cledantec/Cycle-Atlanta-SLaB/Spring2017_implementations/Surface Quality/presentations/Milestone 1.pdf

## LMC 6650: Seeing like a Bike

# Surface Quality

## Milestone 1

Team: Shruti Dalvi | Kristin Hare | Nene Igietseme | Jayanth Mohana Krishna

What to measure | Why we’re measuring it | How (sensor type)
Swerve (rate of deflection) | Recorrecting course to show road obstacles and
potholes
| | Magnetometer / Gyroscope
Vibration | Surface quality (type of surface) | Vibration Sensor / Contact microphone (http://www.digikey.com/product-detail/en/knowles/BU-21771-000/423-1004-ND/458515)
Location | Location of data collected | GPS chip
Directional sound | Ambient noise, surface quality | Array microphones (to be trained)
Incline | Slope of road | Inclinometer
Pressure on handlebars | Physiological measure of stress | Area pressure sensor (https://www.sparkfun.com/products/11207)

## Primary Measures

What to measure | Why we’re measuring it | How (sensor type)
Speed | Cyclist behavior could reflect how
| critical the condition of the road is (related to traffic speed or road obstacles) | Accelerometer / Hall effect sensor / Reid Switch
Temperature | Could be related to road conditions (potential for ice, long stretches of hot pavement, etc.)
Temperature and humidity sensor (single package) (https://www.sparkfun.com/products/10167)
Humidity | Weather (raining), could be used to back up data on cyclist actions (swerving)
Direction | To detect the side of the road (since GPS will only give absolute location)

Accelerometer / Gyroscope (https://www.sparkfun.com/products/retired/10724)

Gear Number | Could point to information on incline or cyclist exertion level

Rheostat / variable resistor (http://www.digikey.com/products/en/potentiometers-variable-resistors/slide-potentiometers/78)

## Secondary Measures

## Shopping List

Option 1:

- Matrix One Creator Edition ($99)
- Raspberry Pi 3 ($35)
- Arduino Mega*
- Powered USB hub for dev
- External battery pack*
- Inclinometer
- GPS chip
- Pressure sensors for handlebars
- Low-sensitivity vibration sensors

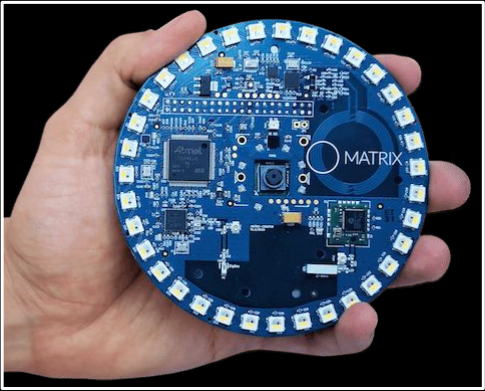
[picture p22: figure]

Option 2: Buy individual sensors | Matrix One Creator Edition - Integrated sensors for RPi

## Miscellaneous parts

- ⅛” cube magnets, 20x
- M/M, M/F, F/F patch cables, 20x
- Hair bands, 20x
- Cable ties, 20x
- Breadboards to prototype
- 5V 2A+ power supply, MicroUSB
- MicroSD card, 16 GB
- 3D printed parts (GVU lab)
- ???

### Alternate method (to be explored):

- 20mW 3-5V laser diode, paired with USB camera
- Machine Vision to observe changes in laser pattern on surface) - apparently not hard to do on OpenCV/Raspberry Pi
- Most obvious way, but potentially risky - can only get surface quality

Sensor Location | Raspberry Pi +

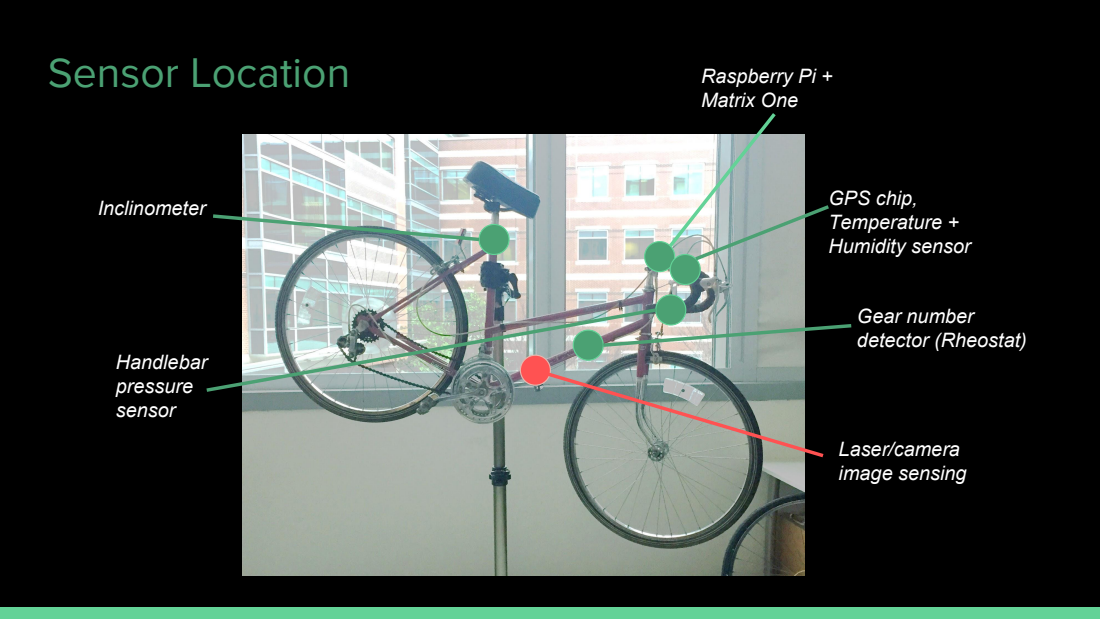
[picture p23: page 6]
Matrix One; Inclinometer; Gear number detector (Rheostat); GPS chip, Temperature + Humidity sensor; Handlebar pressure sensor; Laser/camera image sensing

## Progress

- Tested high-sensitivity vibration sensor, discovered we needed much lower sensitivity
- Reclassified measures as primary and secondary based on feedback from Dr. Watkins
- Reached out to civil engineering students for additional feedback on measures

## To-do

- Sketches - how to interface sensors
- System Architecture (in collaboration with other teams)
- Calibration parameters
