cledantec/Cycle-Atlanta-SLaB/Spring2017_implementations/Surface Quality/presentations/Milestone 2.pdf

LMC 6650: Seeing like a Bike

# Surface Quality

Milestone 2

Team: Shruti Dalvi | Kristin Hare | Nene Igietseme | Jayanth Mohana Krishna

Progress: Meeting with Dr. Watkins’ Students

- Talked to Dr. Watkins’ students
- The laser surface quality detector they use is not feasible for this project (size of a microwave oven & 100,000 dollars)

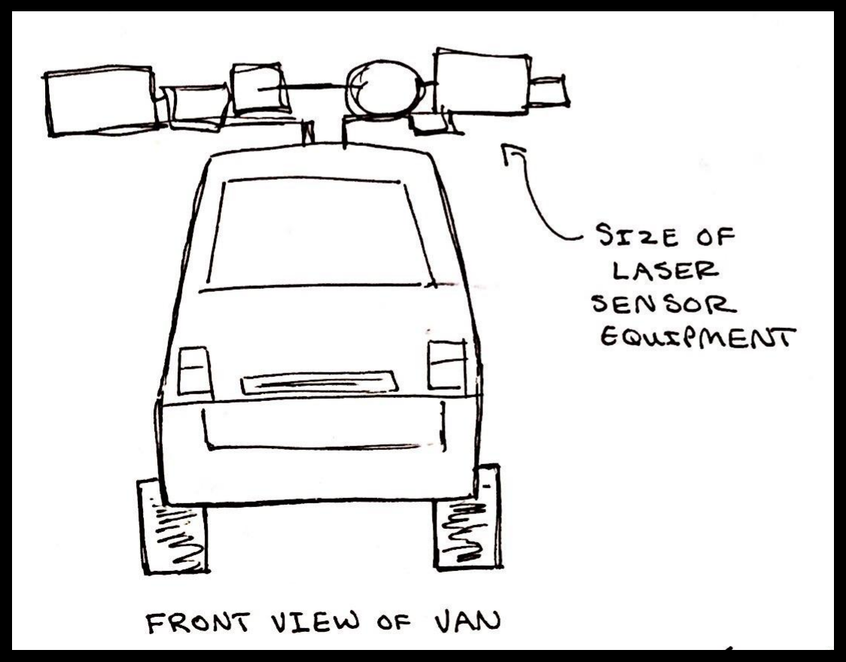
[picture p24: figure]

Laser measures distance from laser to pavement; is not affected by light or reflection like a camera would be

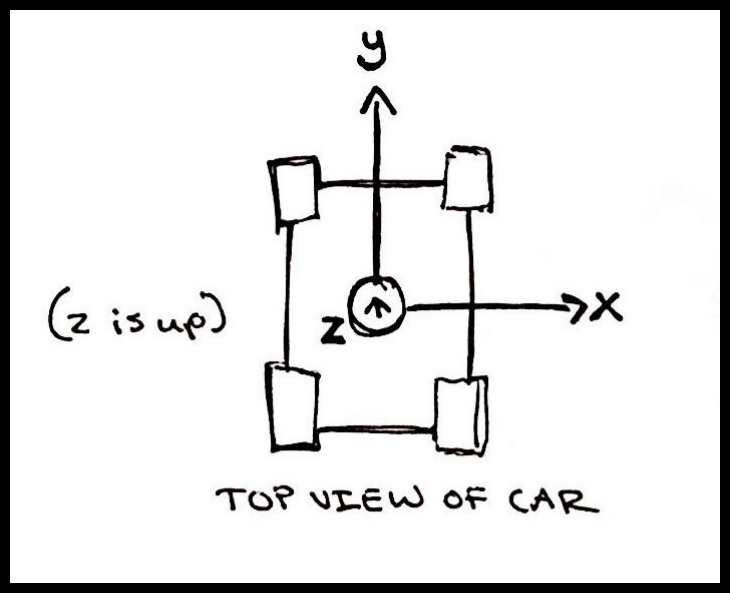
[picture p25: figure]

To calculate magnitude of
deviation in bumps: (x²

+ y²

+ z²
) =
t

2
(do not use square root because of powerful calculations needed)

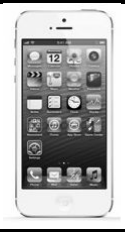
[picture p26: figure]

Phone Location Services
could be better than GPS
chip because based on
satellite, server towers, & wifi

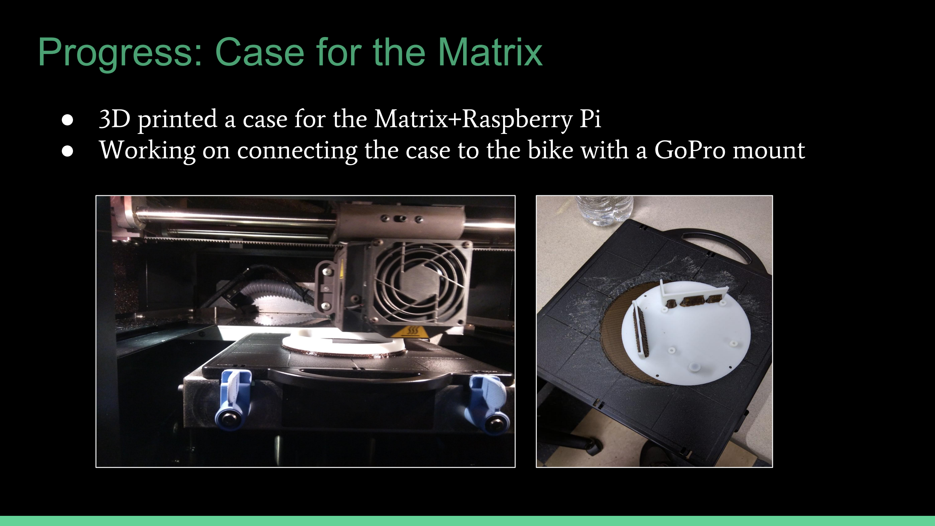
[picture p27: page 3]

Progress: Case for the Matrix

- 3D printed a case for the Matrix+Raspberry Pi
- Working on connecting the case to the bike with a GoPro mount

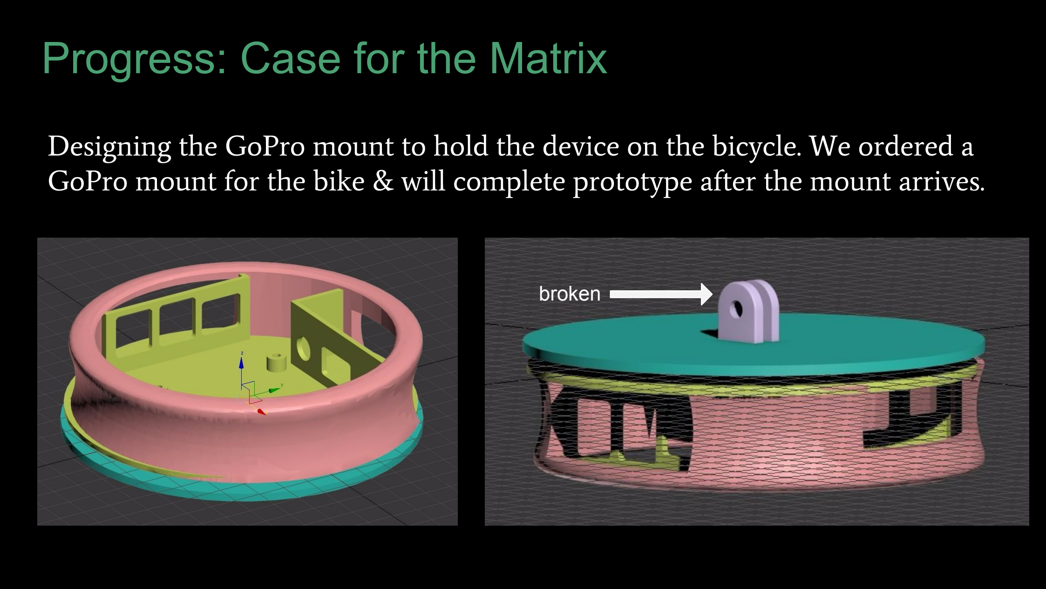
[picture p28: page 4]

broken

Designing the GoPro mount to hold the device on the bicycle. We ordered a GoPro mount for the bike & will complete prototype after the mount arrives.

Progress: Case for the Matrix

Progress

- Accelerometer and
gyroscope support for
Matrix arrived last week;
that is implemented - we
are getting raw JSON
values
- Dr. Watkins’ students
suggested logging
timestamp, GPS and
x

2+y²+z²
values if it is
greater than threshold t²
,
for purposes of efficiency.

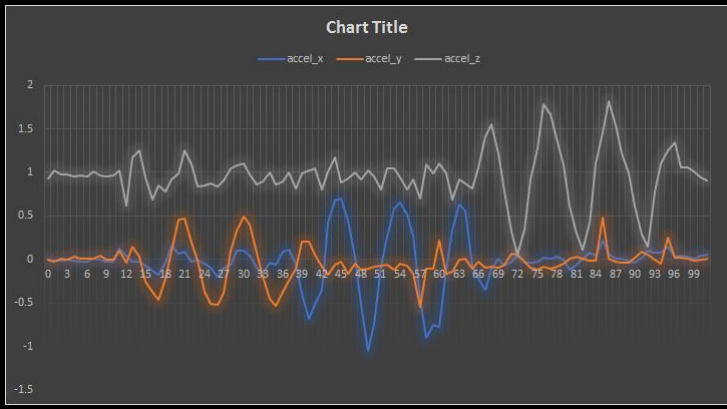
[picture p29: figure]

Currently getting accelerometer, gyroscope and magnetometer data, coordinated with Air Quality team to get GPS data

Roadblocks:

- Laser surface quality detector Dr. Watkins’ students are using is very out of budget
- 3D model’s GoPro mount broke
- We will glue it with epoxy & possibly some wooden stilts once we receive the GoPro bike mount (ETA March 2nd)

Questions to Answer:

- Got accelerometer/gyroscope/magnetometer data - need to determine appropriate interval for surface quality measurements
- Implemented serial interface for Pi - might have to interface with Arduino because Pi’s Linux kernel is not real-time

Future Direction

- Determine appropriate intervals to collect data
- Determine & assign specific values to compare data against (ex: what constitutes a pothole, what constitutes a turn vs. a swerve)
- Implement a centralized server to collect data (will have to coordinate with other teams)
- Investigate optical measurements (OpenCV)
- Investigate acoustic measurements (will need to buy a surface microphone to investigate its data stream)
