cledantec/Cycle-Atlanta-SLaB/DSSG2017_data/graphs/0719_being_passed_vehicle.png

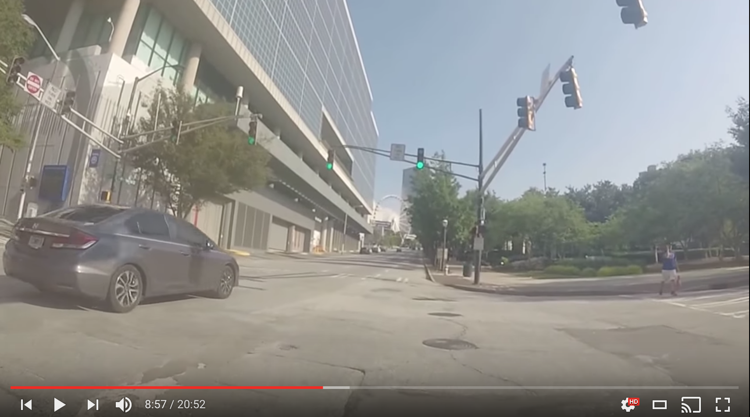
DSSG2017_data/graphs/0719_being_passed_vehicle.png
