cledantec/Cycle-Atlanta-SLaB/DSSG2017_data/graphs/0719_signature_riding.png

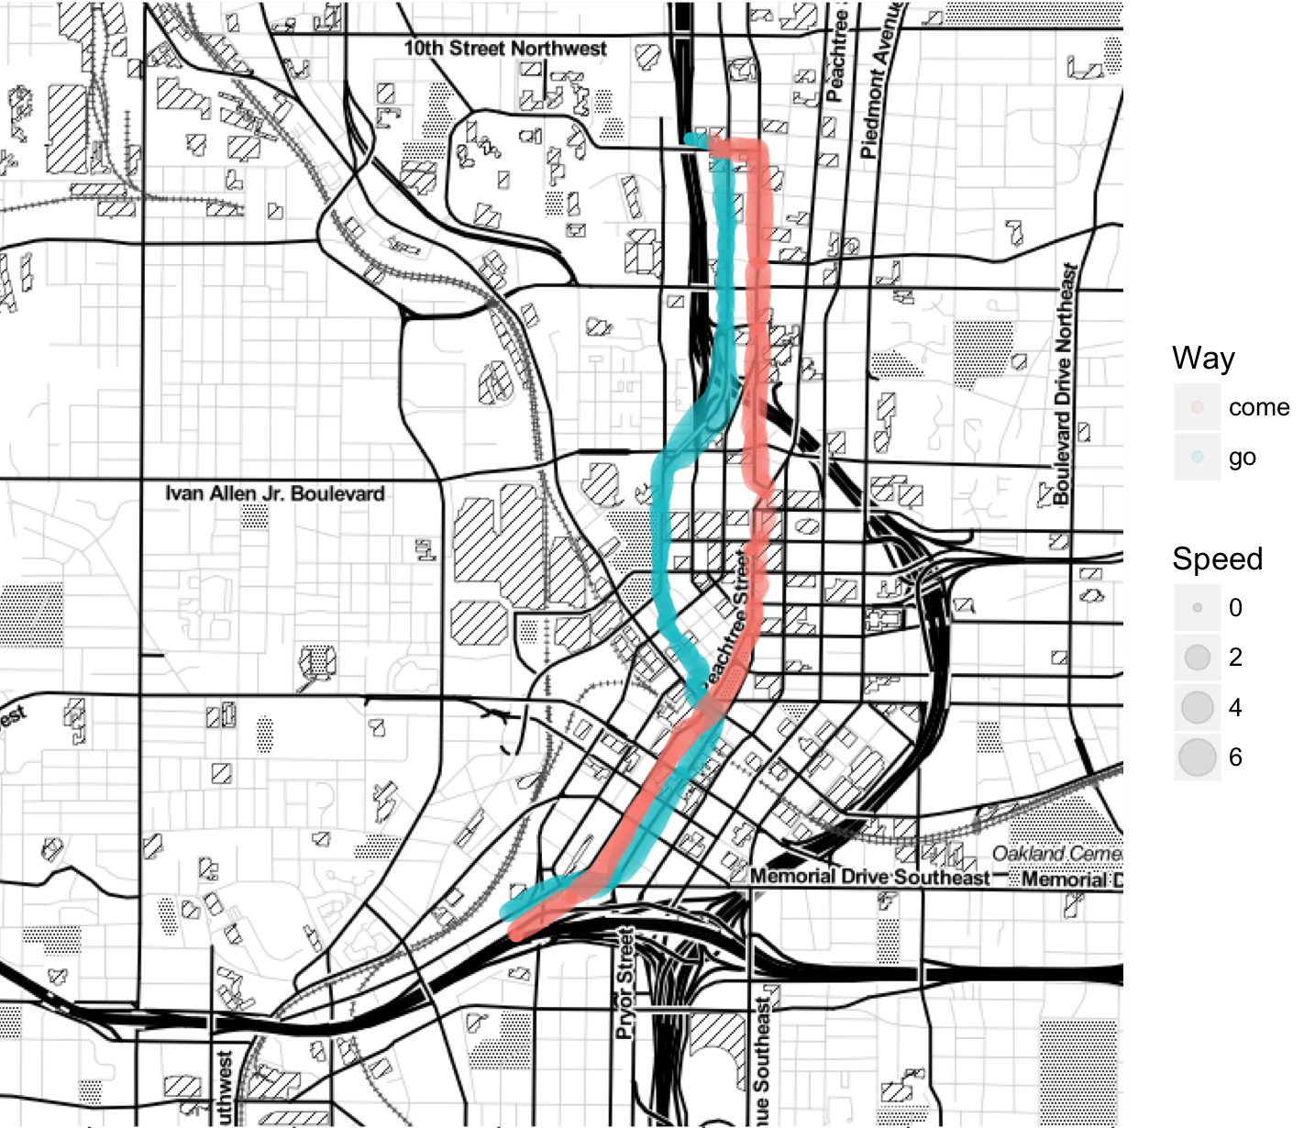
DSSG2017_data/graphs/0719_signature_riding.png
