cledantec/Cycle-Atlanta-SLaB/DSSG2017_data/graphs/0719_street_parking.png

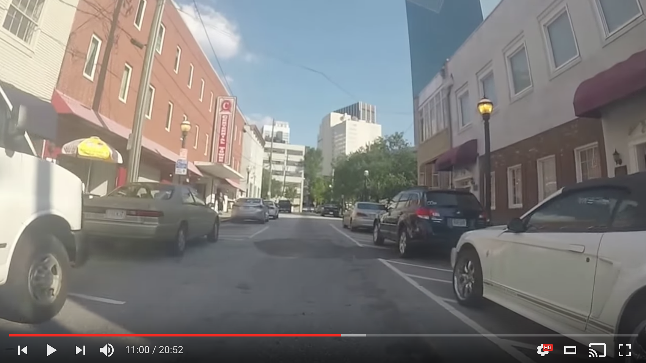
DSSG2017_data/graphs/0719_street_parking.png
