cledantec/Cycle-Atlanta-SLaB/DSSG2017_data/graphs/0720_Noel.png

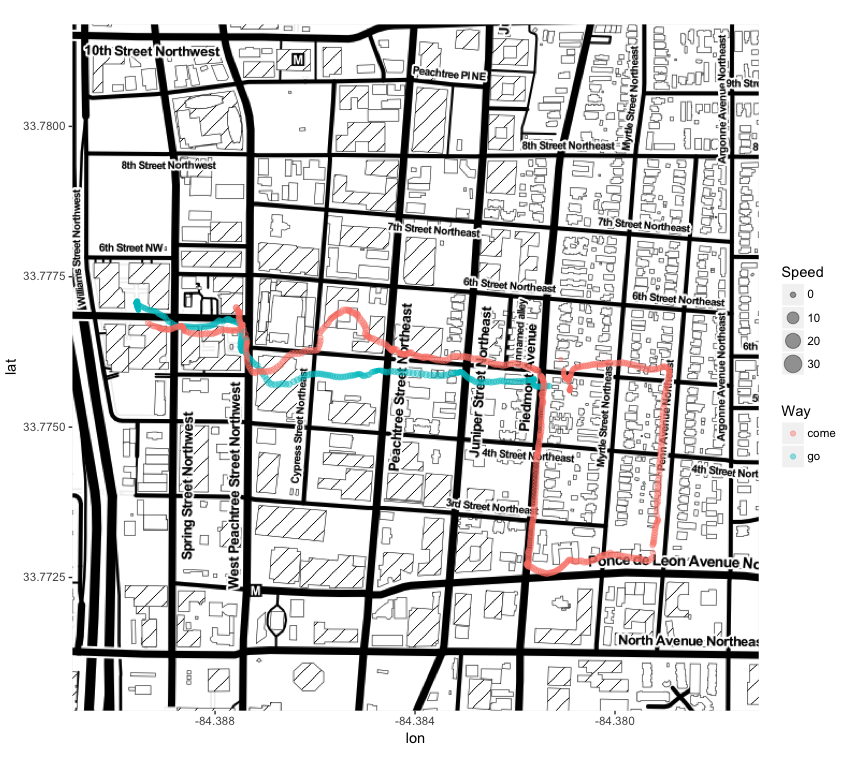
DSSG2017_data/graphs/0720_Noel.png
