cledantec/Cycle-Atlanta-SLaB/DSSG2017_data/graphs/Accelerometer.png

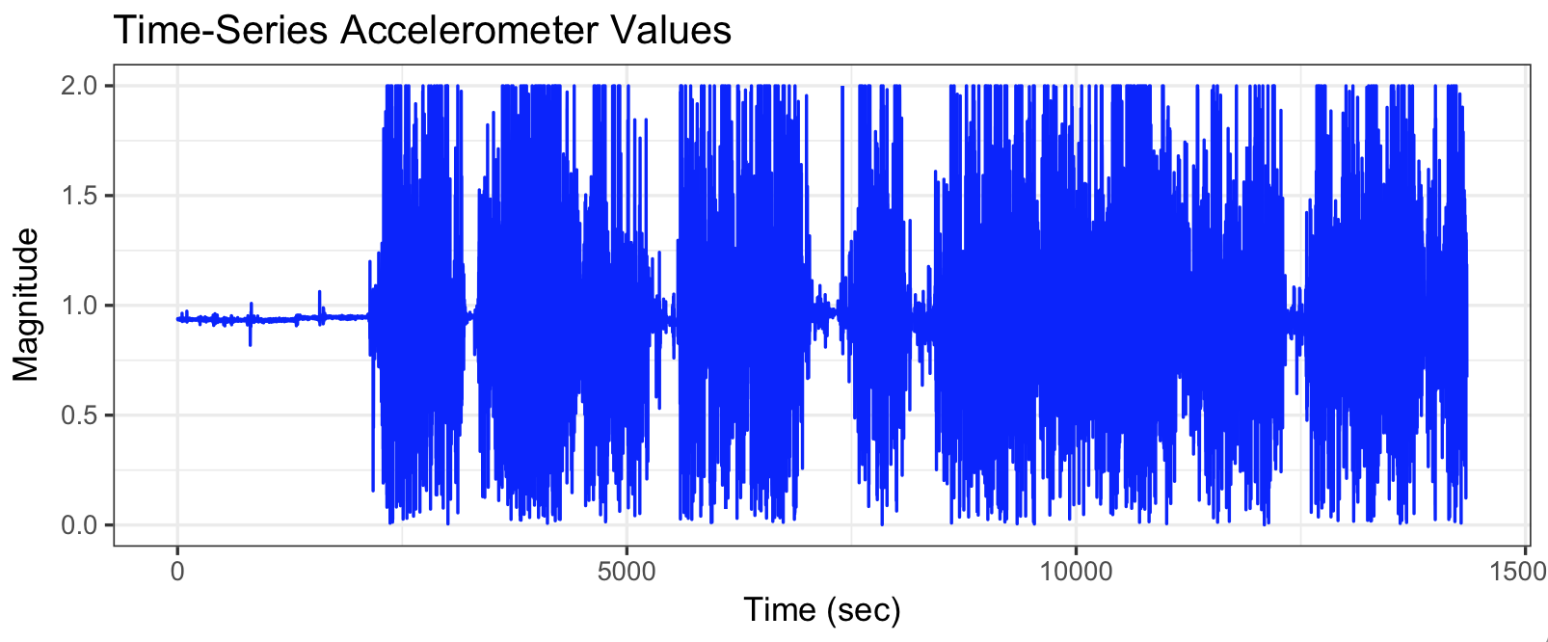
DSSG2017_data/graphs/Accelerometer.png
