cledantec/Cycle-Atlanta-SLaB/DSSG2017_data/graphs/close_up.png

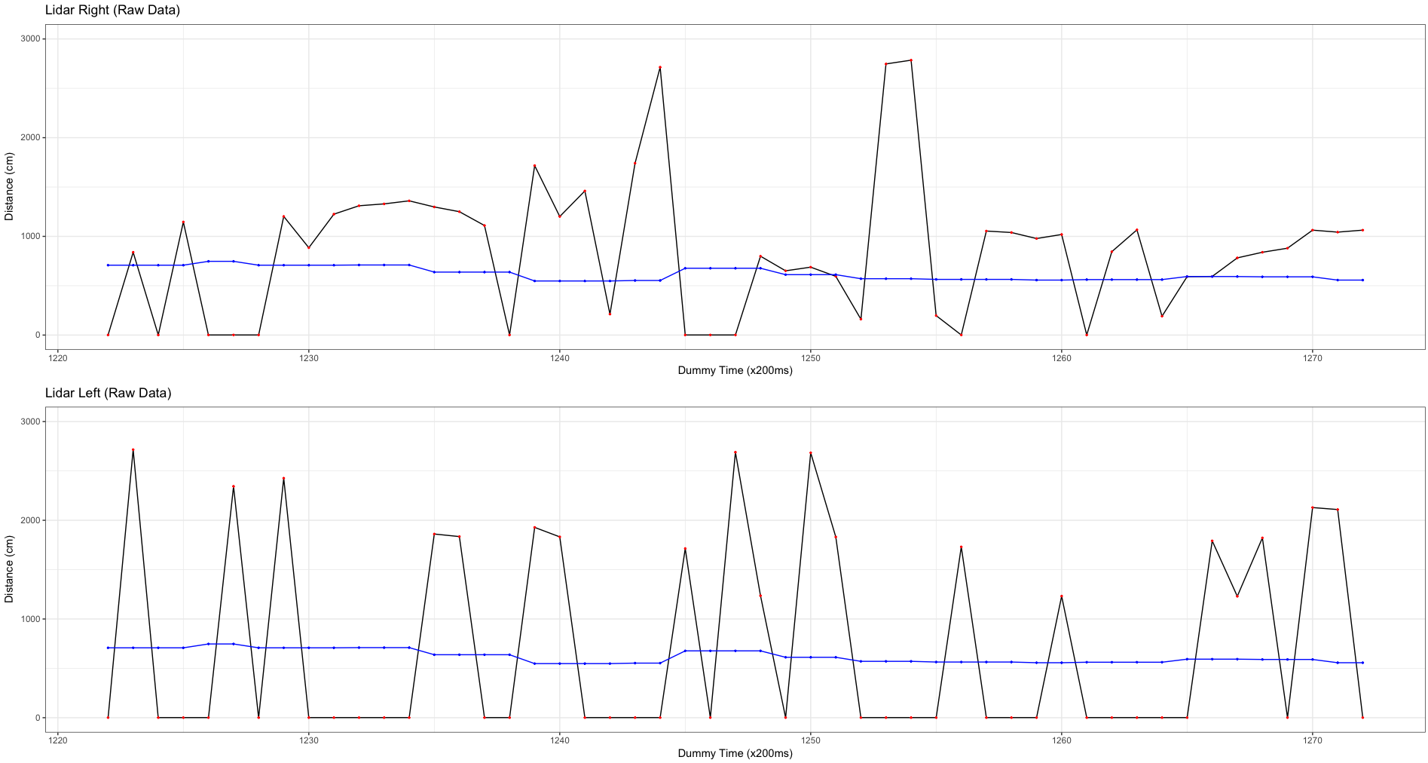
DSSG2017_data/graphs/close_up.png
