cledantec/Cycle-Atlanta-SLaB/DSSG2017_data/graphs/Gas.png

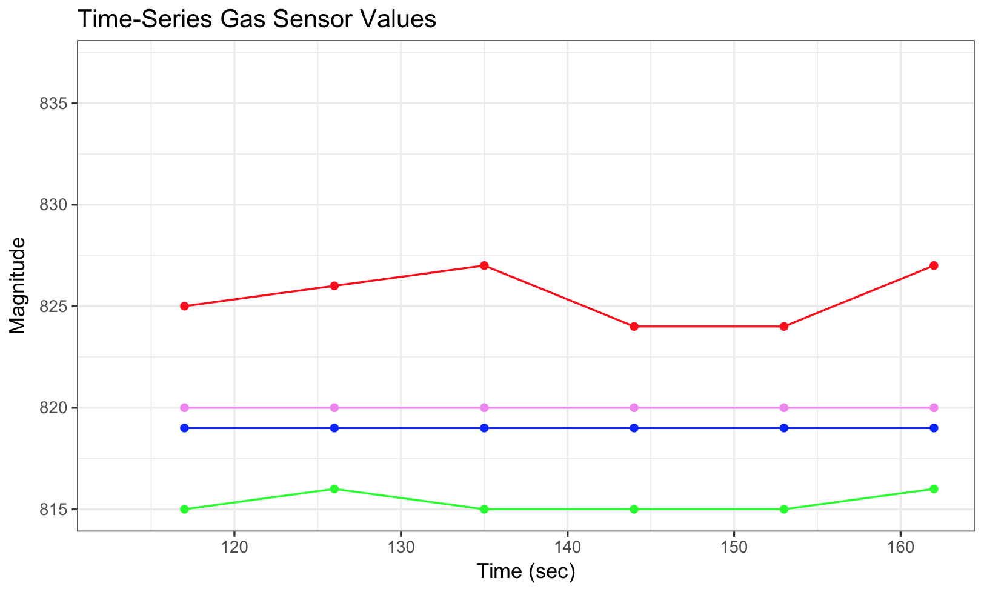
DSSG2017_data/graphs/Gas.png
