cledantec/Cycle-Atlanta-SLaB/DSSG2017_data/graphs/Gas_board5.png

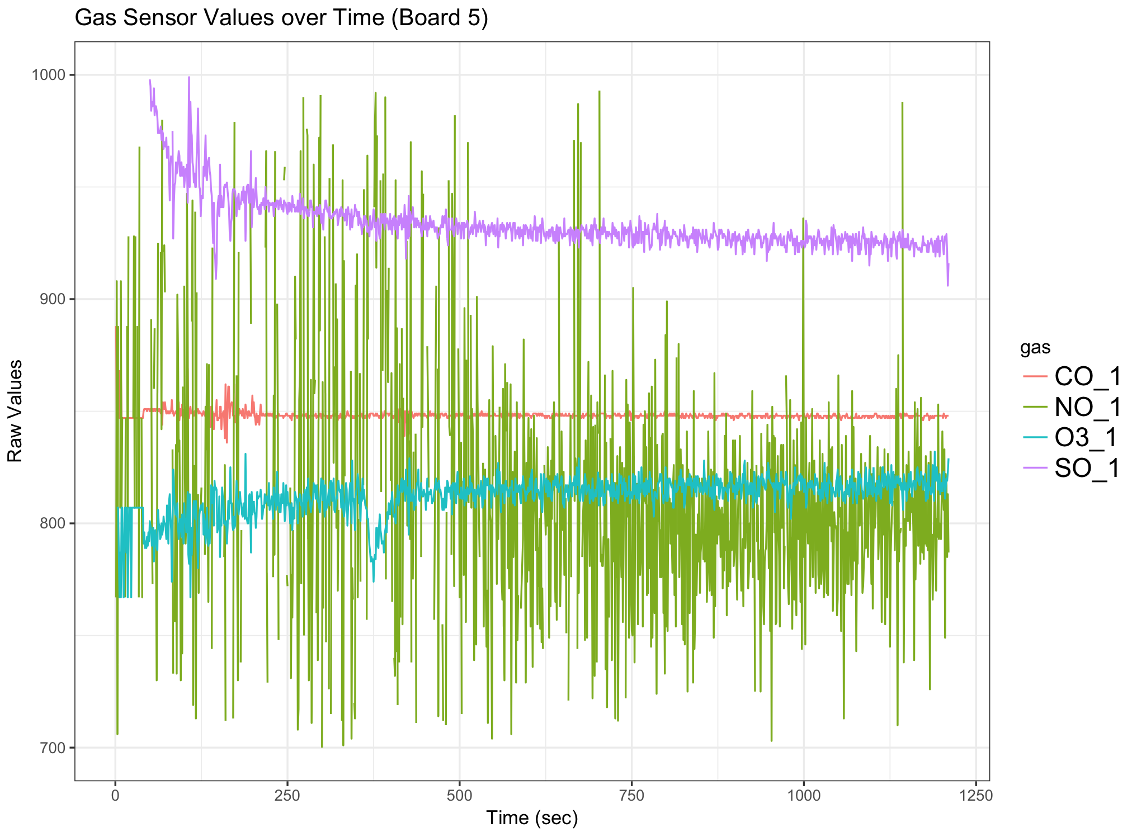
DSSG2017_data/graphs/Gas_board5.png
