cledantec/Cycle-Atlanta-SLaB/DSSG2017_data/graphs/gaussian_sonal_eg.png

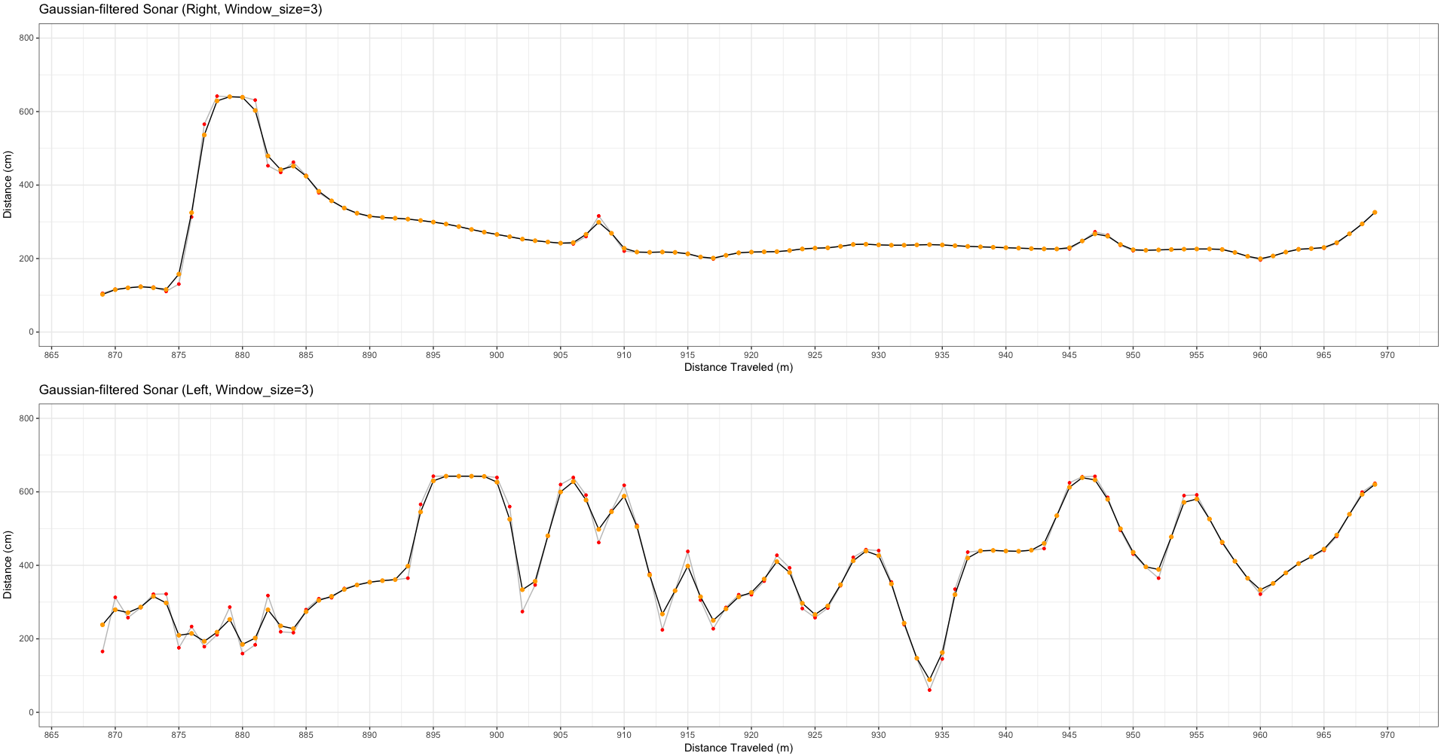
DSSG2017_data/graphs/gaussian_sonal_eg.png
