cledantec/Cycle-Atlanta-SLaB/DSSG2017_data/graphs/gaussian_total.png

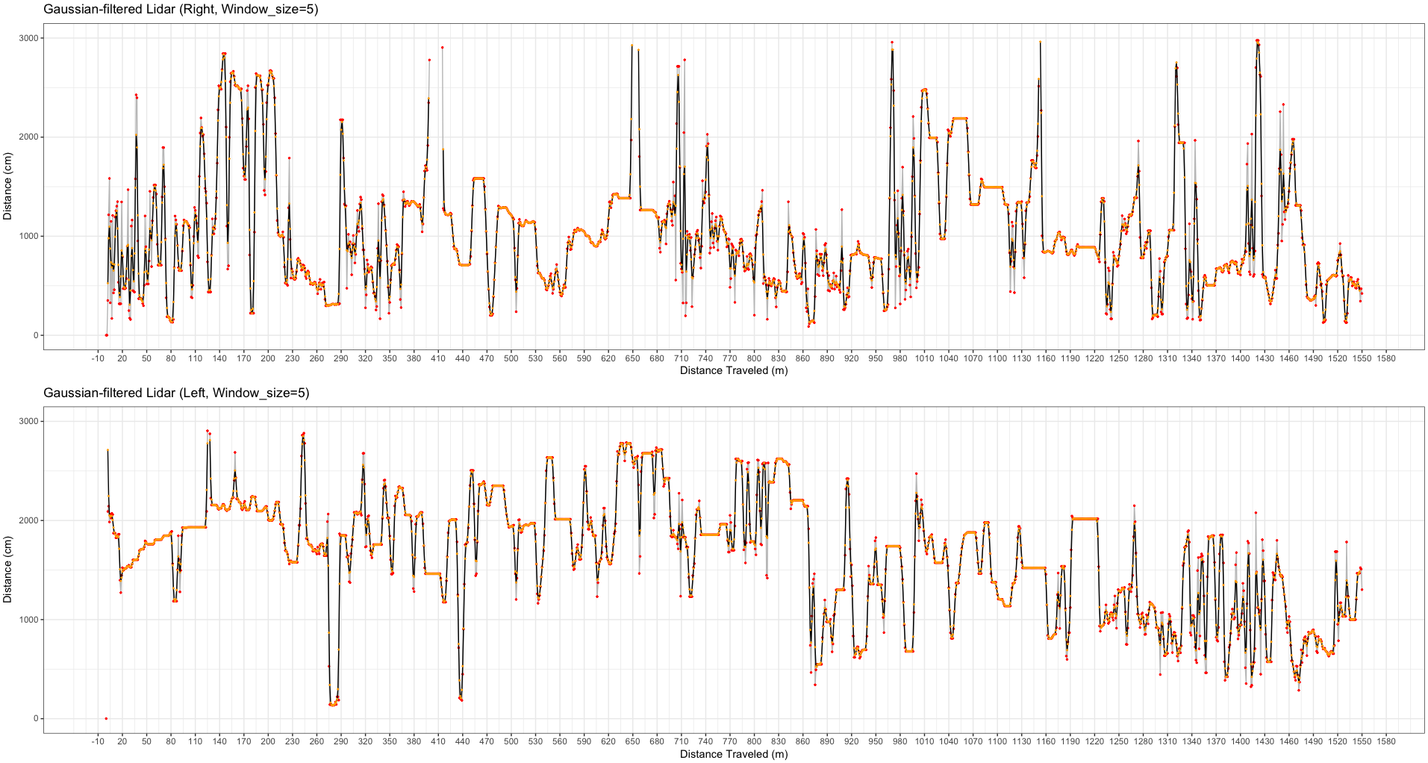
DSSG2017_data/graphs/gaussian_total.png
