cledantec/Cycle-Atlanta-SLaB/DSSG2017_data/graphs/gps_map.png

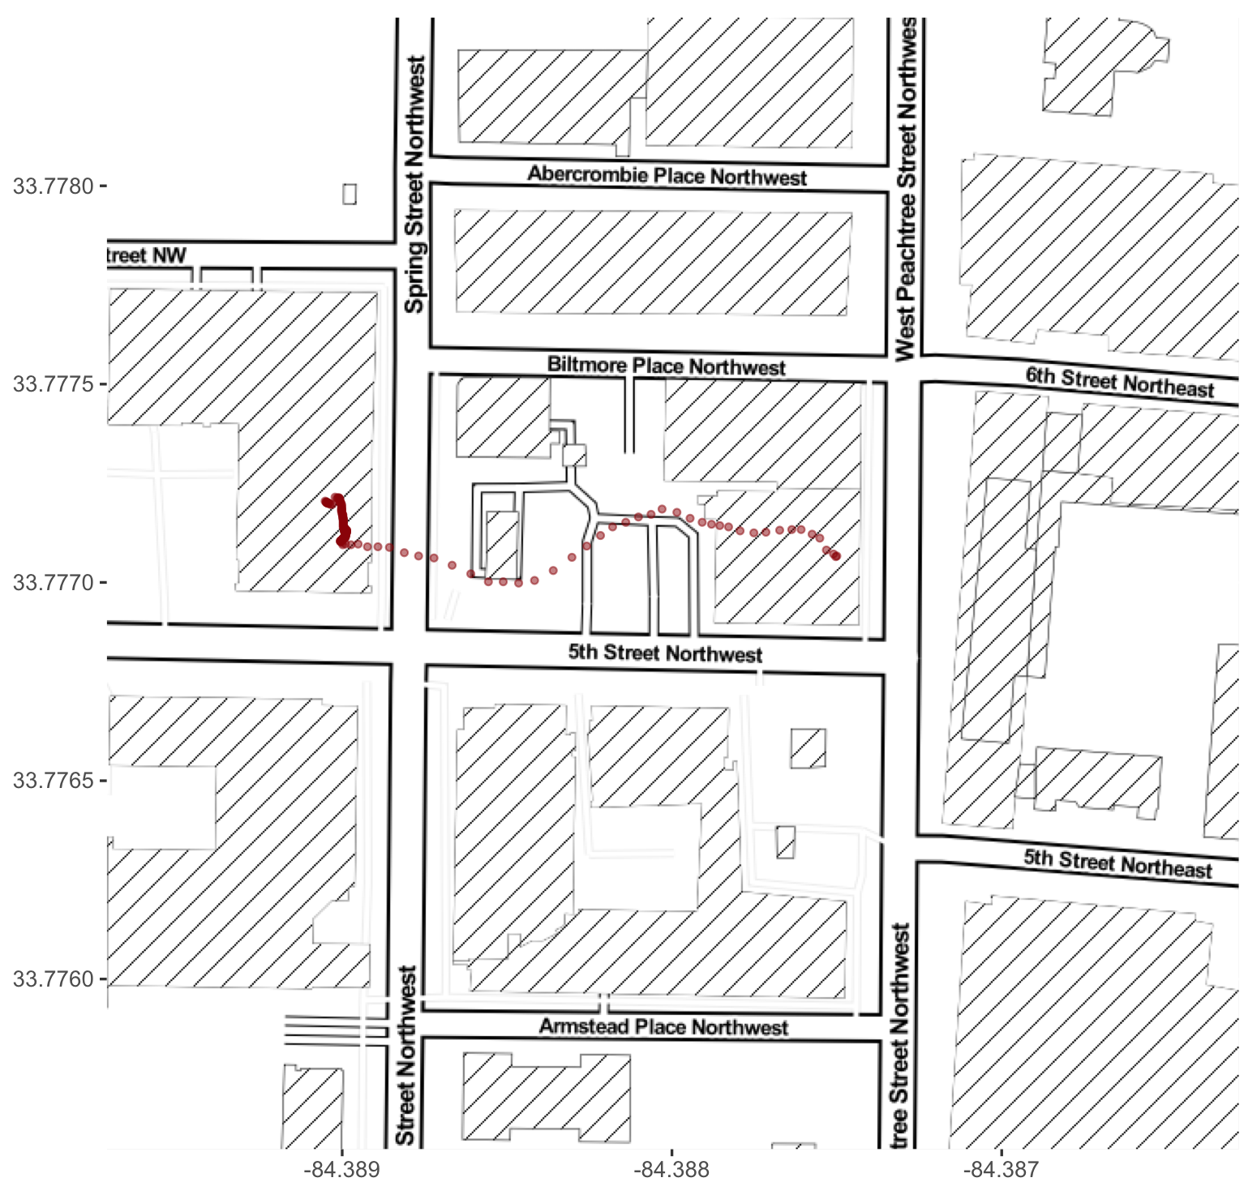
DSSG2017_data/graphs/gps_map.png
