cledantec/Cycle-Atlanta-SLaB/DSSG2017_data/graphs/Gyroscope.png

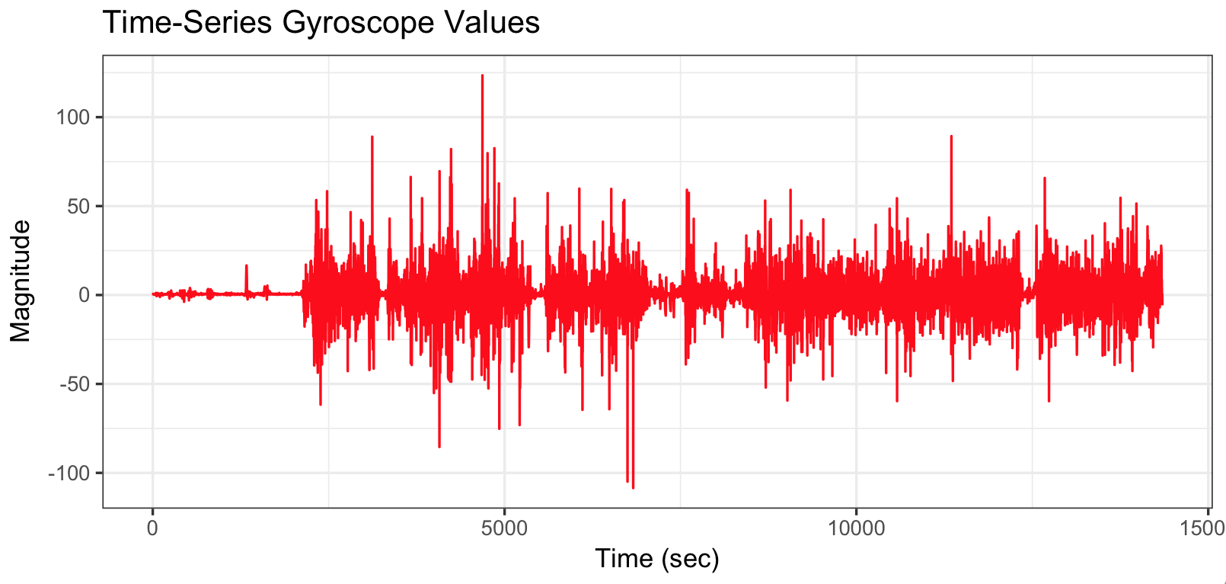
DSSG2017_data/graphs/Gyroscope.png
