cledantec/Cycle-Atlanta-SLaB/DSSG2017_data/graphs/Jaremy_Mariam.jpg

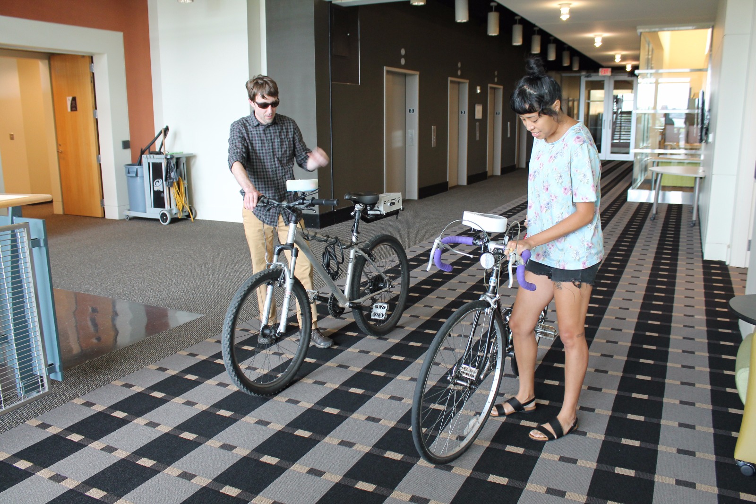
DSSG2017_data/graphs/Jaremy_Mariam.jpg
