cledantec/Cycle-Atlanta-SLaB/DSSG2017_data/graphs/Javier_0722.png

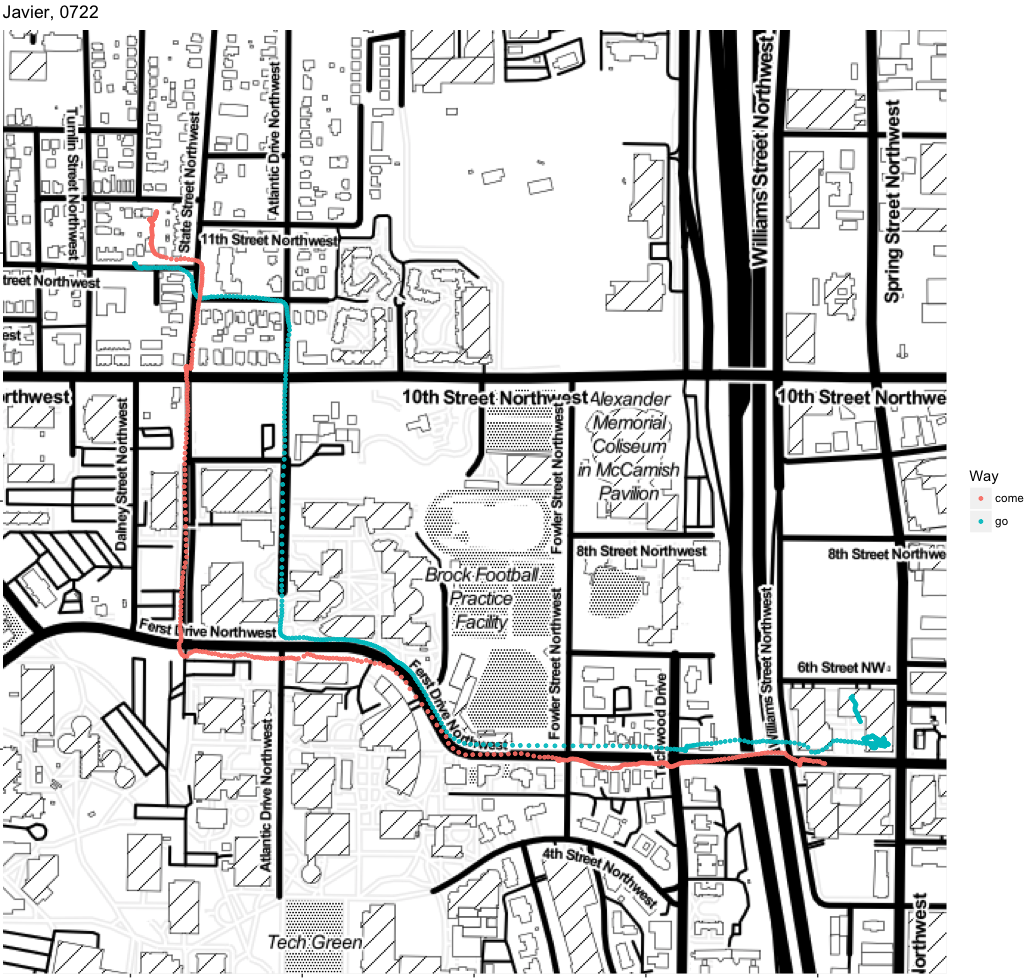
DSSG2017_data/graphs/Javier_0722.png
