cledantec/Cycle-Atlanta-SLaB/DSSG2017_data/graphs/Jeremy_0721.png

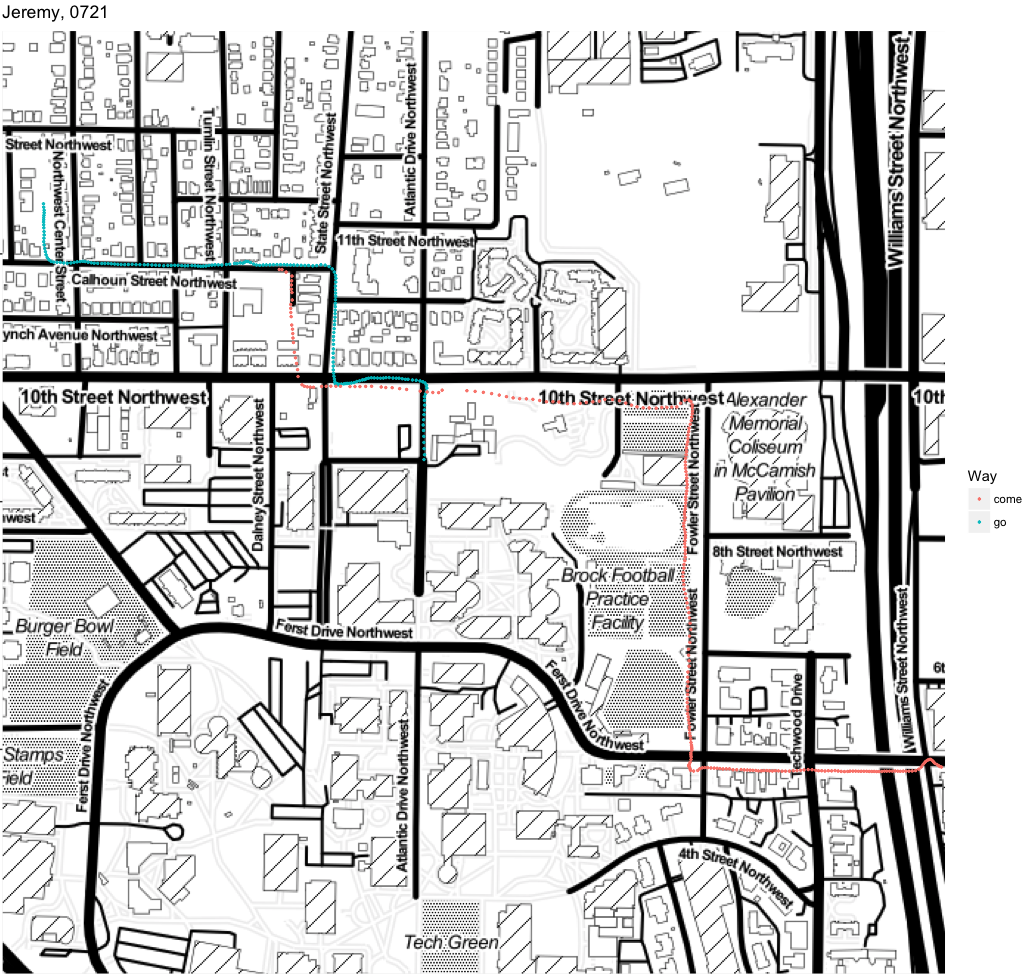
DSSG2017_data/graphs/Jeremy_0721.png
