cledantec/Cycle-Atlanta-SLaB/DSSG2017_data/graphs/left_lidar_video_time.png

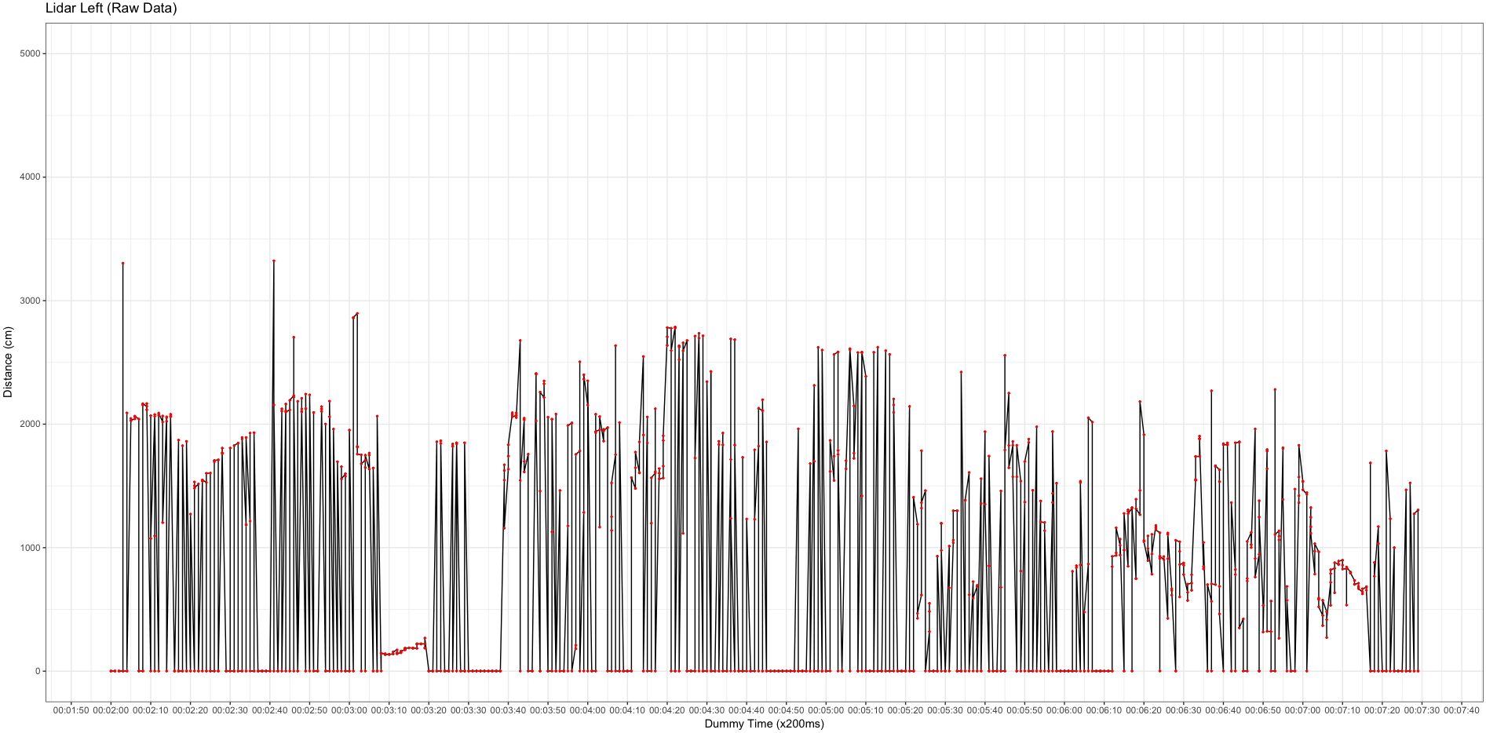
DSSG2017_data/graphs/left_lidar_video_time.png
