cledantec/Cycle-Atlanta-SLaB/DSSG2017_data/graphs/Left_sonar_lidar.png

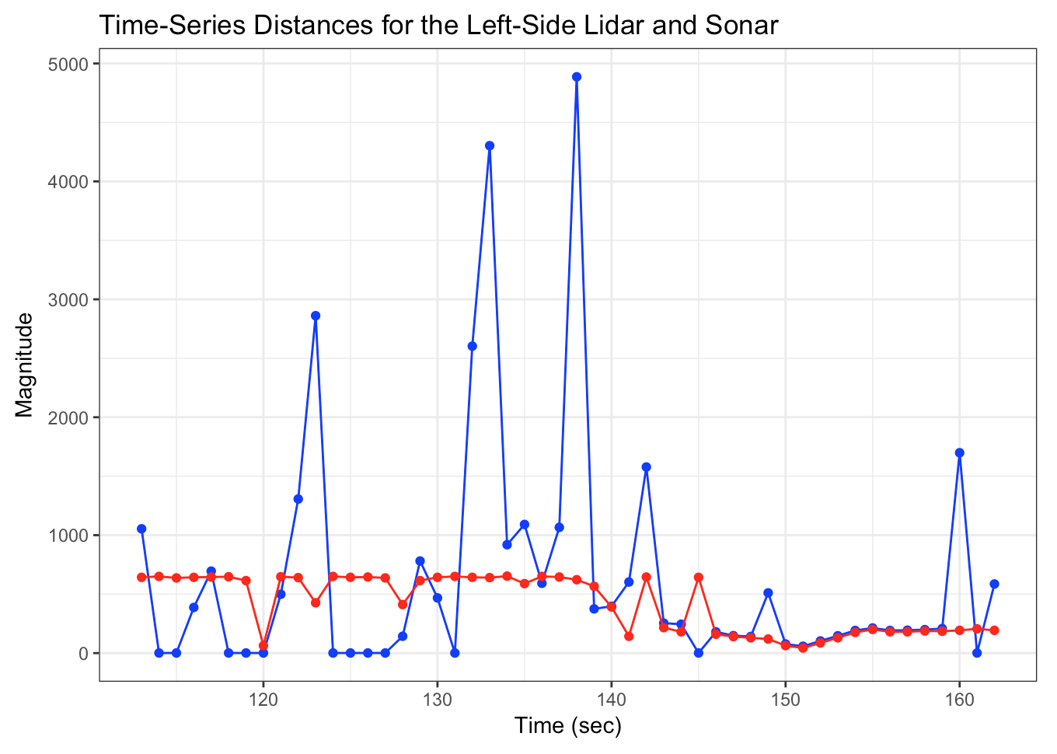
DSSG2017_data/graphs/Left_sonar_lidar.png
