cledantec/Cycle-Atlanta-SLaB/DSSG2017_data/graphs/lidar_distance_based.png

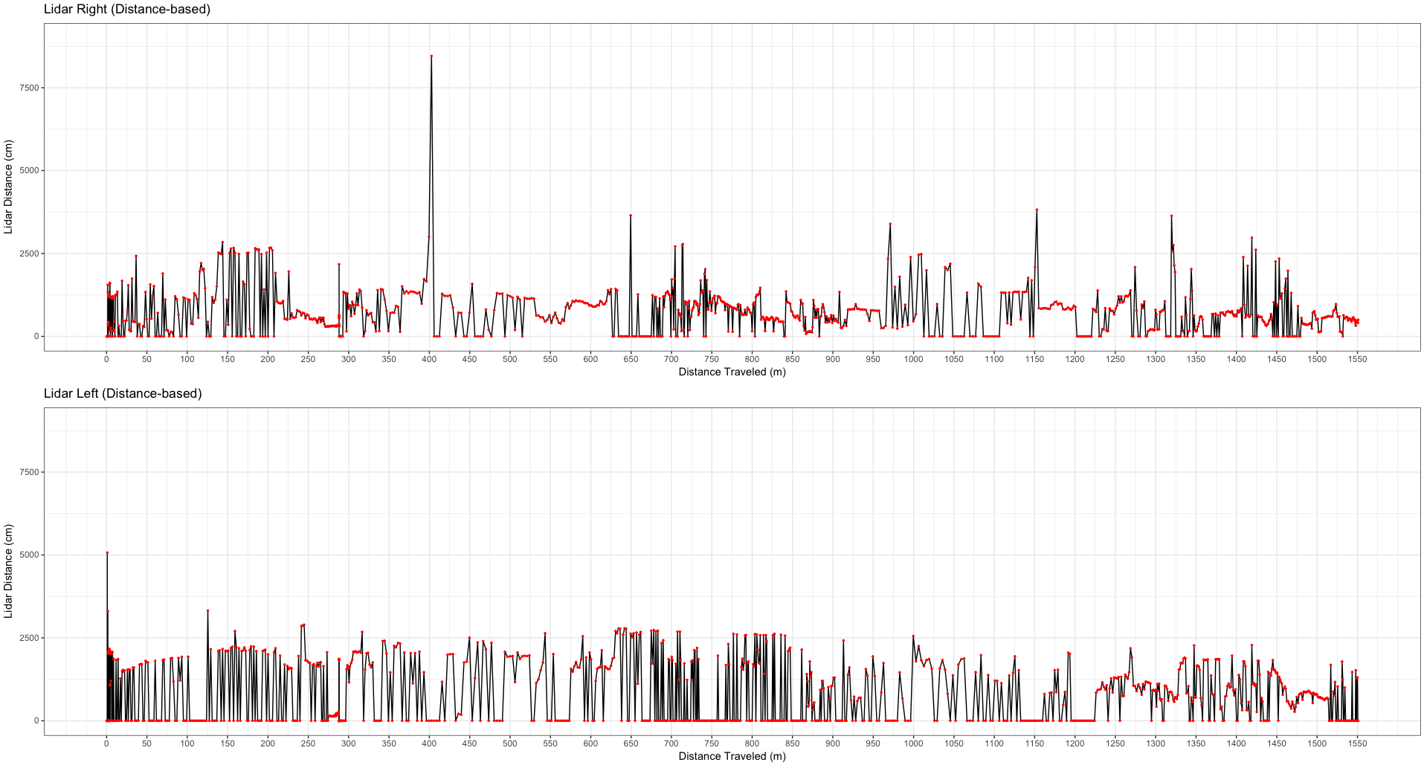
DSSG2017_data/graphs/lidar_distance_based.png
