cledantec/Cycle-Atlanta-SLaB/DSSG2017_data/graphs/lidar_interpoliation_close_up.png

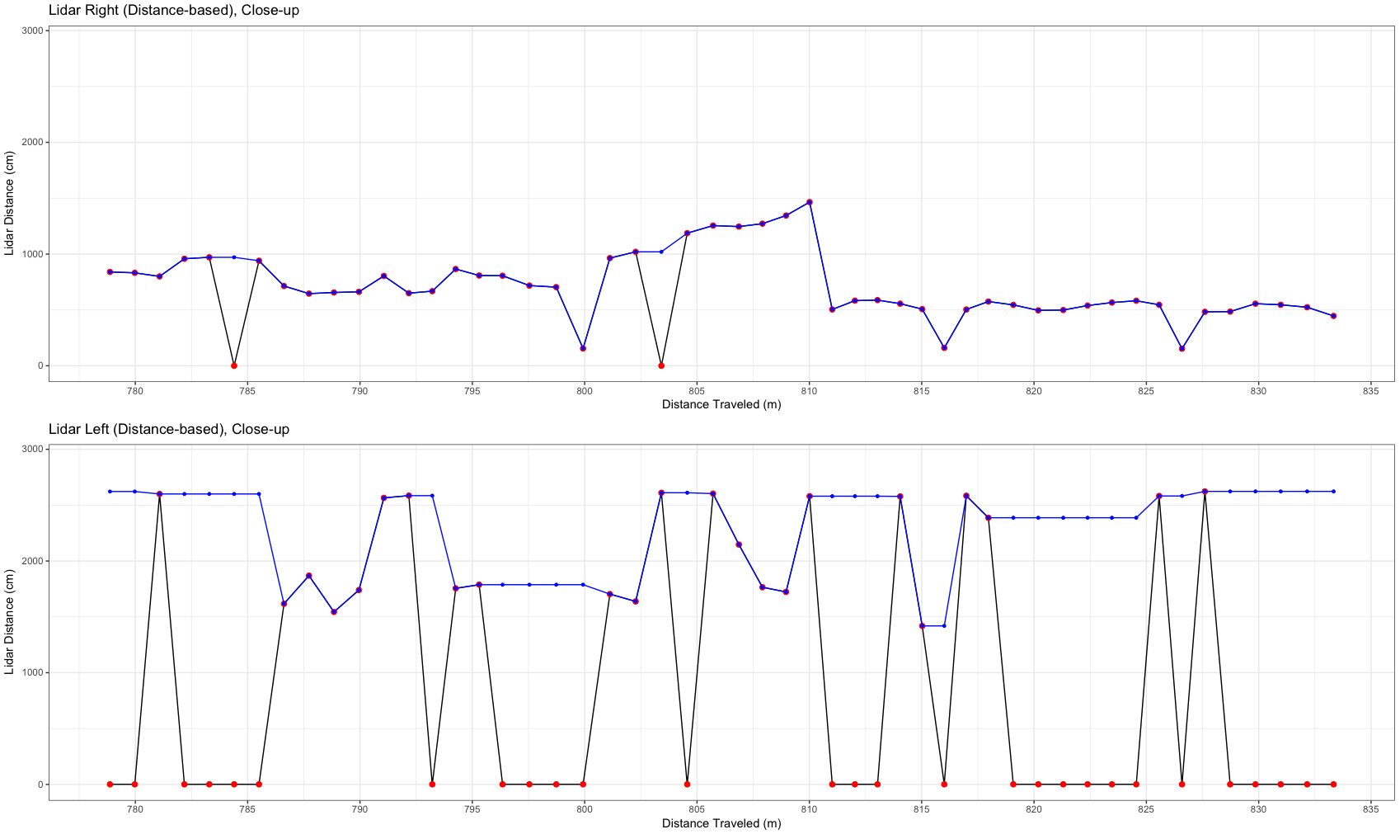
DSSG2017_data/graphs/lidar_interpoliation_close_up.png
