cledantec/Cycle-Atlanta-SLaB/DSSG2017_data/graphs/lidars.png

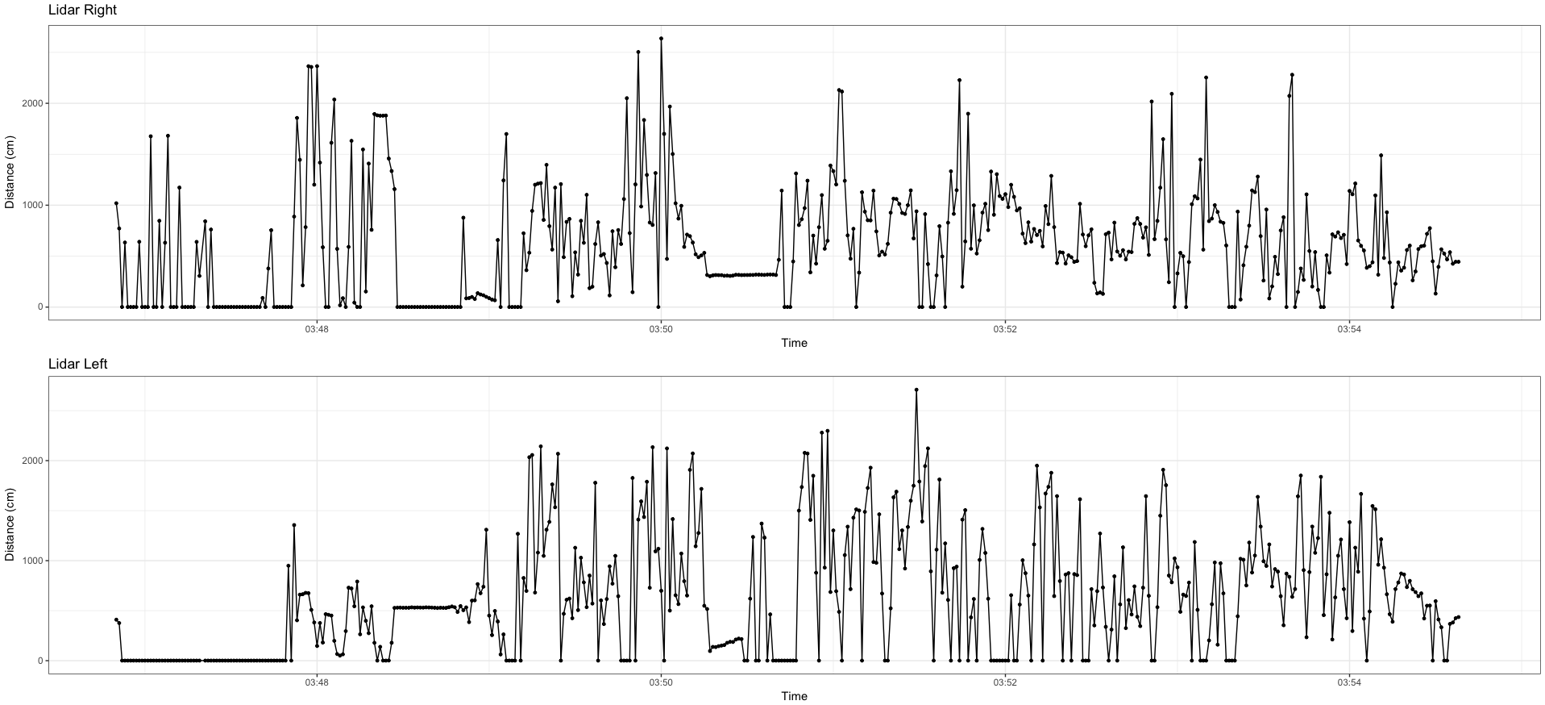
DSSG2017_data/graphs/lidars.png
