cledantec/Cycle-Atlanta-SLaB/DSSG2017_data/graphs/lidars_raw.png

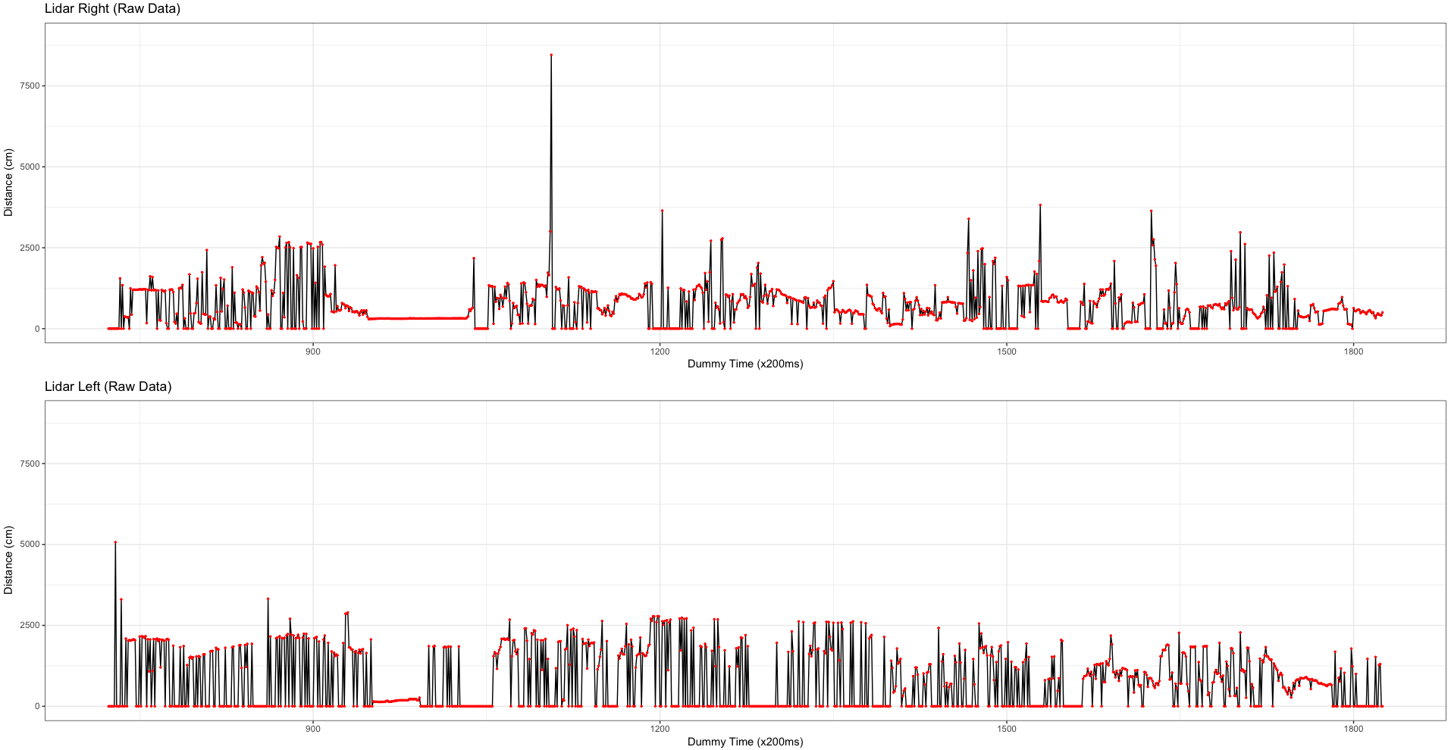
DSSG2017_data/graphs/lidars_raw.png
