cledantec/Cycle-Atlanta-SLaB/DSSG2017_data/graphs/lidars_video_time.png

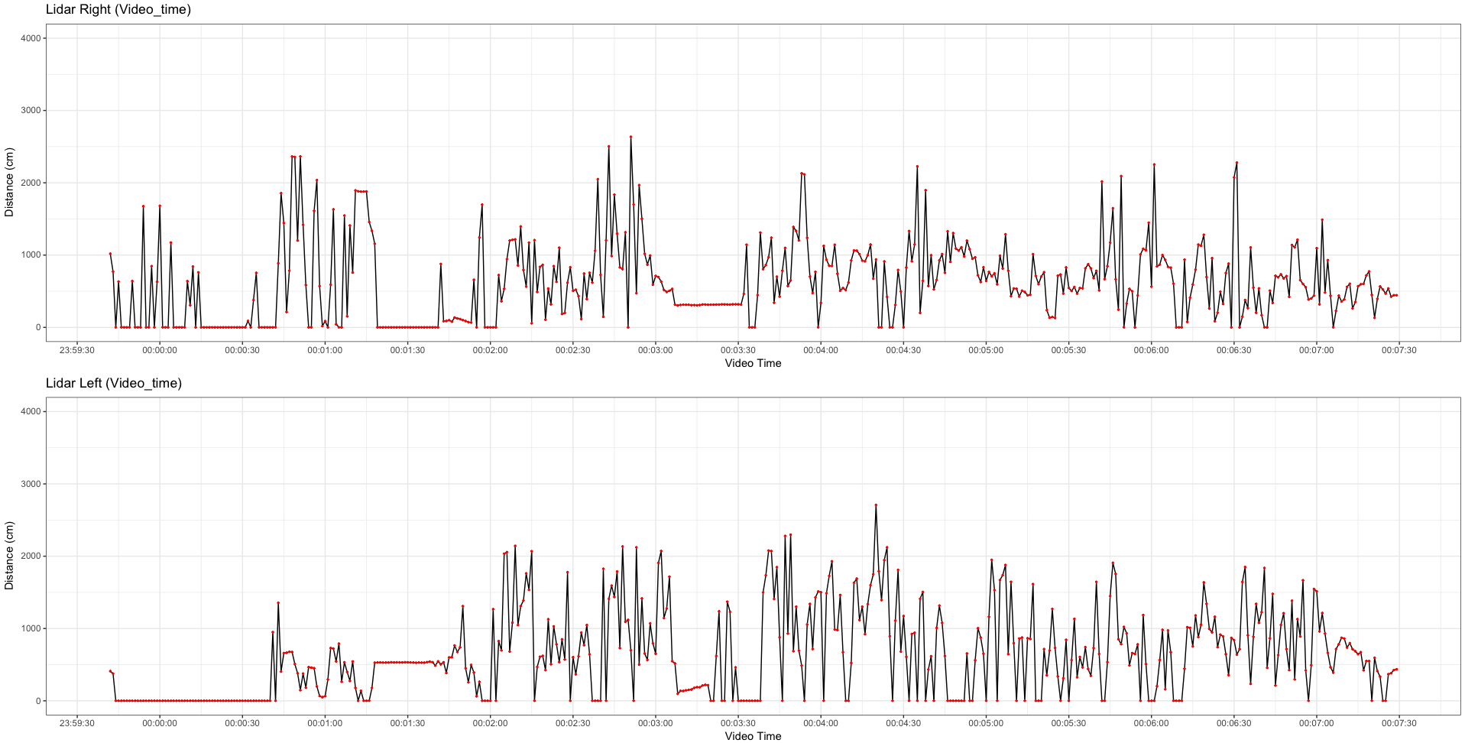
DSSG2017_data/graphs/lidars_video_time.png
