cledantec/Cycle-Atlanta-SLaB/DSSG2017_data/graphs/Mariam_0720_1.png

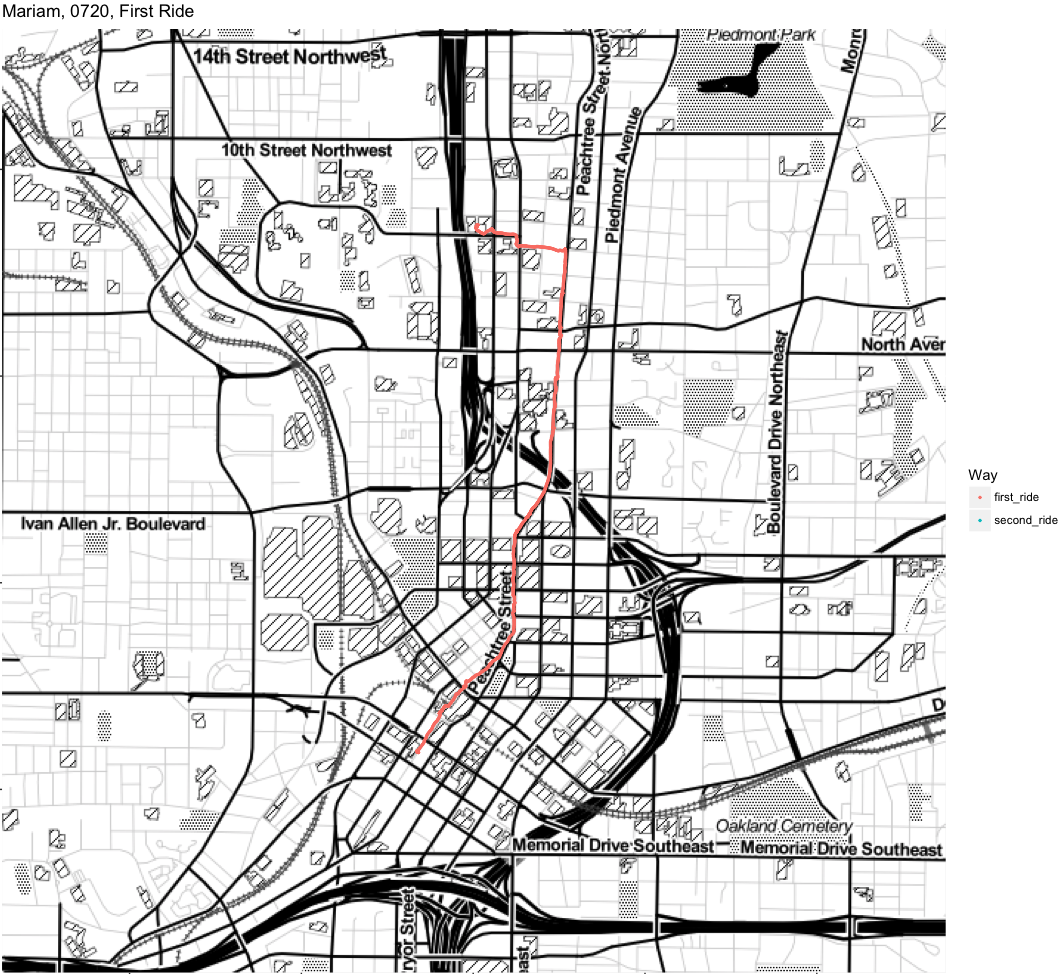
DSSG2017_data/graphs/Mariam_0720_1.png
