cledantec/Cycle-Atlanta-SLaB/DSSG2017_data/graphs/Mariam_0720_2.png

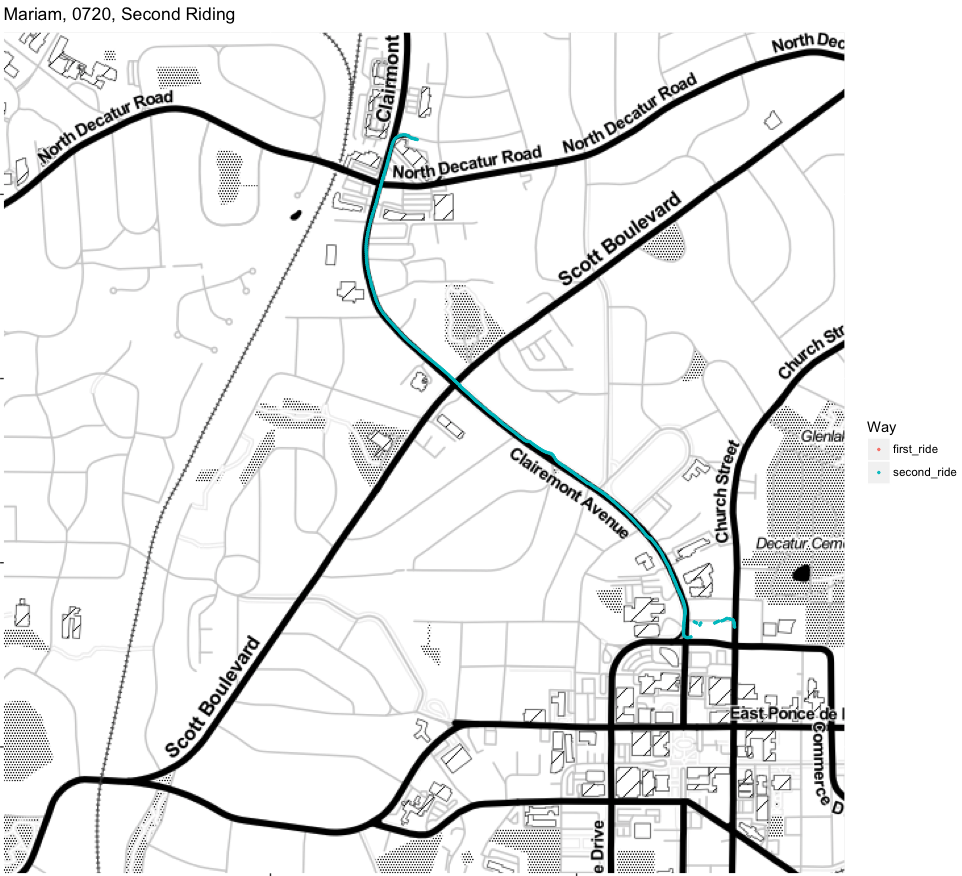
DSSG2017_data/graphs/Mariam_0720_2.png
