cledantec/Cycle-Atlanta-SLaB/DSSG2017_data/graphs/official_gas.png

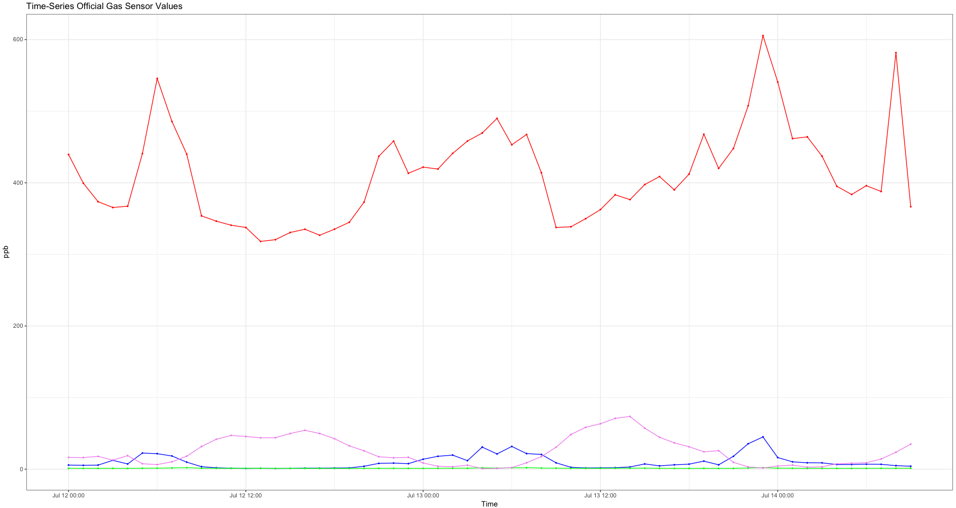
DSSG2017_data/graphs/official_gas.png
