cledantec/Cycle-Atlanta-SLaB/DSSG2017_data/graphs/passing_vehicle_freq_sig.png

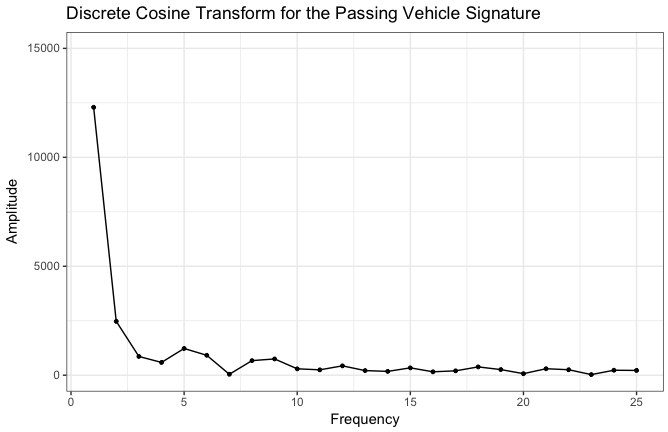
DSSG2017_data/graphs/passing_vehicle_freq_sig.png
