cledantec/Cycle-Atlanta-SLaB/DSSG2017_data/graphs/passing_vehicle_temporal.png

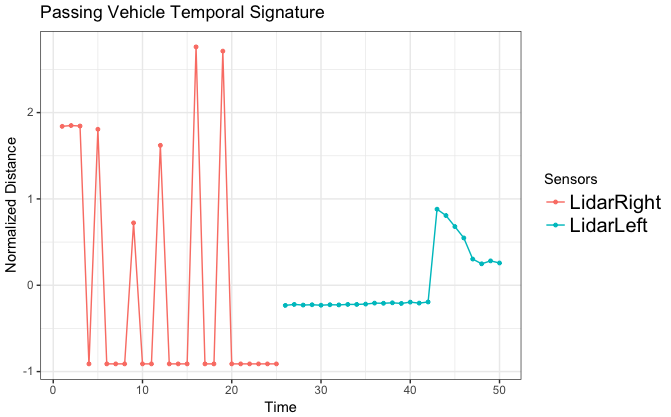
DSSG2017_data/graphs/passing_vehicle_temporal.png
