cledantec/Cycle-Atlanta-SLaB/DSSG2017_data/graphs/prediction_graphs.jpg

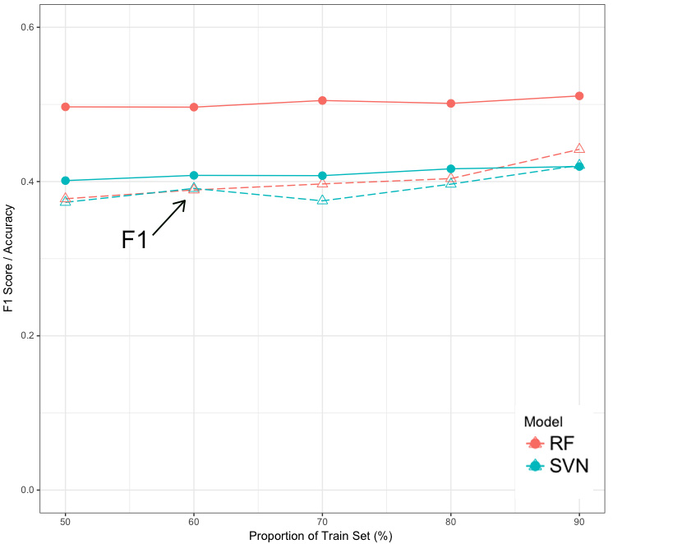
DSSG2017_data/graphs/prediction_graphs.jpg
