cledantec/Cycle-Atlanta-SLaB/DSSG2017_data/graphs/Rear_sonar.png

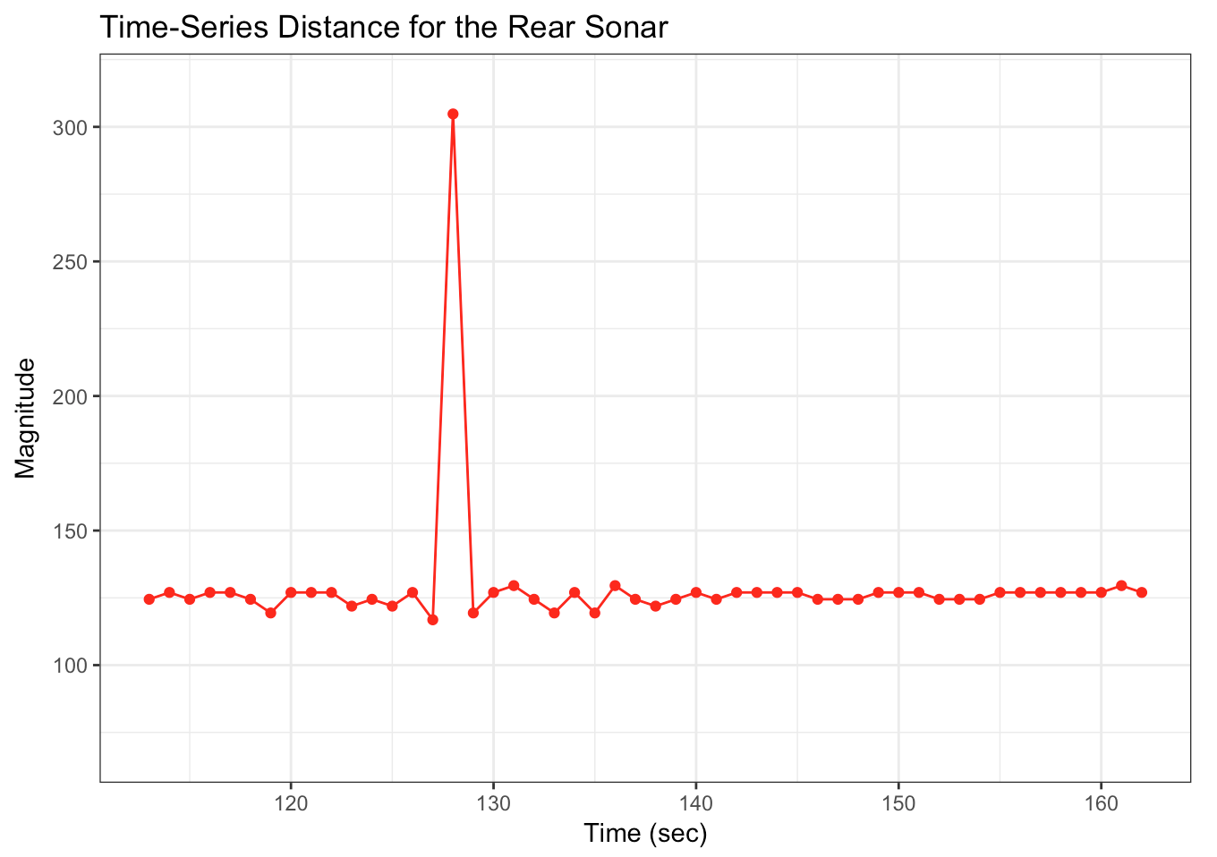
DSSG2017_data/graphs/Rear_sonar.png
