cledantec/Cycle-Atlanta-SLaB/DSSG2017_data/graphs/resampled_lidar_eg.png

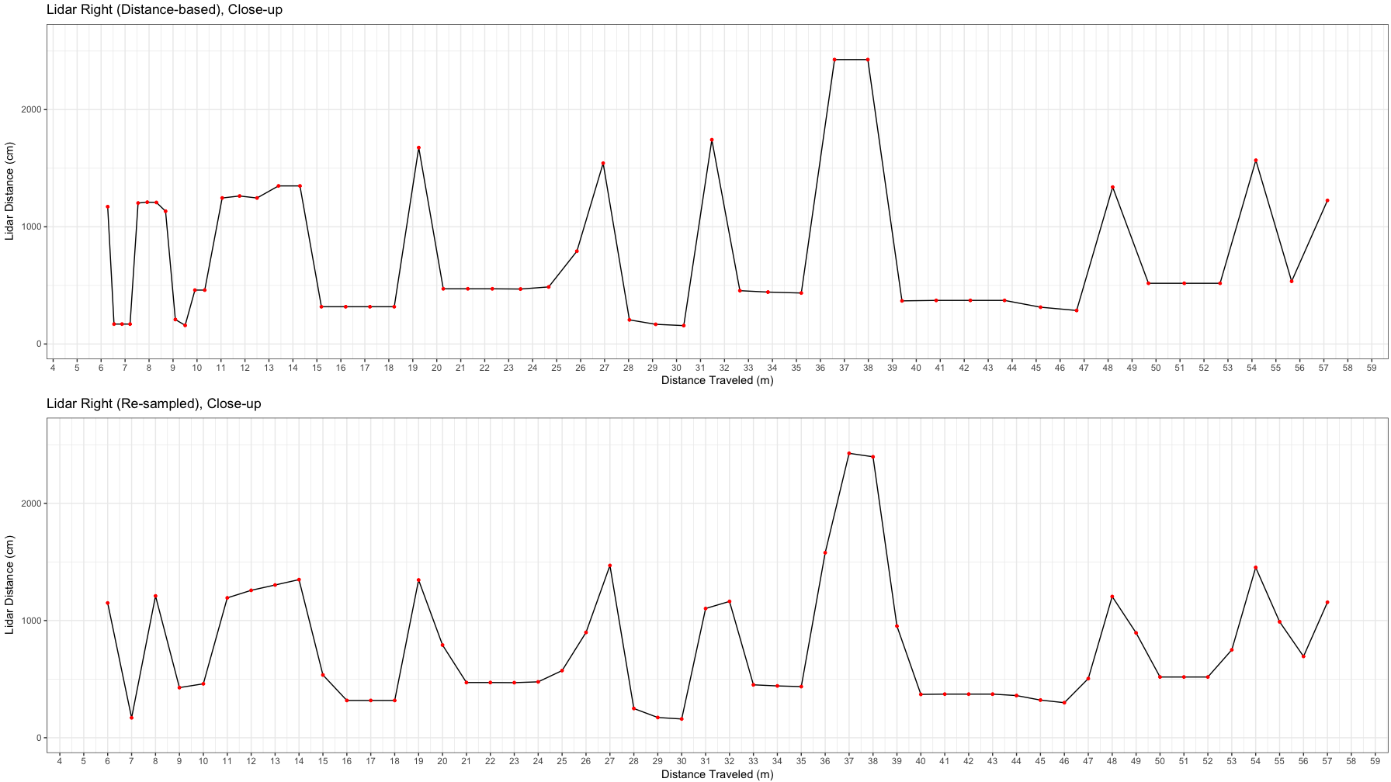
DSSG2017_data/graphs/resampled_lidar_eg.png
