cledantec/Cycle-Atlanta-SLaB/DSSG2017_data/graphs/resampled_lidar_sonar.png

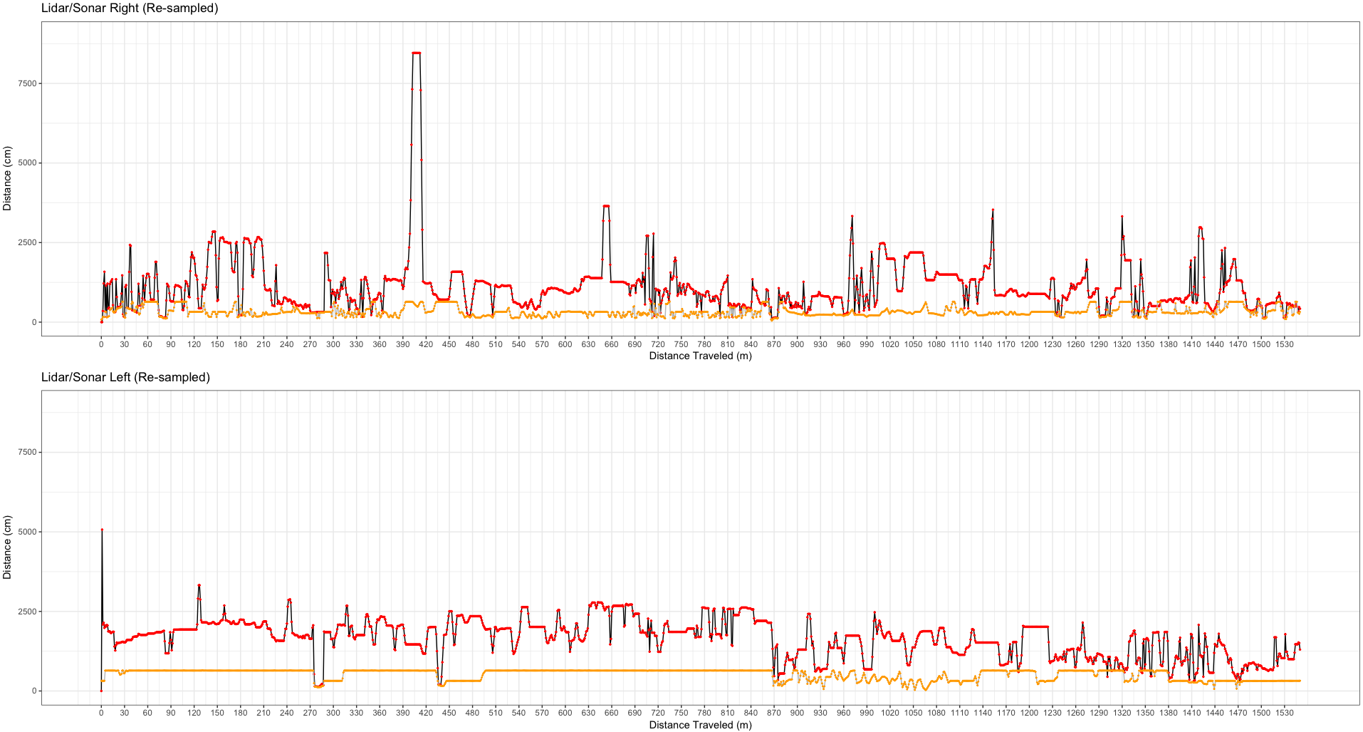
DSSG2017_data/graphs/resampled_lidar_sonar.png
