cledantec/Cycle-Atlanta-SLaB/DSSG2017_data/graphs/Right_sonar_lidar.png

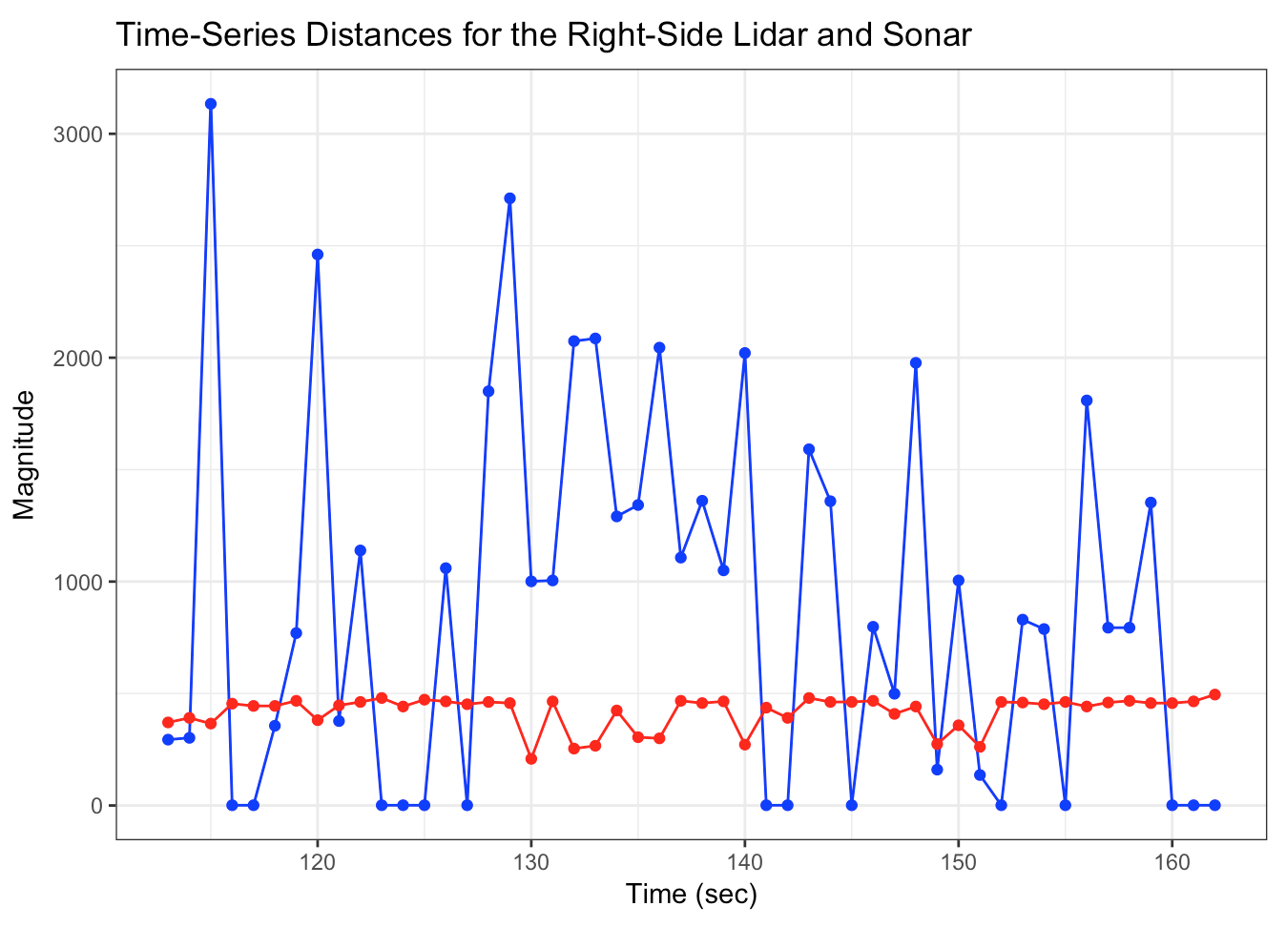
DSSG2017_data/graphs/Right_sonar_lidar.png
