cledantec/Cycle-Atlanta-SLaB/DSSG2017_data/graphs/same_routes_Javier.png

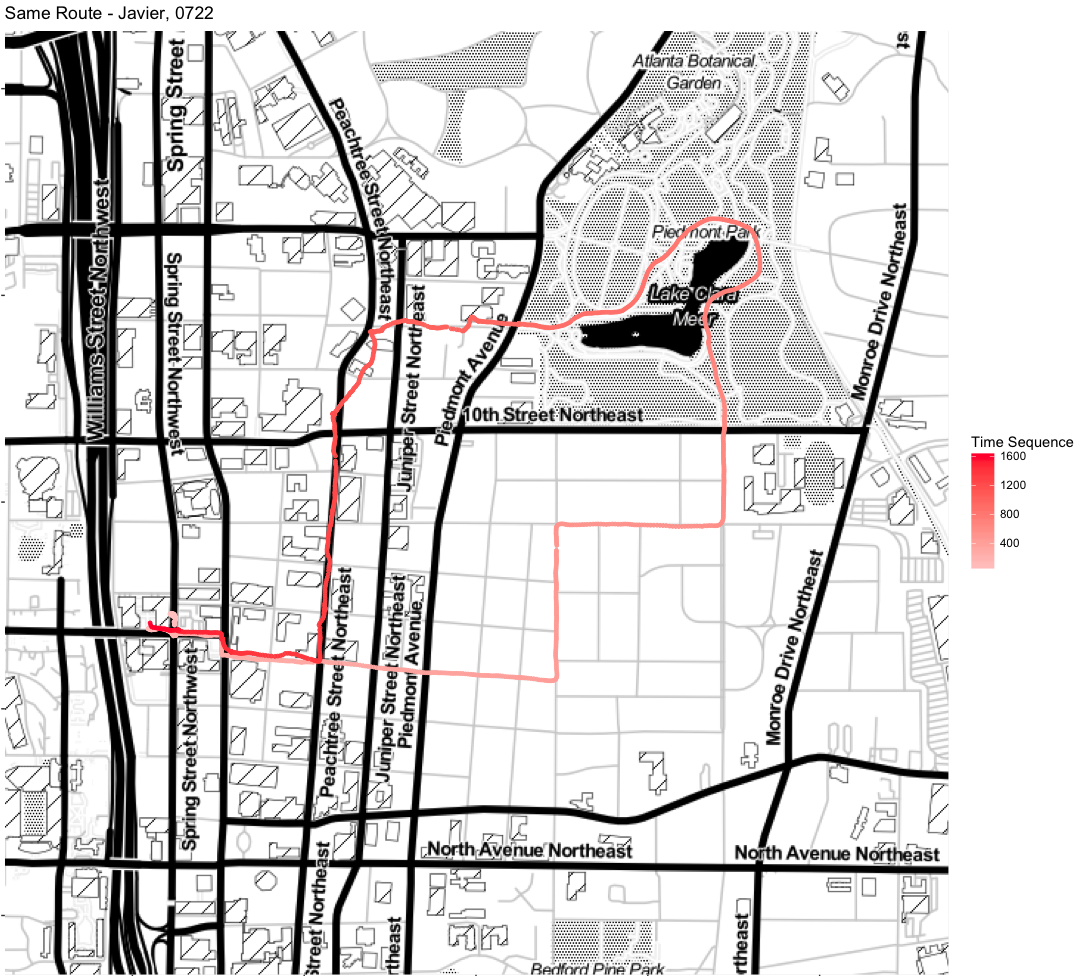
DSSG2017_data/graphs/same_routes_Javier.png
