cledantec/Cycle-Atlanta-SLaB/DSSG2017_data/graphs/street_parking_freq_sig.png

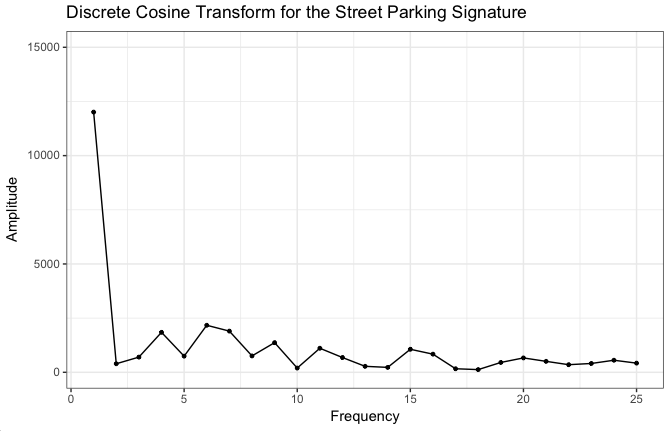
DSSG2017_data/graphs/street_parking_freq_sig.png
