cledantec/Cycle-Atlanta-SLaB/DSSG2017_data/graphs/street_parking_temporal.png

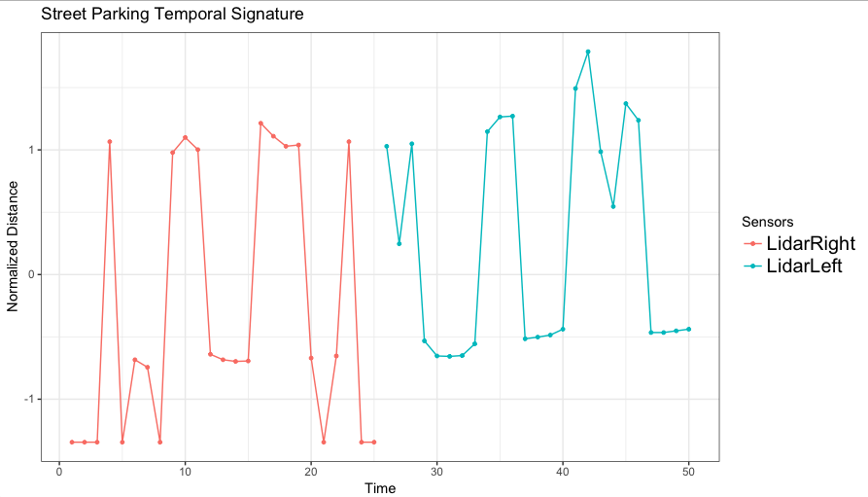
DSSG2017_data/graphs/street_parking_temporal.png
