cledantec/Cycle-Atlanta-SLaB/DSSG2017_data/graphs/volunteers.jpg

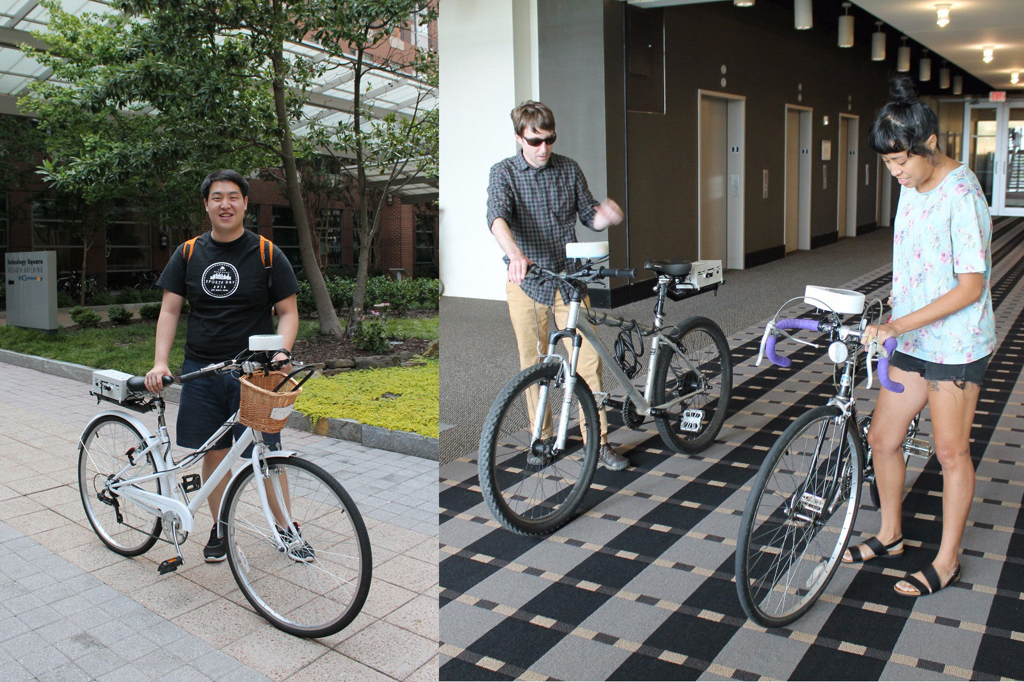
DSSG2017_data/graphs/volunteers.jpg
