cledantec/Cycle-Atlanta-SLaB/DSSG2017_data/sample_data/Myeong/CourseMyeong230717.png

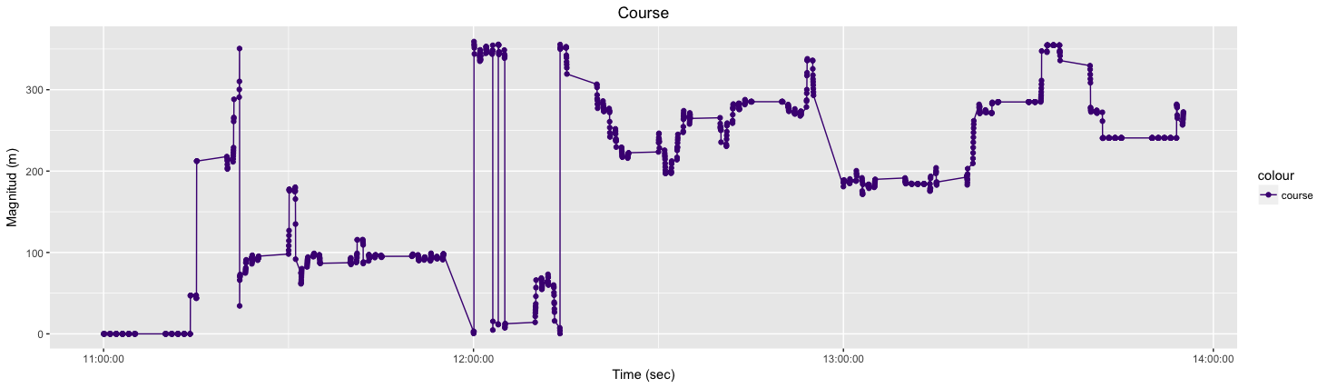
DSSG2017_data/sample_data/Myeong/CourseMyeong230717.png
