cledantec/Cycle-Atlanta-SLaB/DSSG2017_data/sample_data/Myeong/Myeong_Route230717.png

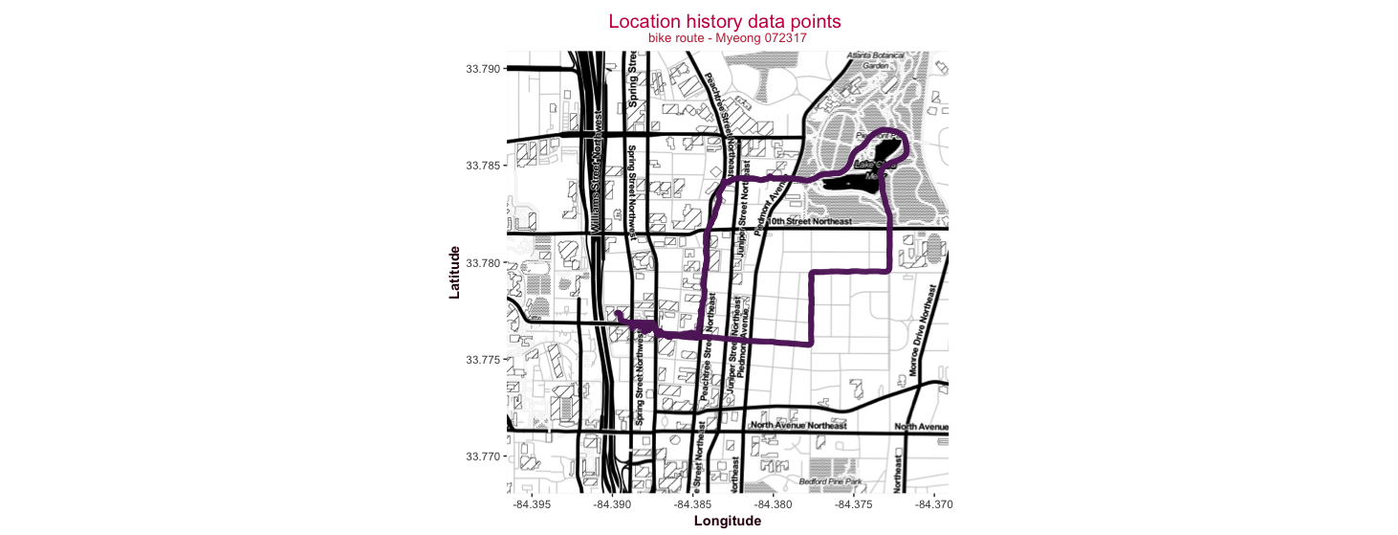
DSSG2017_data/sample_data/Myeong/Myeong_Route230717.png
