cledantec/Cycle-Atlanta-SLaB/DSSG2017_data/sample_data/Myeong/Speed(realTime).png

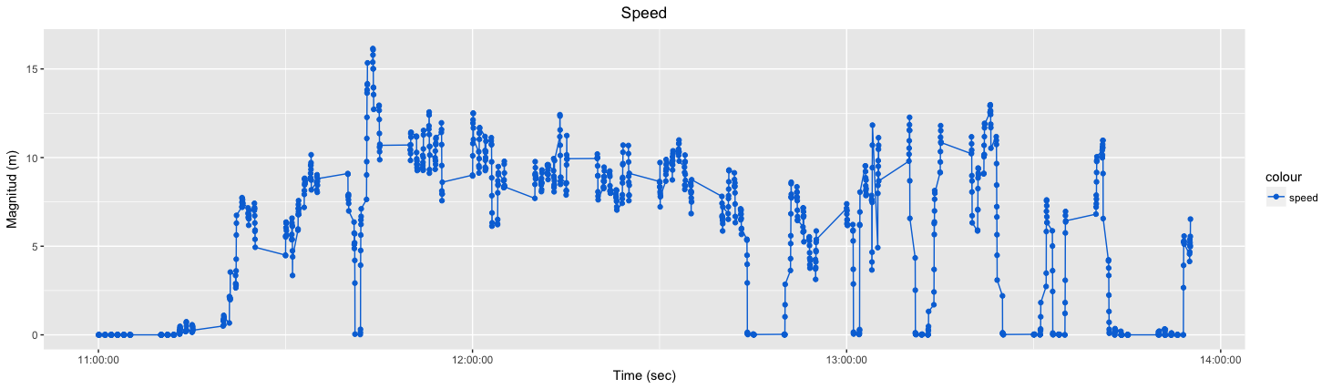
DSSG2017_data/sample_data/Myeong/Speed(realTime).png
