cledantec/Cycle-Atlanta-SLaB/images/gas_colocation.jpg

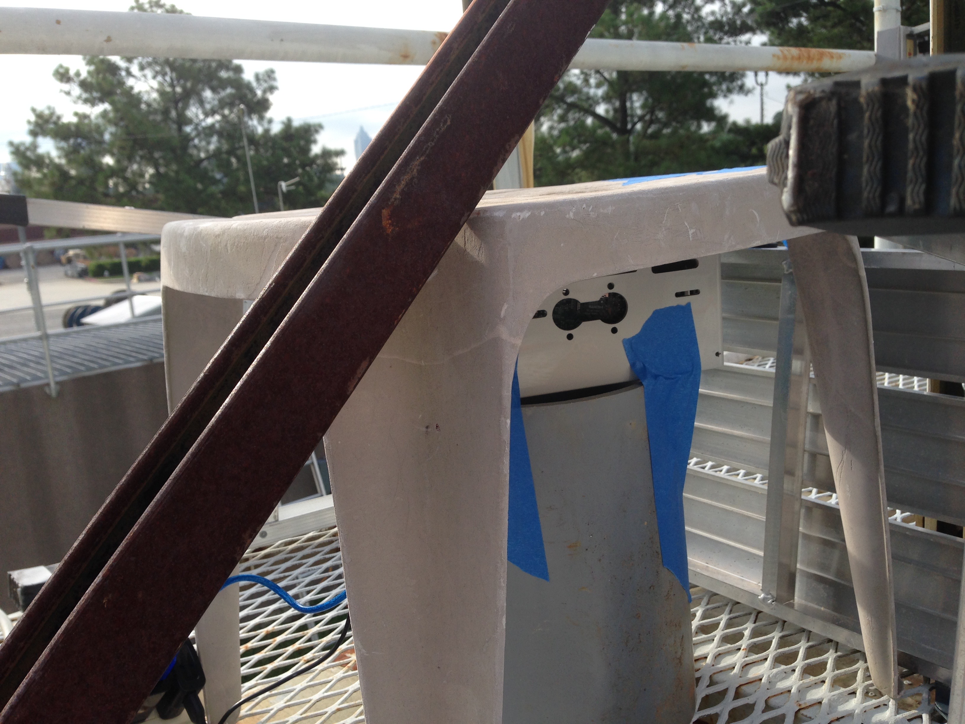
images/gas_colocation.jpg
