cledantec/Cycle-Atlanta-SLaB/images/gas_station.jpg

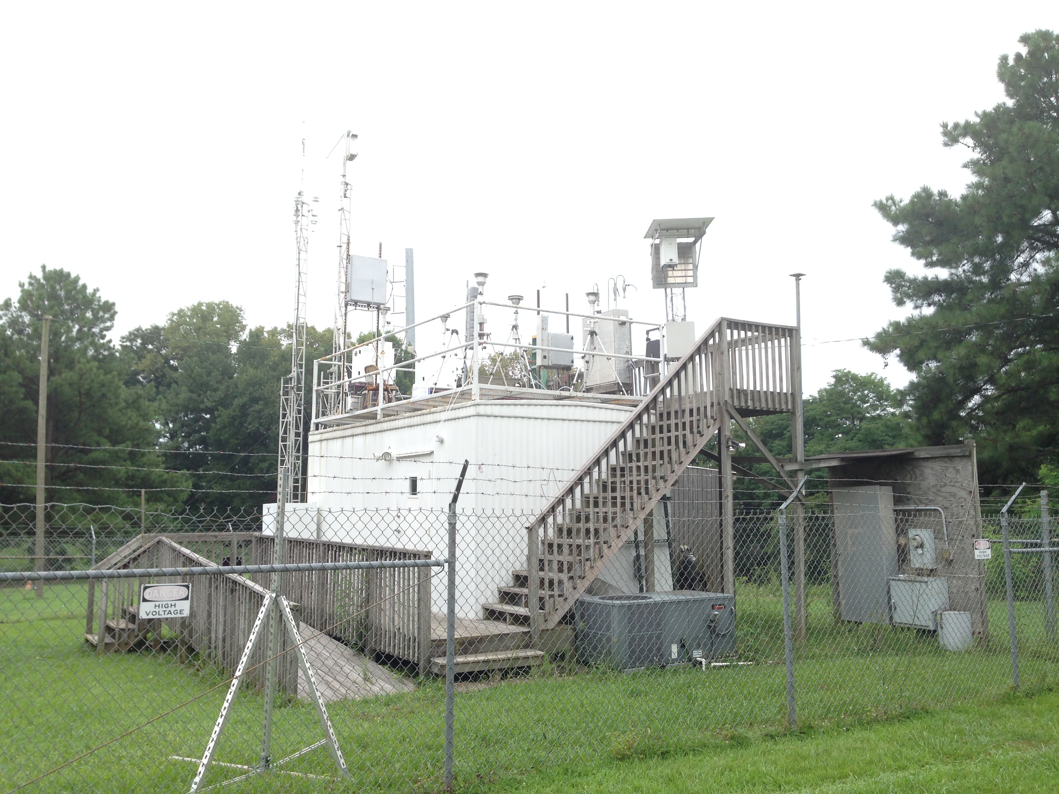
images/gas_station.jpg
