cledantec/Cycle-Atlanta-SLaB/images/GPS.png

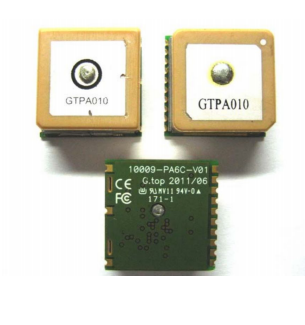
images/GPS.png
