cledantec/Cycle-Atlanta-SLaB/images/Image uploaded from iOS.jpg

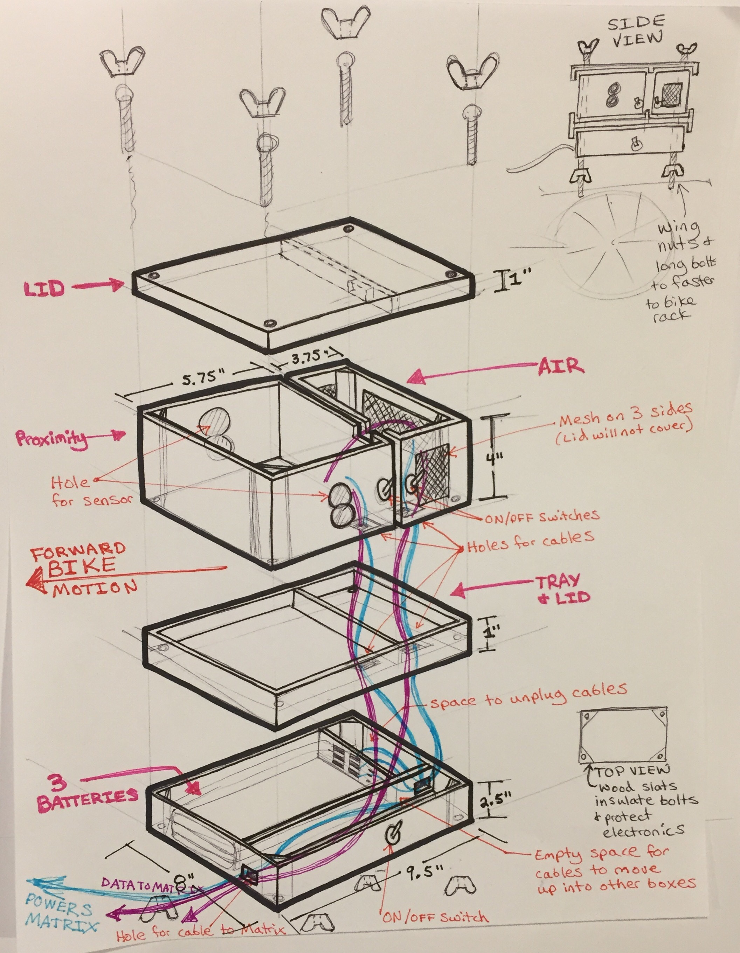
images/Image uploaded from iOS.jpg
