cledantec/Cycle-Atlanta-SLaB/images/IMG_20170118_132140.jpg

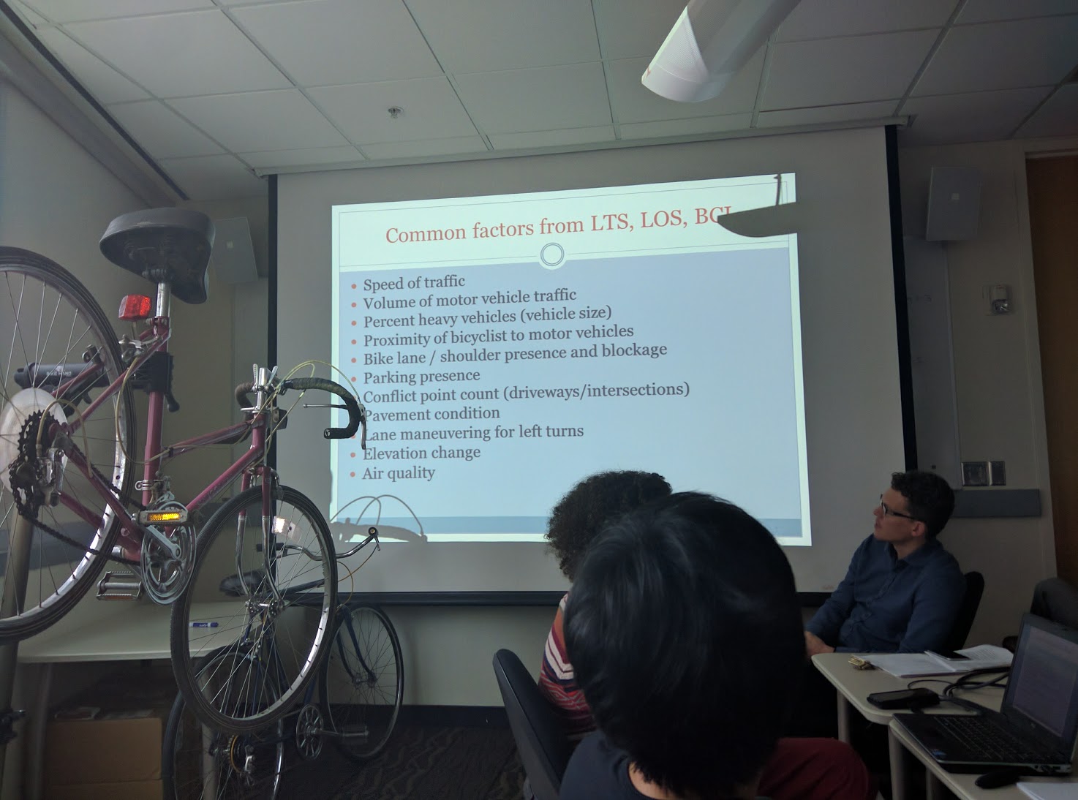
images/IMG_20170118_132140.jpg
