cledantec/Cycle-Atlanta-SLaB/images/IMG_20170214_121551.jpg

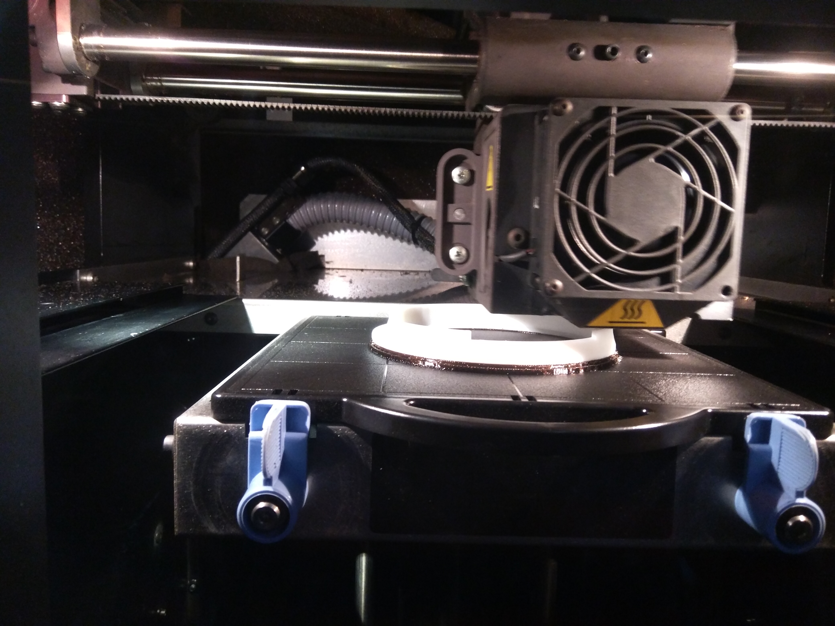
images/IMG_20170214_121551.jpg
