cledantec/Cycle-Atlanta-SLaB/images/IMG_20170315_131853.jpg

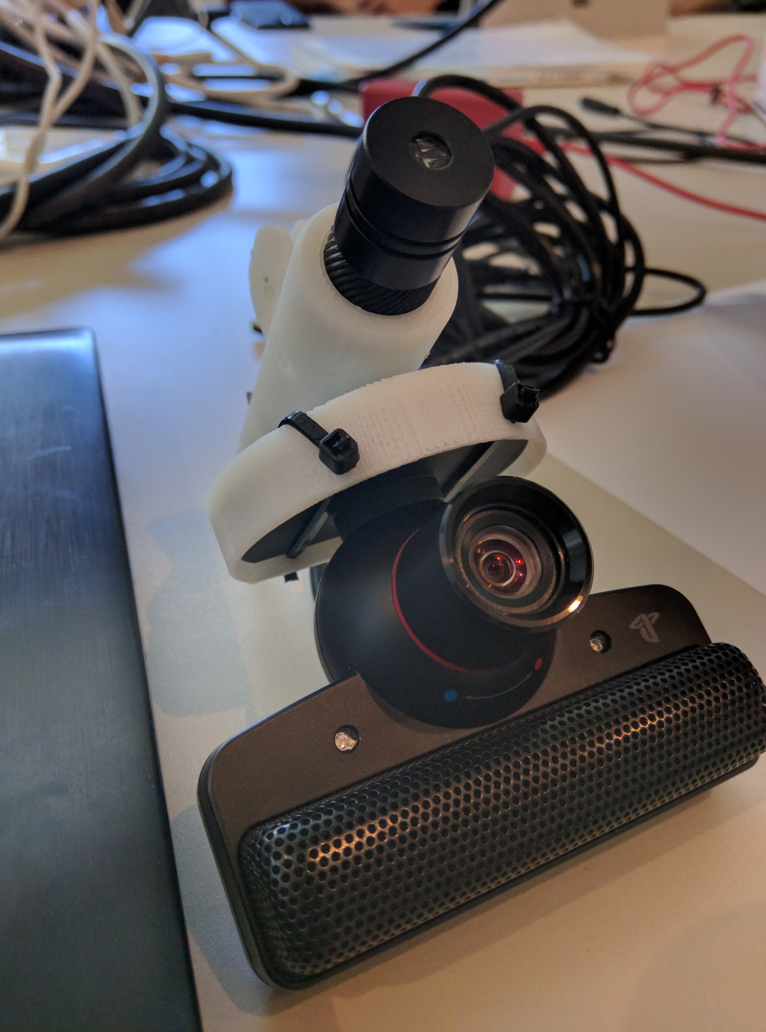
images/IMG_20170315_131853.jpg
