cledantec/Cycle-Atlanta-SLaB/images/IMG_20170424_104118.jpg

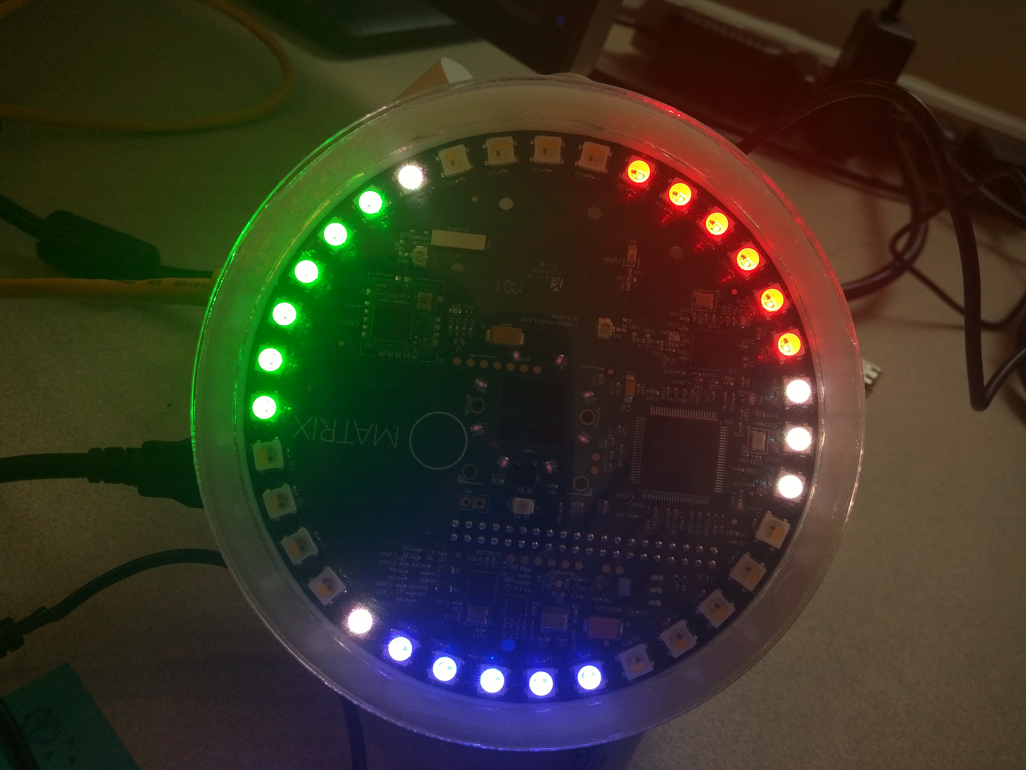
images/IMG_20170424_104118.jpg
