cledantec/Cycle-Atlanta-SLaB/SLAB-wjmy/Engineering Documents /CAD Prototype/800px-Bicycle-Silhouette.svg.png

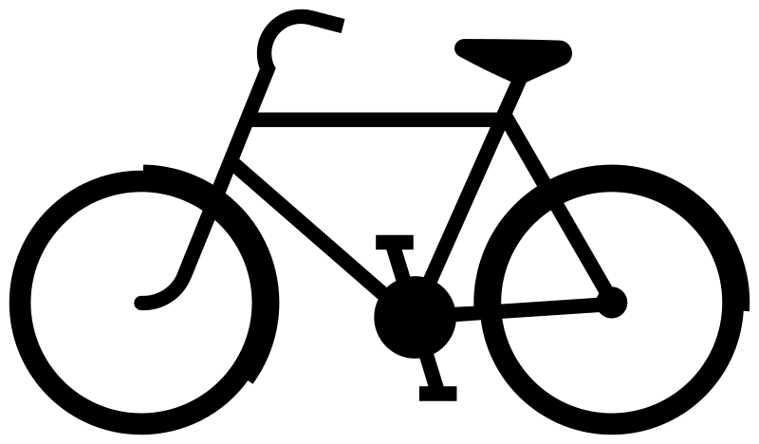
SLAB-wjmy/Engineering Documents /CAD Prototype/800px-Bicycle-Silhouette.svg.png
