cledantec/Cycle-Atlanta-SLaB/SLAB-wjmy/Engineering Documents /CAD Prototype/bike phone mount/20170722_131039.jpg

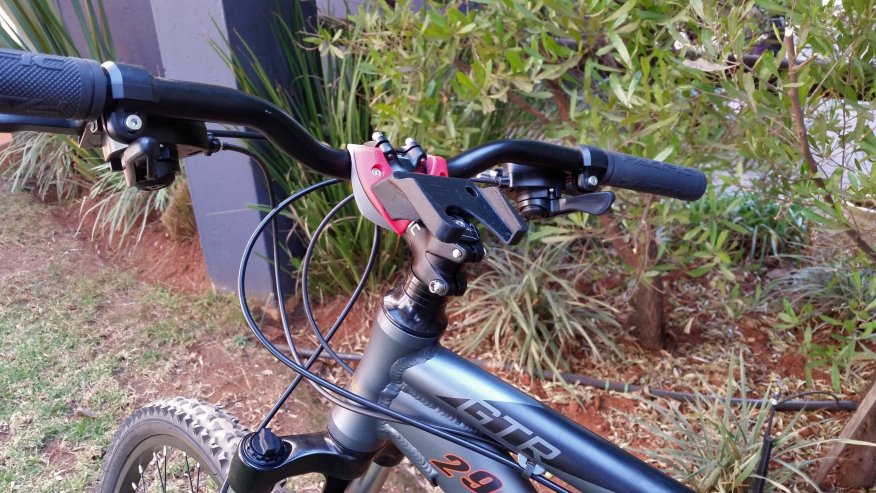
SLAB-wjmy/Engineering Documents /CAD Prototype/bike phone mount/20170722_131039.jpg
