cledantec/Cycle-Atlanta-SLaB/SLAB-wjmy/Engineering Documents /CAD Prototype/bike phone mount/20170722_131106.jpg

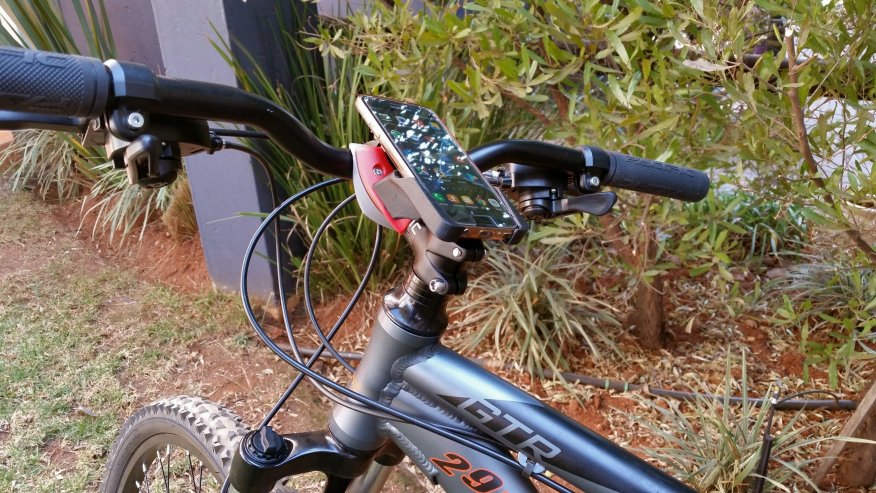
SLAB-wjmy/Engineering Documents /CAD Prototype/bike phone mount/20170722_131106.jpg
