cledantec/Cycle-Atlanta-SLaB/SLAB-wjmy/Engineering Documents /CAD Prototype/bike phone mount/Smartphone Holder For Mountain Bike (Galaxy S7).png

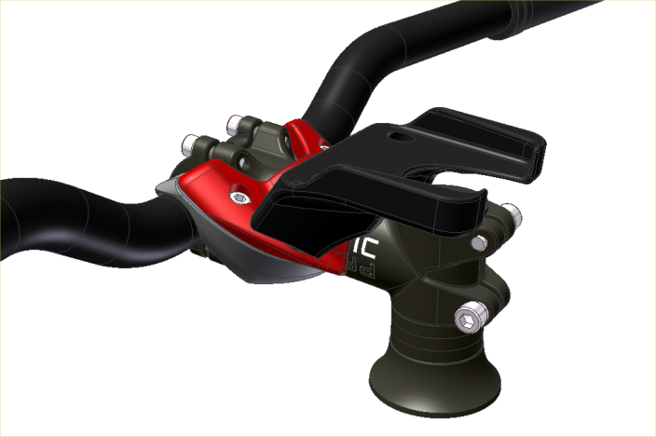
SLAB-wjmy/Engineering Documents /CAD Prototype/bike phone mount/Smartphone Holder For Mountain Bike (Galaxy S7).png
