cledantec/Cycle-Atlanta-SLaB/SLAB-wjmy/Engineering Documents /CAD Prototype/Bike_project/_2.JPG

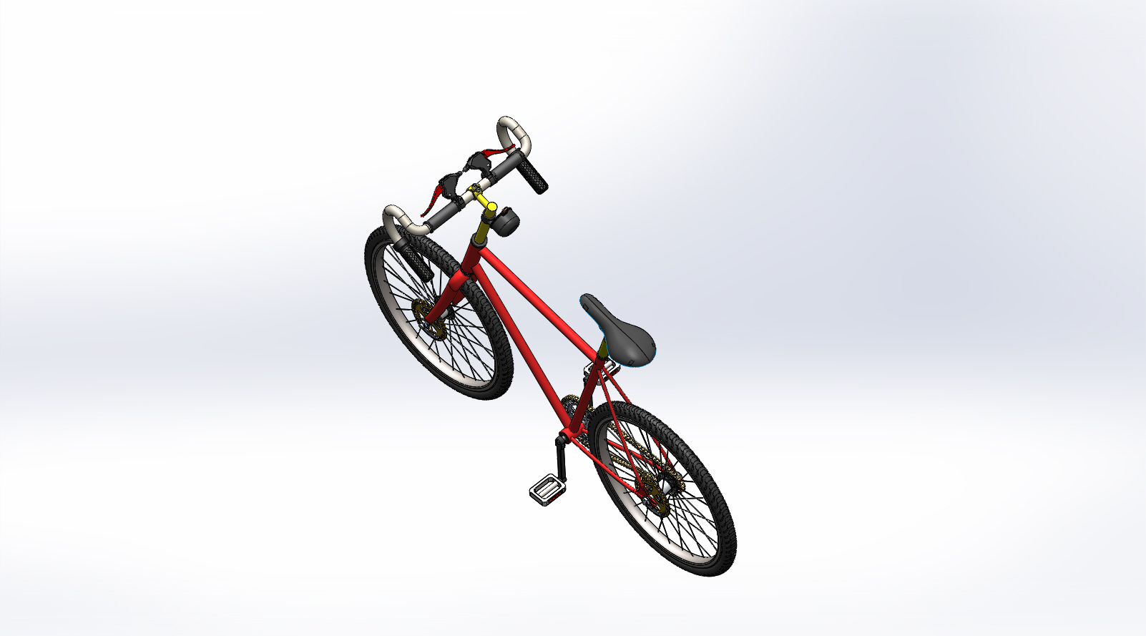
SLAB-wjmy/Engineering Documents /CAD Prototype/Bike_project/_2.JPG
