cledantec/Cycle-Atlanta-SLaB/SLAB-wjmy/Engineering Documents /CAD Prototype/Bike_project/final_bike8.JPG

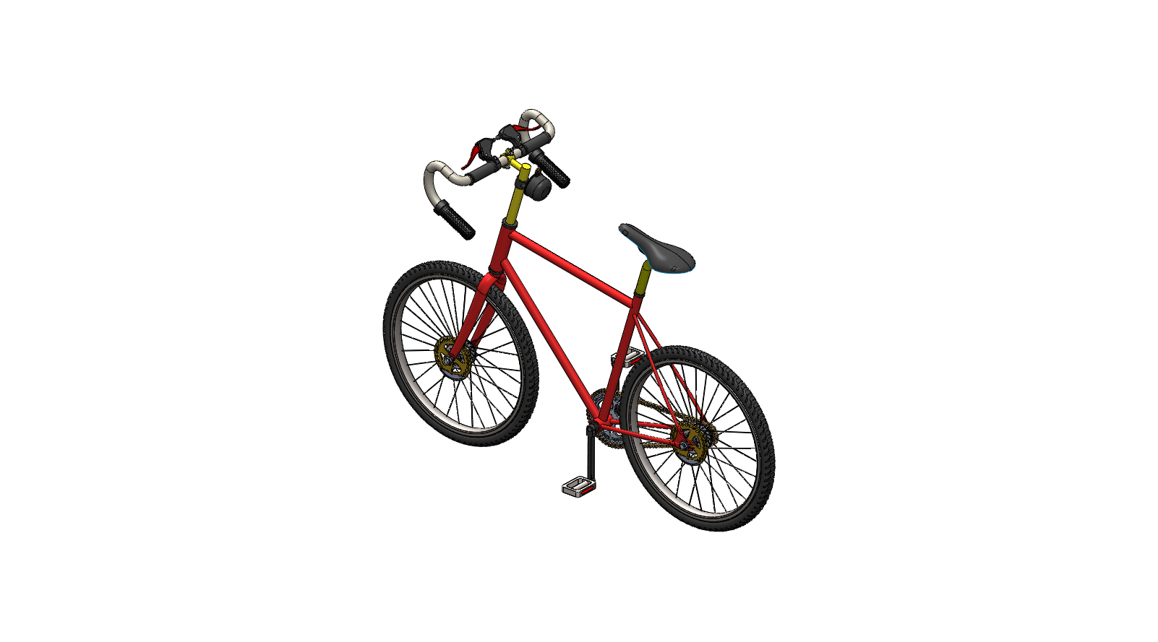
SLAB-wjmy/Engineering Documents /CAD Prototype/Bike_project/final_bike8.JPG
