cledantec/Cycle-Atlanta-SLaB/SLAB-wjmy/Engineering Documents /CAD Prototype/Final Renderings/Box on Bike - Zoomed.JPG

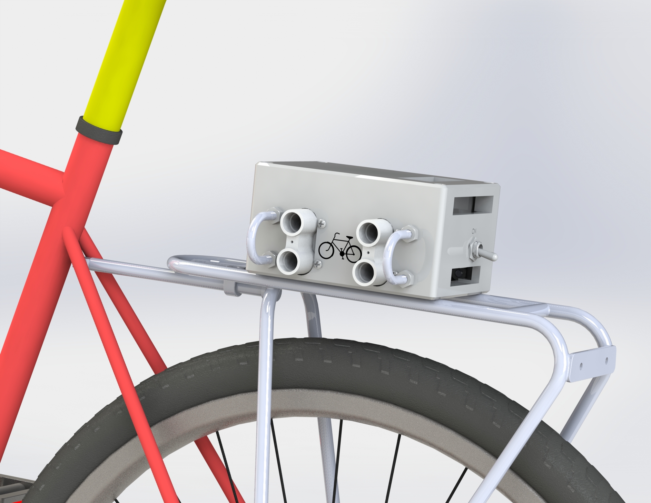
SLAB-wjmy/Engineering Documents /CAD Prototype/Final Renderings/Box on Bike - Zoomed.JPG
