cledantec/Cycle-Atlanta-SLaB/SLAB-wjmy/Engineering Documents /CAD Prototype/Final Renderings/Internal View.JPG

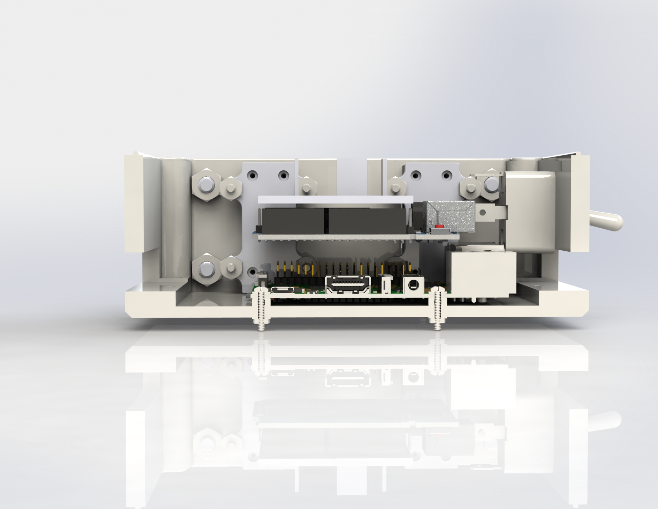
SLAB-wjmy/Engineering Documents /CAD Prototype/Final Renderings/Internal View.JPG
