cledantec/Cycle-Atlanta-SLaB/SLAB-wjmy/Engineering Documents /CAD Prototype/Final Renderings/Sexy Box 2 - Electric Boogaloo.JPG

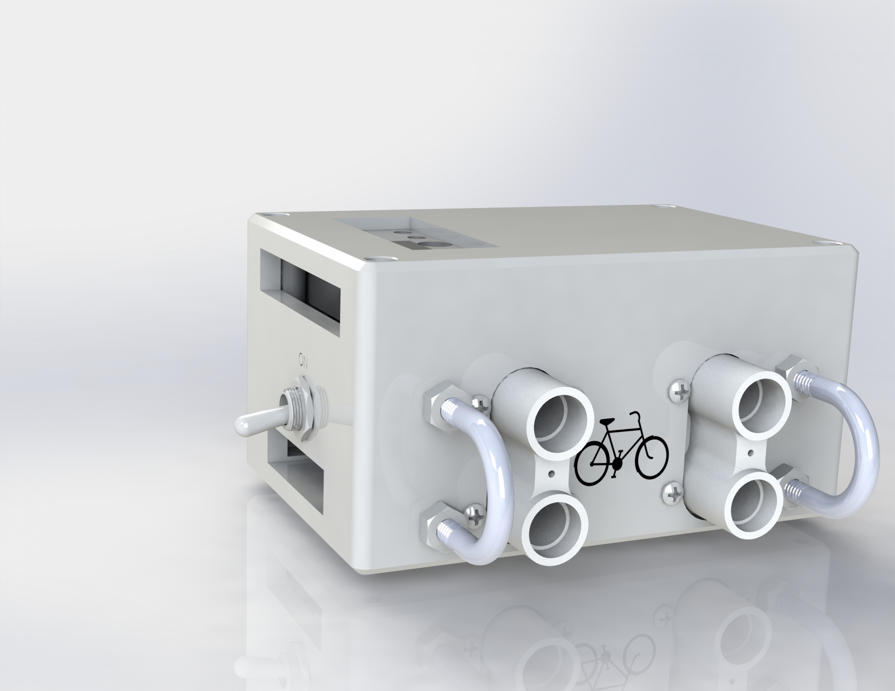
SLAB-wjmy/Engineering Documents /CAD Prototype/Final Renderings/Sexy Box 2 - Electric Boogaloo.JPG
