cledantec/Cycle-Atlanta-SLaB/SLAB-wjmy/Engineering Documents /CAD Prototype/Final Renderings/Sexy Box - No Lid.JPG

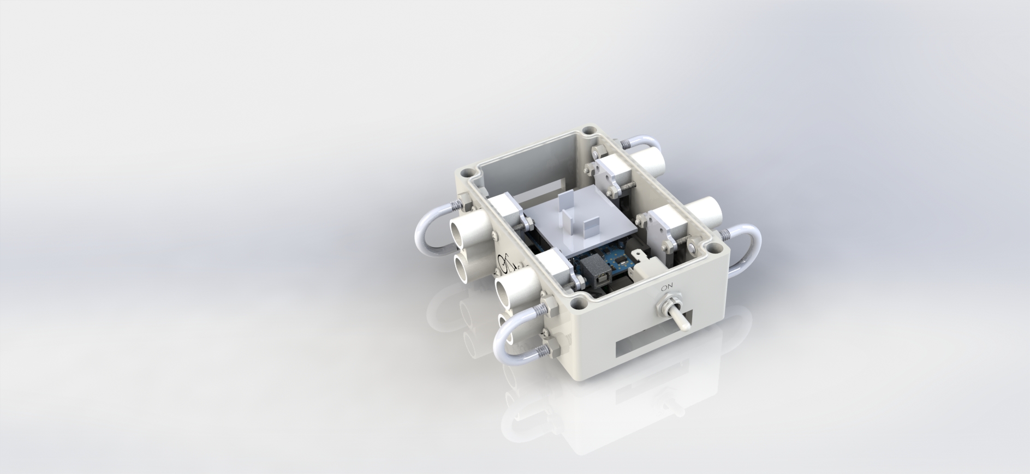
SLAB-wjmy/Engineering Documents /CAD Prototype/Final Renderings/Sexy Box - No Lid.JPG
