cledantec/Cycle-Atlanta-SLaB/SLAB-wjmy/Engineering Documents /CAD Prototype/Final Renderings/Sexy Box.JPG

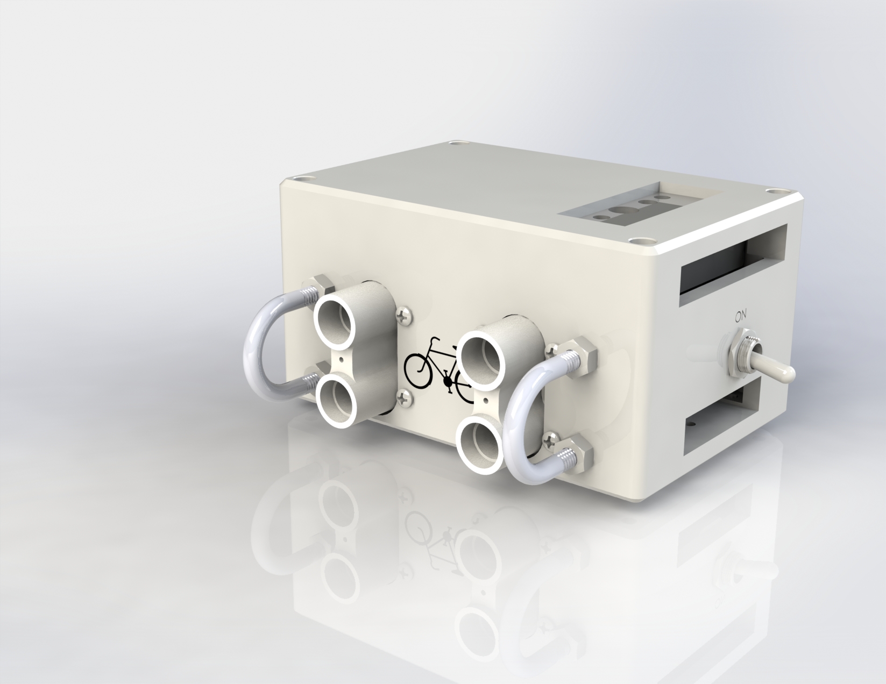
SLAB-wjmy/Engineering Documents /CAD Prototype/Final Renderings/Sexy Box.JPG
