cledantec/Cycle-Atlanta-SLaB/SLAB-wjmy/Engineering Documents /CAD Prototype/iphone-x-34.snapshot.3/iphonex.jpg

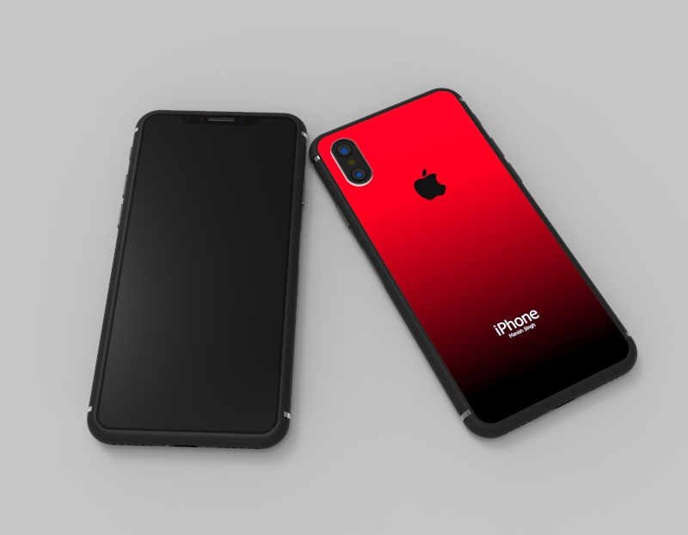
SLAB-wjmy/Engineering Documents /CAD Prototype/iphone-x-34.snapshot.3/iphonex.jpg
