cledantec/Cycle-Atlanta-SLaB/SLAB-wjmy/Engineering Documents /CAD Prototype/Package Prototype 1/FULL SIZE Version/Render2 - Package on Bike Pannier.JPG

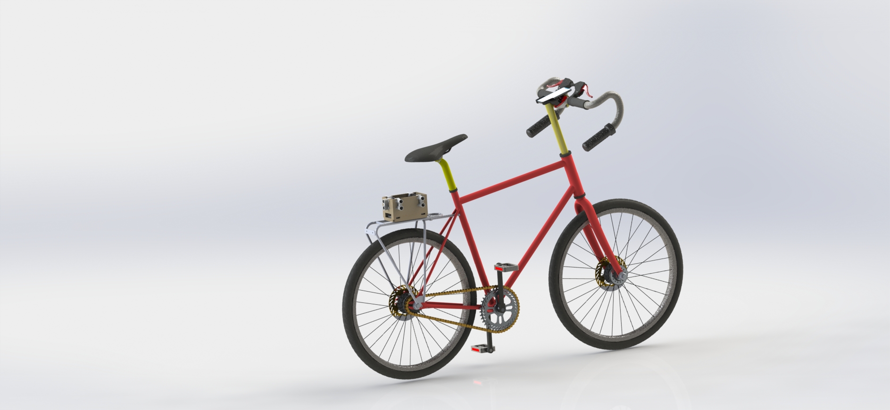
SLAB-wjmy/Engineering Documents /CAD Prototype/Package Prototype 1/FULL SIZE Version/Render2 - Package on Bike Pannier.JPG
