cledantec/Cycle-Atlanta-SLaB/SLAB-wjmy/Engineering Documents /CAD Prototype/Package Prototype 1/FULL SIZE Version/Render3 - Package.JPG

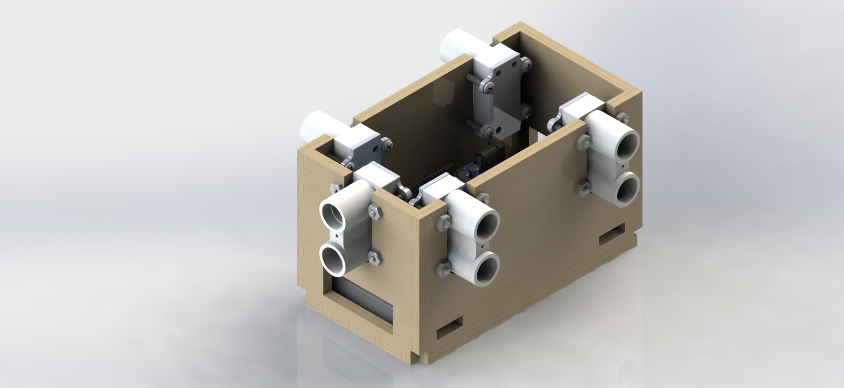
SLAB-wjmy/Engineering Documents /CAD Prototype/Package Prototype 1/FULL SIZE Version/Render3 - Package.JPG
