cledantec/Cycle-Atlanta-SLaB/SLAB-wjmy/Engineering Documents /CAD Prototype/Package Prototype 1/FULL SIZE Version/Render4 - Cut View.JPG

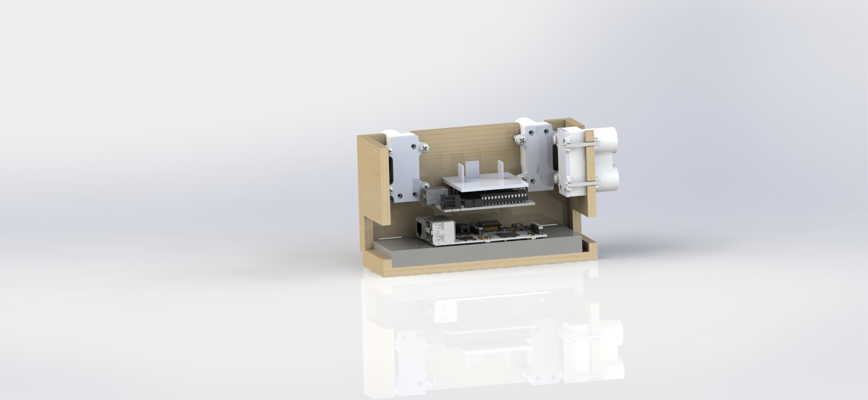
SLAB-wjmy/Engineering Documents /CAD Prototype/Package Prototype 1/FULL SIZE Version/Render4 - Cut View.JPG
