cledantec/Cycle-Atlanta-SLaB/SLAB-wjmy/Engineering Documents /CAD Prototype/arduino-uno-r3-1/arduino uno/dip28.SLDASM

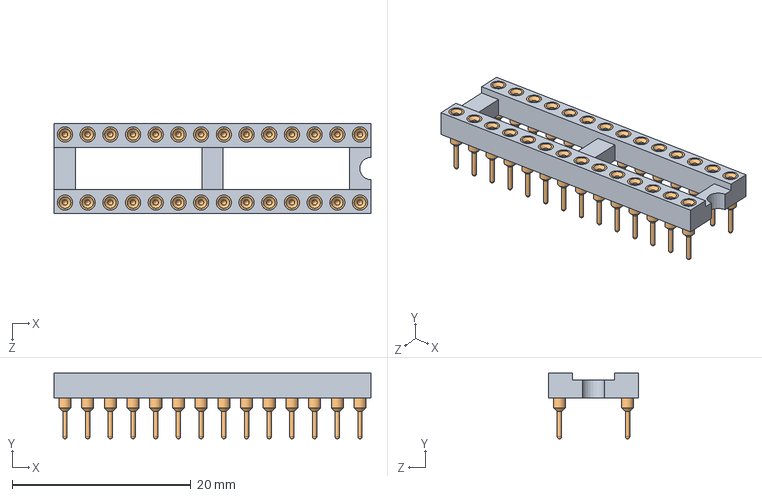
[picture p139: CAD file, 2020-04-30]
SLAB-wjmy/Engineering Documents /CAD Prototype/arduino-uno-r3-1/arduino uno/dip28.SLDASM
35.5 x 7.37 x 10.1 mm
dip28
dip socket pin x 28
