cledantec/Cycle-Atlanta-SLaB/SLAB-wjmy/Engineering Documents /CAD Prototype/arduino-uno-r3-1/arduino uno/USB type b.SLDPRT.SLDASM

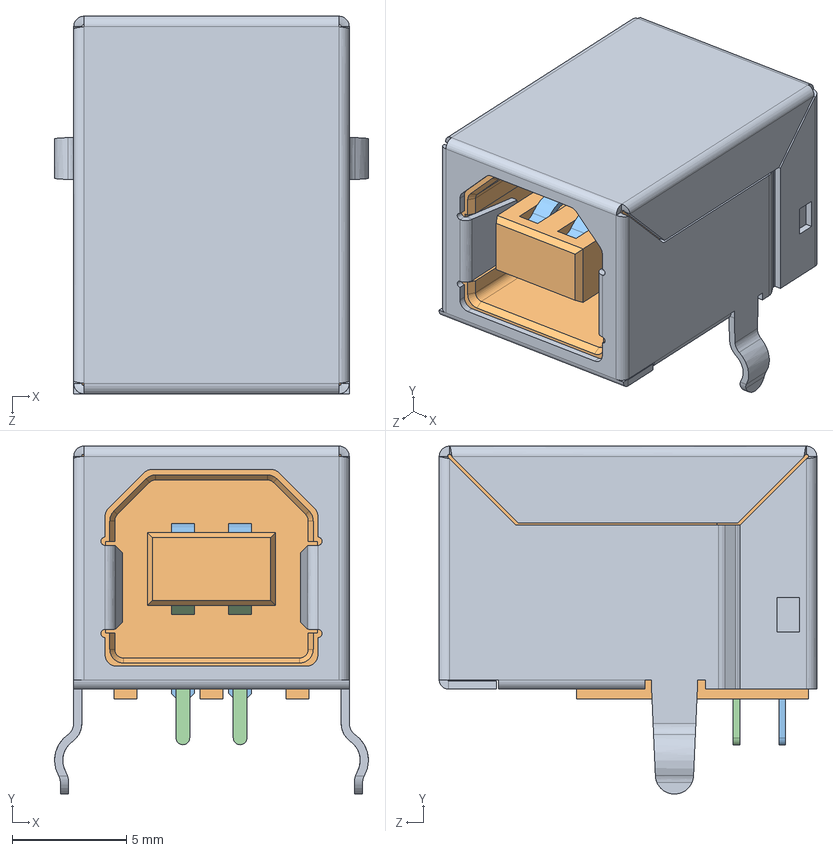
[picture p140: CAD file, 2020-04-30]
SLAB-wjmy/Engineering Documents /CAD Prototype/arduino-uno-r3-1/arduino uno/USB type b.SLDPRT.SLDASM
13.7 x 15.2 x 16.5 mm
USB SHELL
USB core
usb top contact x 2
usb btm contact x 2
