cledantec/Cycle-Atlanta-SLaB/SLAB-wjmy/Engineering Documents /CAD Prototype/arduino-uno-r3-1/arduino uno/arduino uno.SLDASM

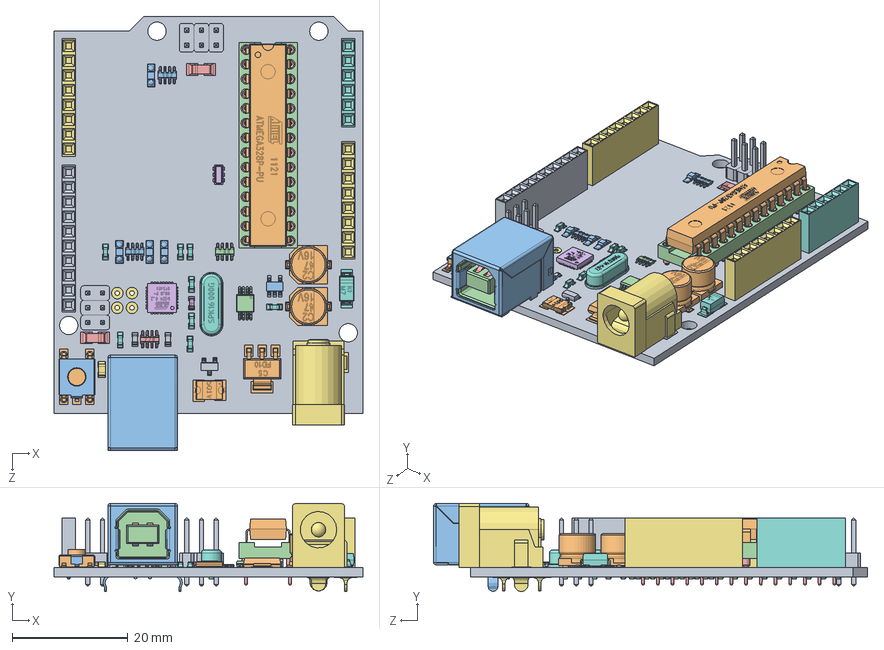
[picture p141: CAD file, 2020-04-30]
SLAB-wjmy/Engineering Documents /CAD Prototype/arduino-uno-r3-1/arduino uno/arduino uno.SLDASM
53.3 x 15.2 x 74.9 mm
unoboard blue
47uf CAP Dcase x 2
USB SHELL
USB core
usb top contact x 2
usb btm contact x 2
power jack
crystal
2pin_header__02 x 6
nano - reg
led x 4
dip28
dip socket pin x 28
atmega16u2
8 PORT HEADER x 2
6 PORT HEADER
10 PORT HEADER
ATMEL328P
102 RESISTOR PACK x 2
103 RESISTOR PACK
220 RESISTOR PACK
16mhz crystal - measured
PADS001
603 cap on pad x 8
ssot3
mf-msmf050-2
lmv358
lp2985dgkr
cd1206 diode x 2
603 resistor
blm21
m7 diode
MLC0603 x 2
RESET CORE
RESET
