cledantec/Cycle-Atlanta-SLaB/DSSG2017_Case_Design/Back box/print ABS box/misc/Box.SLDPRT

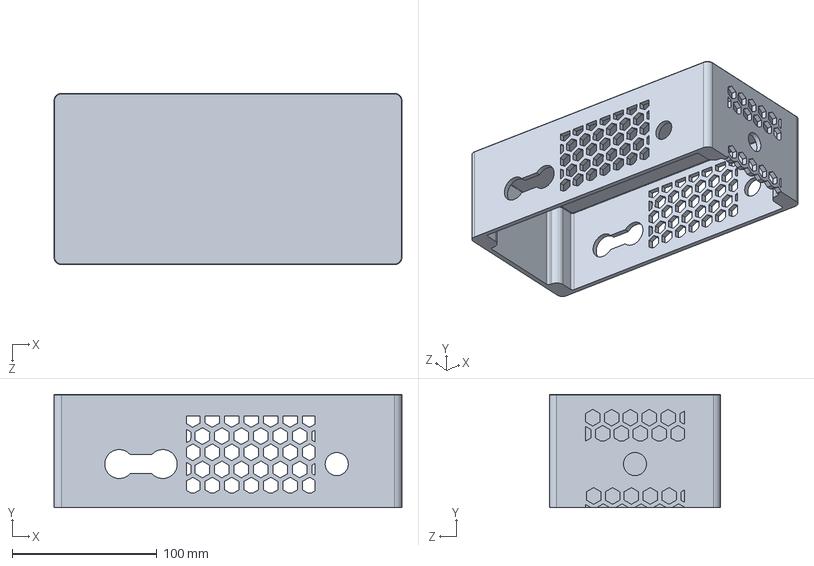
[picture p142: CAD file, 2017-07-28]
DSSG2017_Case_Design/Back box/print ABS box/misc/Box.SLDPRT
240.0 x 78.0 x 118.0 mm
