cledantec/Cycle-Atlanta-SLaB/DSSG2017_Case_Design/Front box/MatrixCaseBottom.SLDPRT

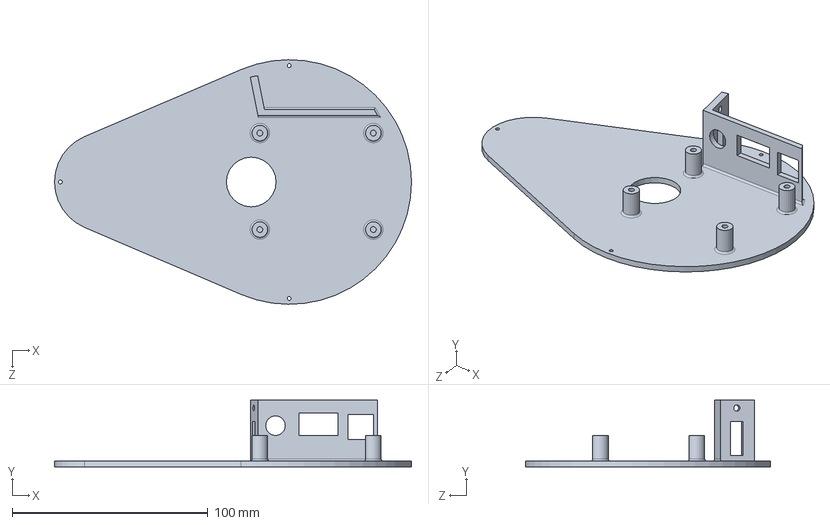
[picture p143: CAD file, 2017-07-28]
DSSG2017_Case_Design/Front box/MatrixCaseBottom.SLDPRT
182.4 x 34.0 x 125.0 mm
