cledantec/Cycle-Atlanta-SLaB/SLAB-wjmy/Engineering Documents /CAD Prototype/arduino-uno-r3-1/arduino uno/ssot3.SLDPRT

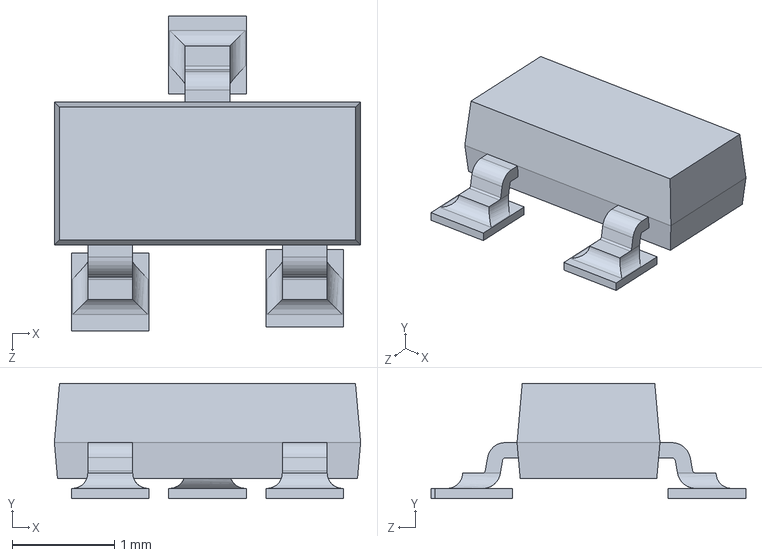
[picture p144: CAD file, 2020-04-30]
SLAB-wjmy/Engineering Documents /CAD Prototype/arduino-uno-r3-1/arduino uno/ssot3.SLDPRT
3.00 x 1.13 x 3.09 mm
