cledantec/Cycle-Atlanta-SLaB/SLAB-wjmy/Engineering Documents /CAD Prototype/bicycle-pannier-rack-1.snapshot.2/Pannier Rack.STEP

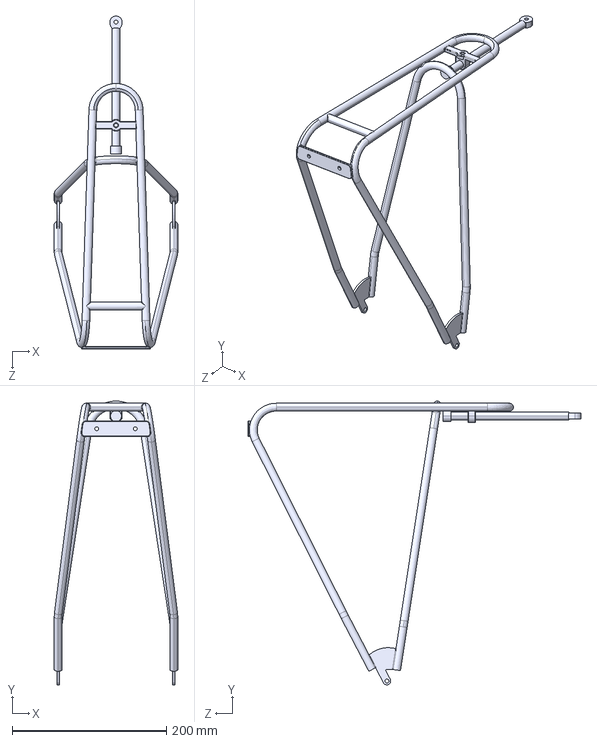
[picture p145: CAD file, 2020-04-30]
SLAB-wjmy/Engineering Documents /CAD Prototype/bicycle-pannier-rack-1.snapshot.2/Pannier Rack.STEP
160.2 x 367.9 x 431.6 mm
