cledantec/Cycle-Atlanta-SLaB/SLAB-wjmy/Engineering Documents /CAD Prototype/Bike_project/bell/base.SLDPRT

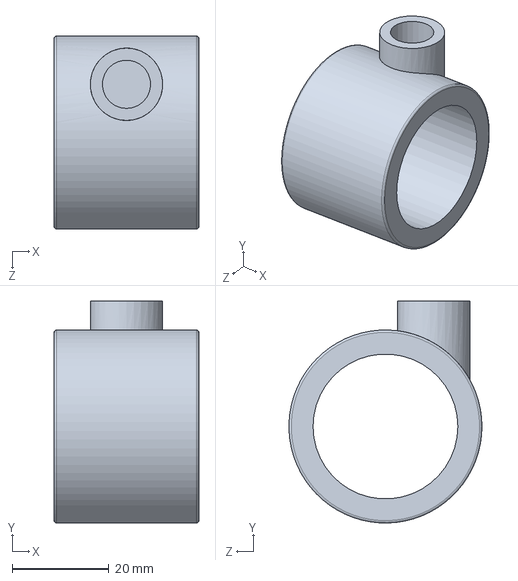
[picture p146: CAD file, 2020-04-30]
SLAB-wjmy/Engineering Documents /CAD Prototype/Bike_project/bell/base.SLDPRT
30.0 x 46.0 x 40.0 mm
