cledantec/Cycle-Atlanta-SLaB/SLAB-wjmy/Engineering Documents /CAD Prototype/Bike_project/Break/Break1.SLDPRT

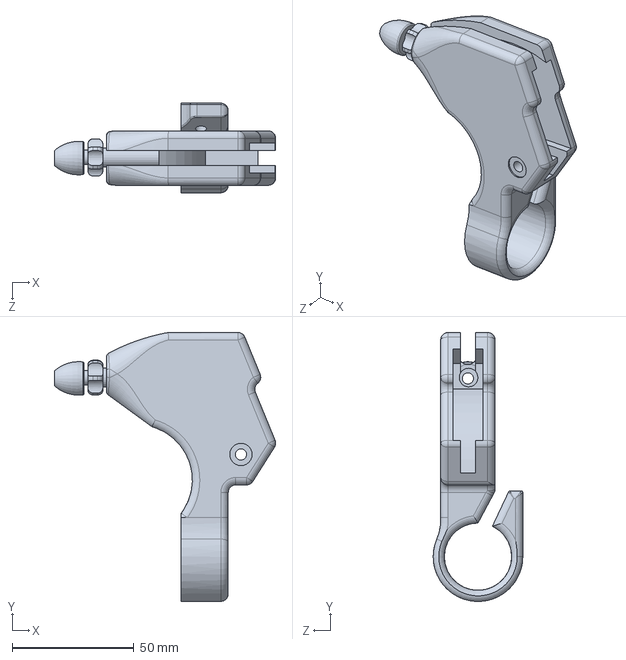
[picture p147: CAD file, 2020-04-30]
SLAB-wjmy/Engineering Documents /CAD Prototype/Bike_project/Break/Break1.SLDPRT
91.1 x 110.6 x 36.9 mm
