cledantec/Cycle-Atlanta-SLaB/SLAB-wjmy/Engineering Documents /CAD Prototype/Bike_project/chain/outer_chain.SLDPRT

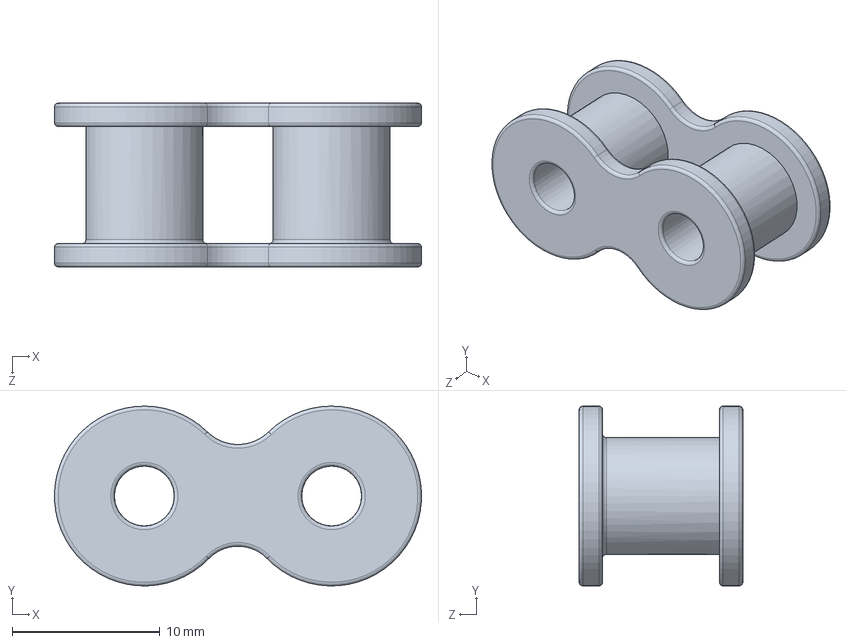
[picture p148: CAD file, 2020-04-30]
SLAB-wjmy/Engineering Documents /CAD Prototype/Bike_project/chain/outer_chain.SLDPRT
24.9 x 12.2 x 11.1 mm
