cledantec/Cycle-Atlanta-SLaB/SLAB-wjmy/Engineering Documents /CAD Prototype/Bike_project/Pedal_final/cover.SLDPRT

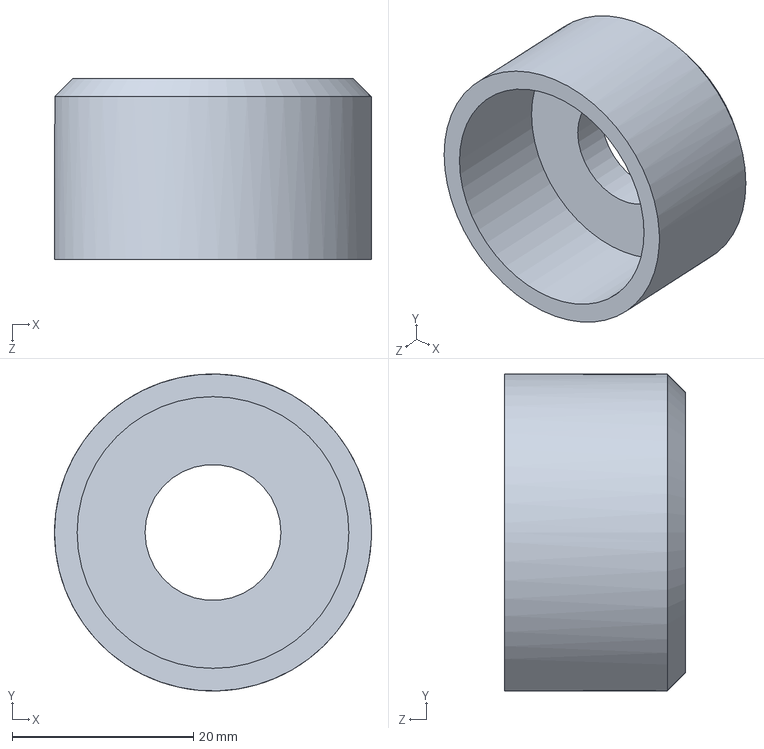
[picture p149: CAD file, 2020-04-30]
SLAB-wjmy/Engineering Documents /CAD Prototype/Bike_project/Pedal_final/cover.SLDPRT
35.0 x 35.0 x 20.0 mm
