cledantec/Cycle-Atlanta-SLaB/SLAB-wjmy/Engineering Documents /CAD Prototype/Bike_project/Project/fork_hub.SLDPRT

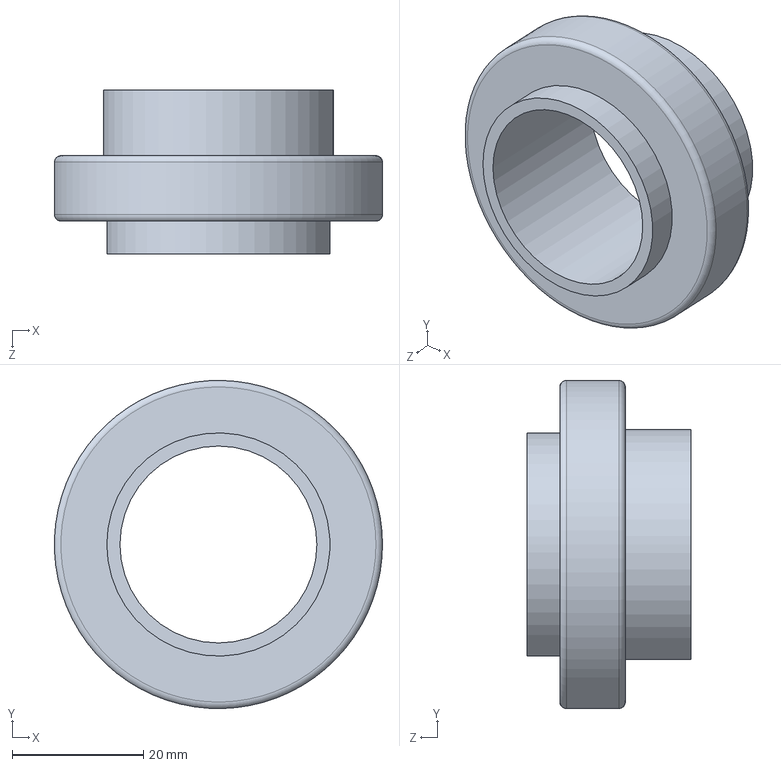
[picture p150: CAD file, 2020-04-30]
SLAB-wjmy/Engineering Documents /CAD Prototype/Bike_project/Project/fork_hub.SLDPRT
50.0 x 50.0 x 25.0 mm
