cledantec/Cycle-Atlanta-SLaB/SLAB-wjmy/Engineering Documents /CAD Prototype/Bike_project/seat_stand/hole_4part.SLDPRT

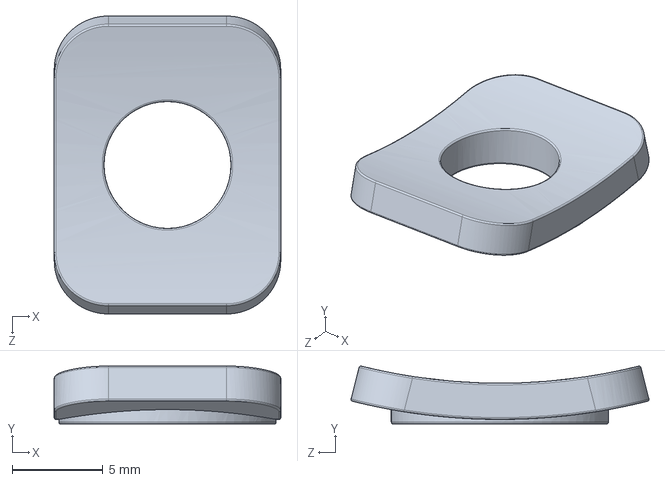
[picture p151: CAD file, 2020-04-30]
SLAB-wjmy/Engineering Documents /CAD Prototype/Bike_project/seat_stand/hole_4part.SLDPRT
12.5 x 3.20 x 16.4 mm
