cledantec/Cycle-Atlanta-SLaB/SLAB-wjmy/Engineering Documents /CAD Prototype/iphone-x-34.snapshot.3/iphonex.SLDPRT

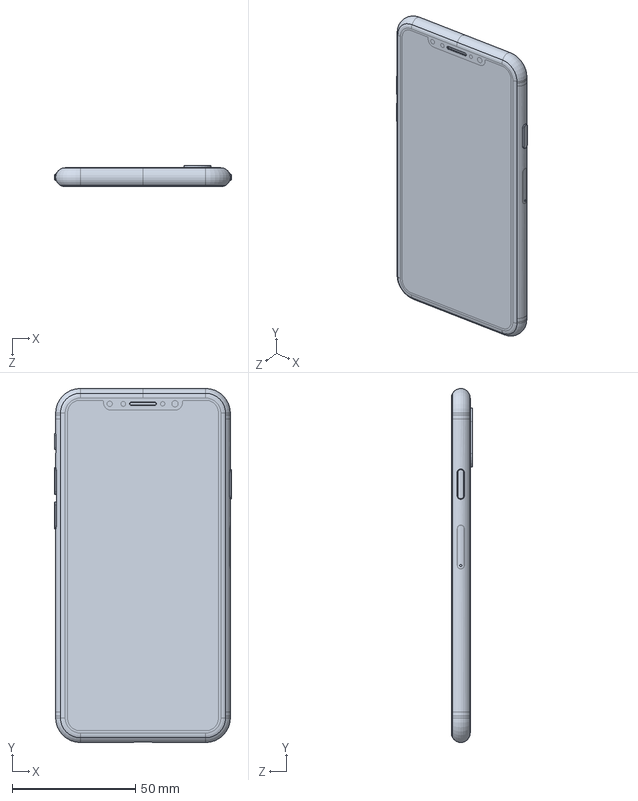
[picture p152: CAD file, 2020-04-30]
SLAB-wjmy/Engineering Documents /CAD Prototype/iphone-x-34.snapshot.3/iphonex.SLDPRT
71.9 x 143.6 x 8.70 mm
