cledantec/Cycle-Atlanta-SLaB/SLAB-wjmy/Engineering Documents /CAD Prototype/Package Prototype 1/FULL SIZE Version/Cutting/Back V1.DXF

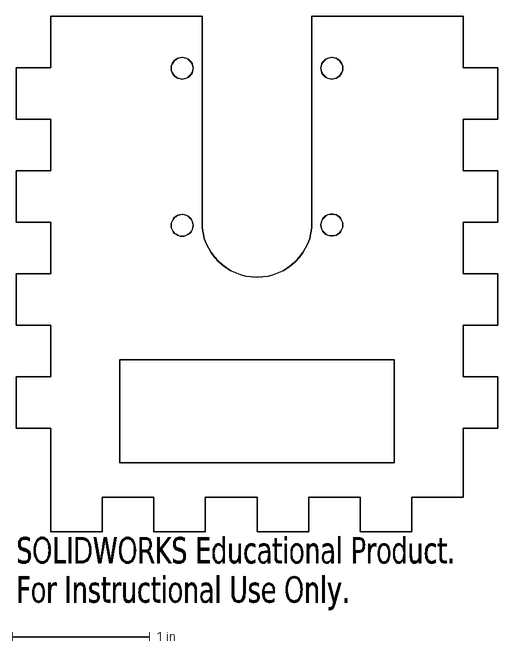
[picture p153: CAD file, 2020-04-30]
SLAB-wjmy/Engineering Documents /CAD Prototype/Package Prototype 1/FULL SIZE Version/Cutting/Back V1.DXF
SOLIDWORKS Educational Product.
For Instructional Use Only.
