cledantec/Cycle-Atlanta-SLaB/SLAB-wjmy/Engineering Documents /CAD Prototype/Package Prototype 1/FULL SIZE Version/Side V1.SLDPRT

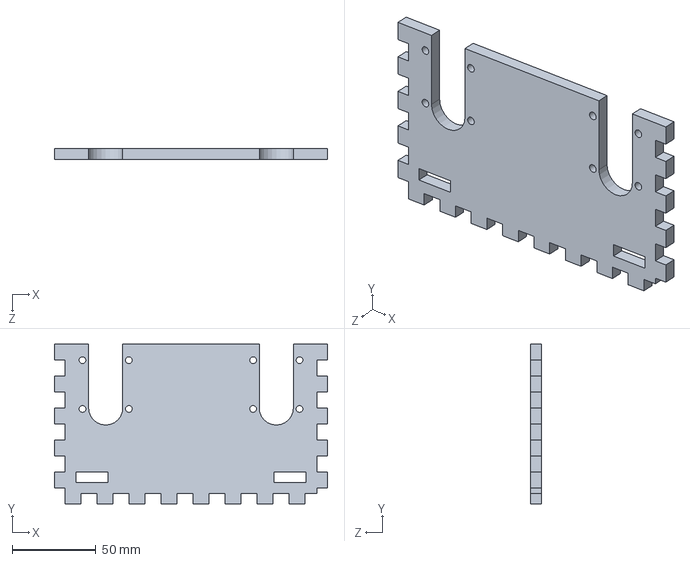
[picture p154: CAD file, 2020-04-30]
SLAB-wjmy/Engineering Documents /CAD Prototype/Package Prototype 1/FULL SIZE Version/Side V1.SLDPRT
162.6 x 95.2 x 6.35 mm
