cledantec/Cycle-Atlanta-SLaB/SLAB-wjmy/Engineering Documents /CAD Prototype/Package Prototype 1/THIN Version/Cutting - thin/Front V1-thin.DXF

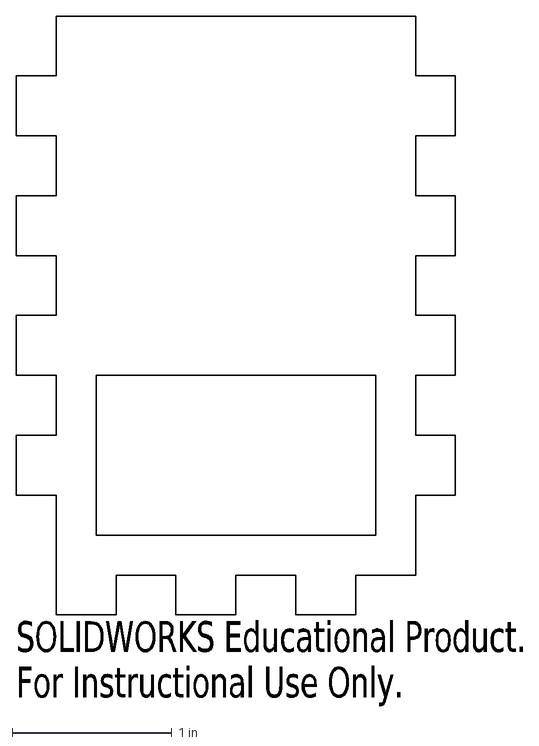
[picture p155: CAD file, 2020-04-30]
SLAB-wjmy/Engineering Documents /CAD Prototype/Package Prototype 1/THIN Version/Cutting - thin/Front V1-thin.DXF
SOLIDWORKS Educational Product.
For Instructional Use Only.
