cledantec/Cycle-Atlanta-SLaB/SLAB-wjmy/Engineering Documents /CAD Prototype/Package Prototype 1/THIN Version/Front V1-thin.SLDPRT

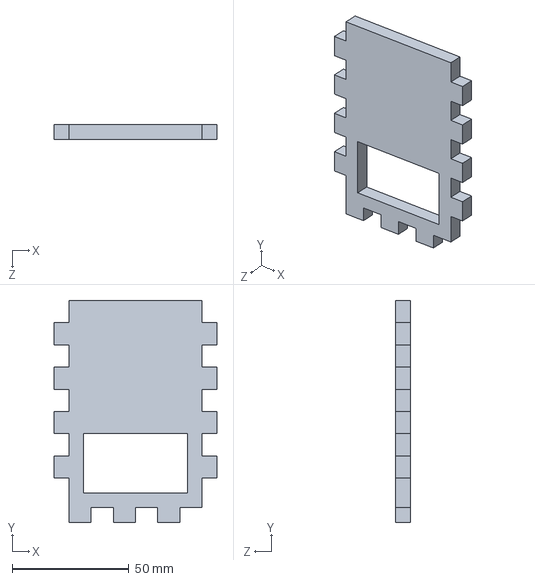
[picture p156: CAD file, 2020-04-30]
SLAB-wjmy/Engineering Documents /CAD Prototype/Package Prototype 1/THIN Version/Front V1-thin.SLDPRT
69.8 x 95.2 x 6.35 mm
