cledantec/Cycle-Atlanta-SLaB/Spring2017_implementations/3D parts/GopPro_Straight_Mount.A.3.stl

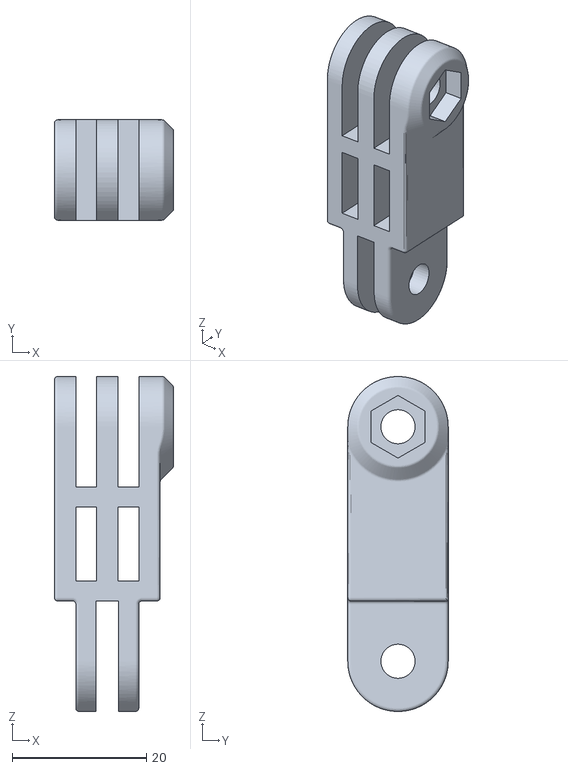
[picture p157: CAD file, 2017-04-22]
Spring2017_implementations/3D parts/GopPro_Straight_Mount.A.3.stl
17.8 x 15.0 x 50.0
