cledantec/Cycle-Atlanta-SLaB/DSSG2017_Case_Design/Front box/MatrixBaseMount.SLDPRT

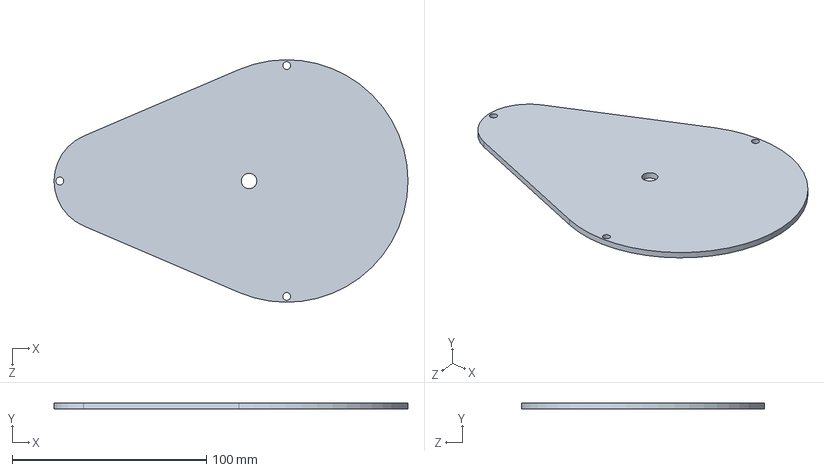
[picture p158: CAD file, 2017-07-28]
DSSG2017_Case_Design/Front box/MatrixBaseMount.SLDPRT
182.4 x 3.00 x 125.0 mm
