cledantec/Cycle-Atlanta-SLaB/SLAB-wjmy/Engineering Documents /CAD Prototype/arduino-uno-r3-1/arduino uno/unoboard blue.SLDPRT

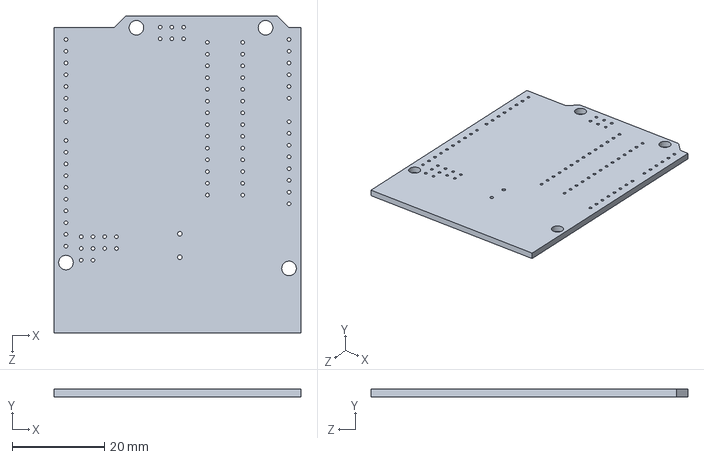
[picture p159: CAD file, 2020-04-30]
SLAB-wjmy/Engineering Documents /CAD Prototype/arduino-uno-r3-1/arduino uno/unoboard blue.SLDPRT
53.3 x 1.65 x 68.6 mm
