cledantec/Cycle-Atlanta-SLaB/SLAB-wjmy/Engineering Documents /CAD Prototype/Bike_project/bell/plate.SLDPRT

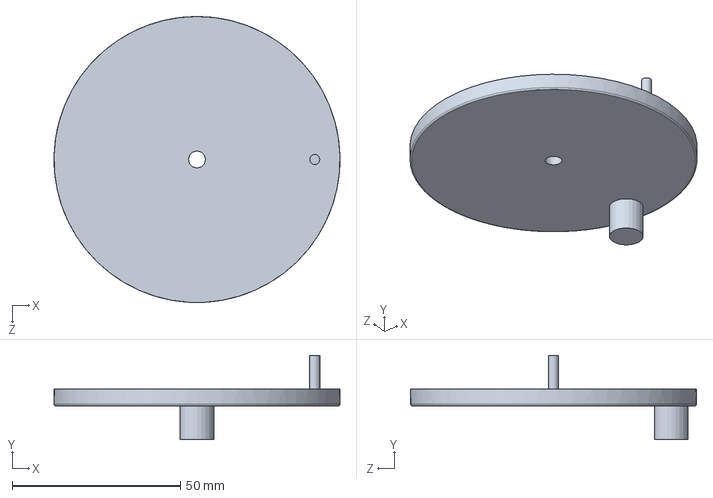
[picture p160: CAD file, 2020-04-30]
SLAB-wjmy/Engineering Documents /CAD Prototype/Bike_project/bell/plate.SLDPRT
85.0 x 25.0 x 85.0 mm
