cledantec/Cycle-Atlanta-SLaB/SLAB-wjmy/Engineering Documents /CAD Prototype/Bike_project/Break/Lever.SLDPRT

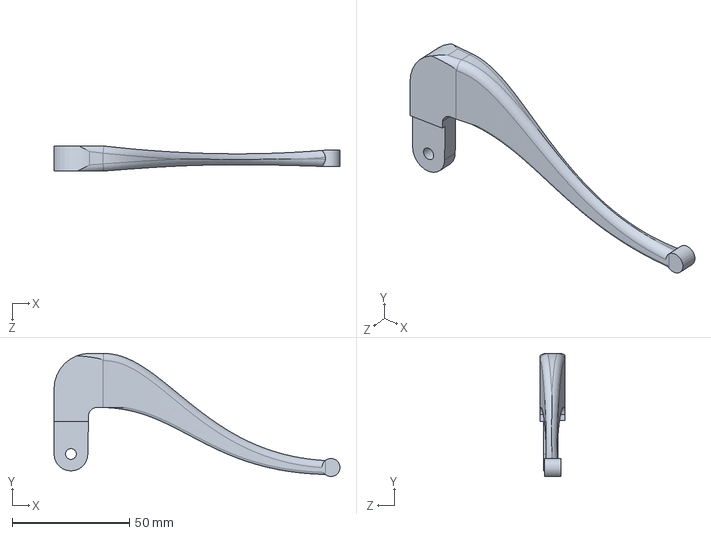
[picture p161: CAD file, 2020-04-30]
SLAB-wjmy/Engineering Documents /CAD Prototype/Bike_project/Break/Lever.SLDPRT
121.9 x 52.5 x 10.8 mm
