cledantec/Cycle-Atlanta-SLaB/SLAB-wjmy/Engineering Documents /CAD Prototype/Bike_project/Pedal_final/pedal_stand.SLDPRT

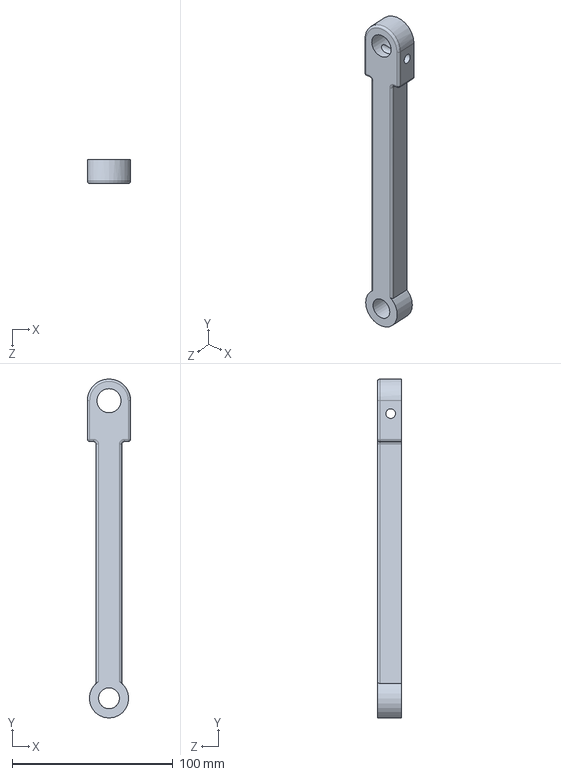
[picture p162: CAD file, 2020-04-30]
SLAB-wjmy/Engineering Documents /CAD Prototype/Bike_project/Pedal_final/pedal_stand.SLDPRT
27.0 x 210.8 x 15.0 mm
