cledantec/Cycle-Atlanta-SLaB/SLAB-wjmy/Engineering Documents /CAD Prototype/Bike_project/seat_stand/hole_5part.SLDPRT

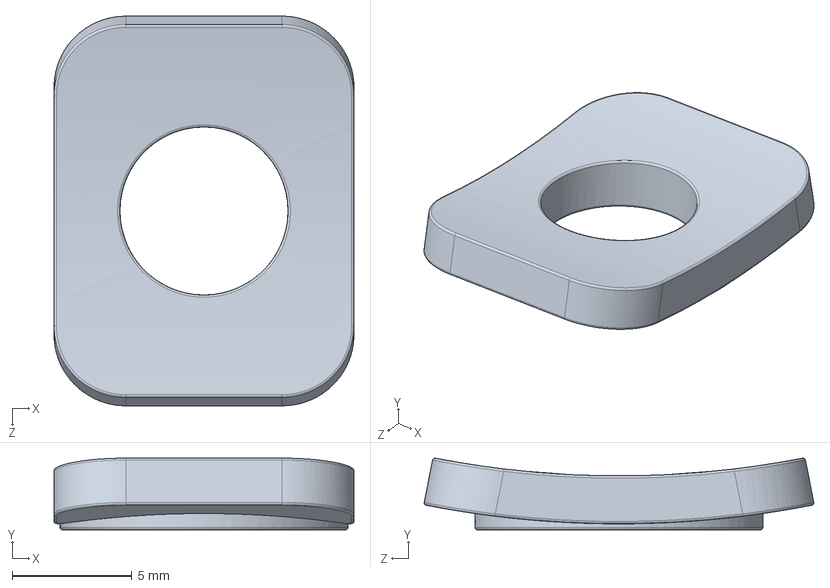
[picture p163: CAD file, 2020-04-30]
SLAB-wjmy/Engineering Documents /CAD Prototype/Bike_project/seat_stand/hole_5part.SLDPRT
12.5 x 2.99 x 16.2 mm
