cledantec/Cycle-Atlanta-SLaB/Spring2017_implementations/3D parts/PS3eye+laser.stl

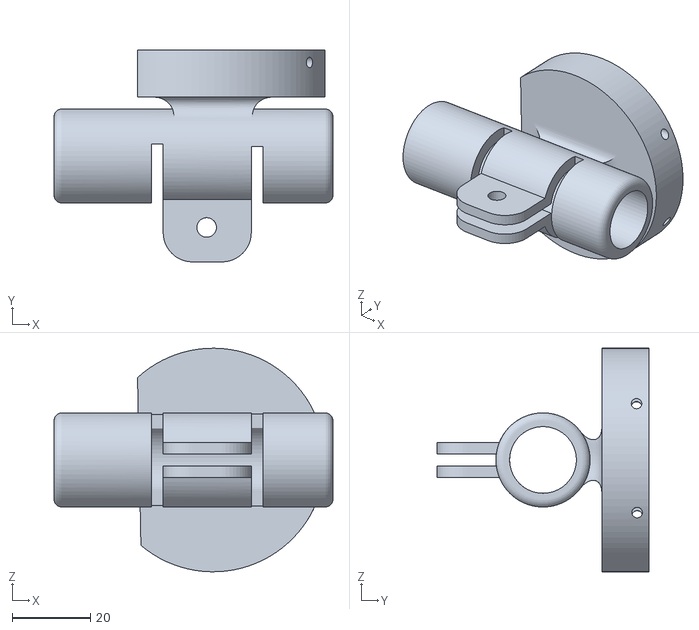
[picture p166: CAD file, 2017-04-22]
Spring2017_implementations/3D parts/PS3eye+laser.stl
71.1 x 54.0 x 57.0
