cledantec/Cycle-Atlanta-SLaB/DSSG2017_Case_Design/Front box/MatrixCaseTop.SLDPRT

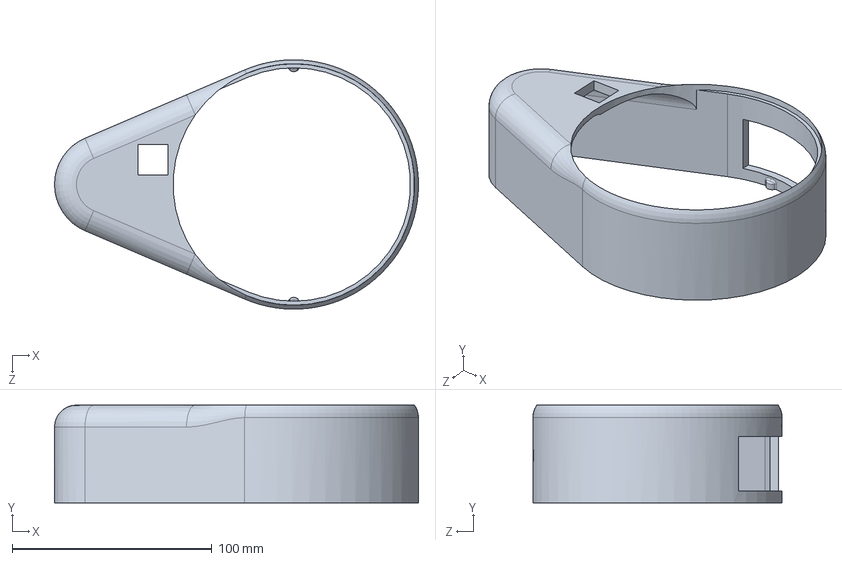
[picture p167: CAD file, 2017-07-28]
DSSG2017_Case_Design/Front box/MatrixCaseTop.SLDPRT
182.4 x 49.1 x 125.0 mm
