cledantec/Cycle-Atlanta-SLaB/SLAB-wjmy/Engineering Documents /CAD Prototype/arduino-uno-r3-1/arduino uno/220 RESISTOR PACK.SLDPRT

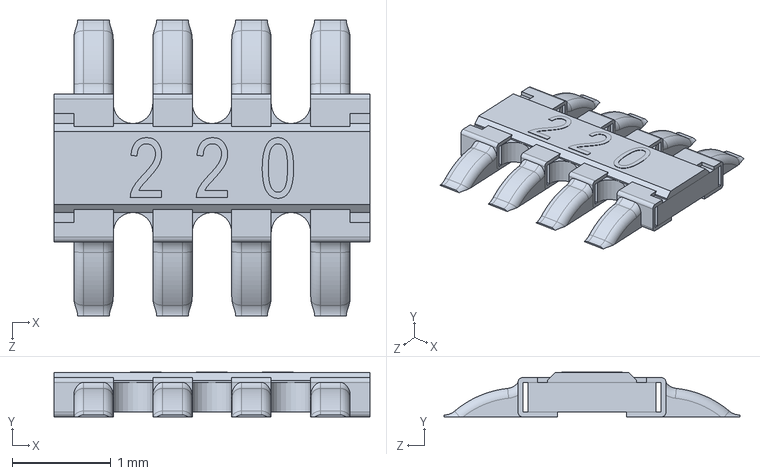
[picture p168: CAD file, 2020-04-30]
SLAB-wjmy/Engineering Documents /CAD Prototype/arduino-uno-r3-1/arduino uno/220 RESISTOR PACK.SLDPRT
3.20 x 0.455 x 3.00 mm
