cledantec/Cycle-Atlanta-SLaB/SLAB-wjmy/Engineering Documents /CAD Prototype/Bike_project/bell/lathi.SLDPRT

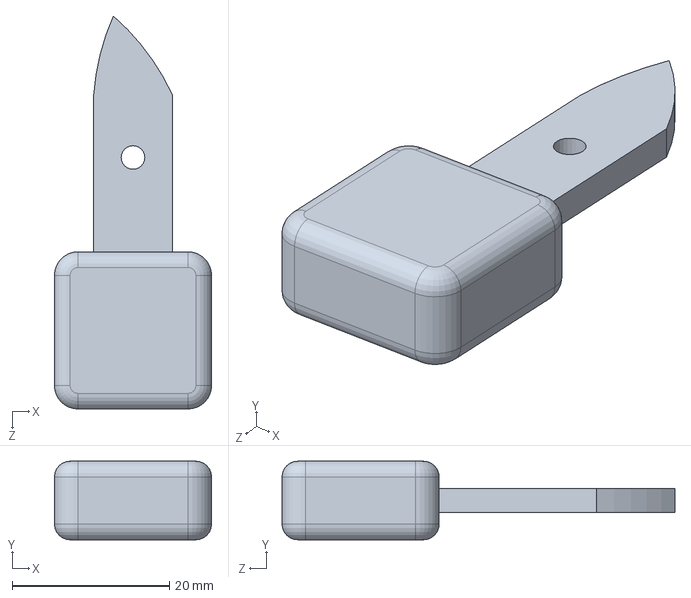
[picture p169: CAD file, 2020-04-30]
SLAB-wjmy/Engineering Documents /CAD Prototype/Bike_project/bell/lathi.SLDPRT
20.0 x 10.0 x 50.0 mm
