cledantec/Cycle-Atlanta-SLaB/SLAB-wjmy/Engineering Documents /CAD Prototype/Bike_project/Pedal_final/goj.SLDPRT

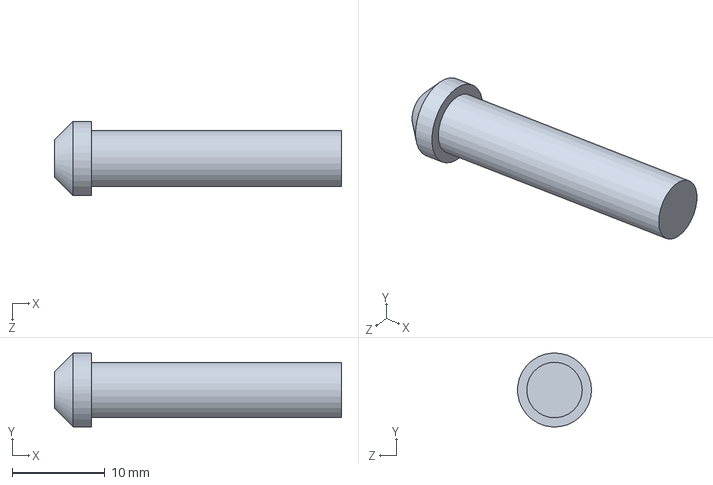
[picture p170: CAD file, 2020-04-30]
SLAB-wjmy/Engineering Documents /CAD Prototype/Bike_project/Pedal_final/goj.SLDPRT
31.0 x 7.99 x 8.00 mm
