cledantec/Cycle-Atlanta-SLaB/SLAB-wjmy/Engineering Documents /CAD Prototype/Bike_project/Project/final_fork.SLDPRT

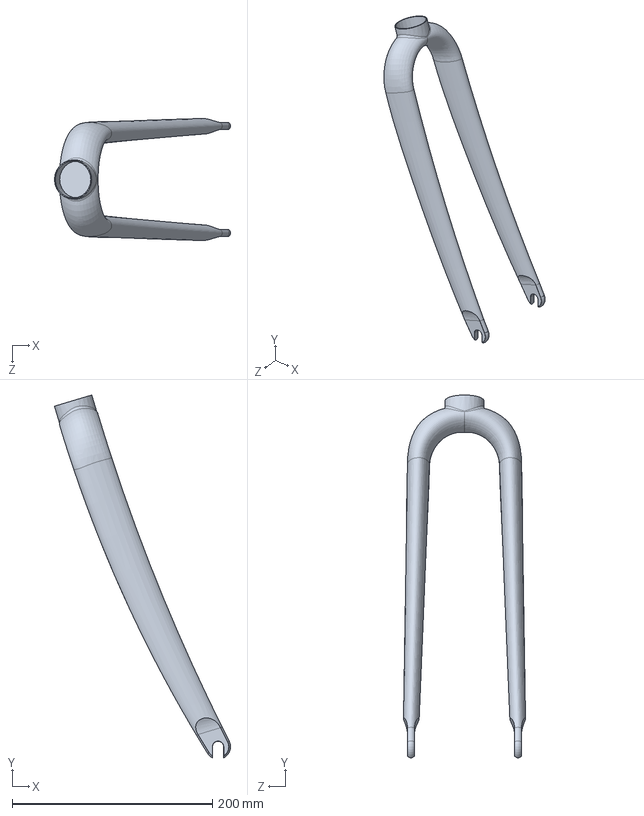
[picture p171: CAD file, 2020-04-30]
SLAB-wjmy/Engineering Documents /CAD Prototype/Bike_project/Project/final_fork.SLDPRT
176.0 x 362.7 x 122.0 mm
