cledantec/Cycle-Atlanta-SLaB/SLAB-wjmy/Engineering Documents /CAD Prototype/Bike_project/seat_stand/part_2.SLDPRT

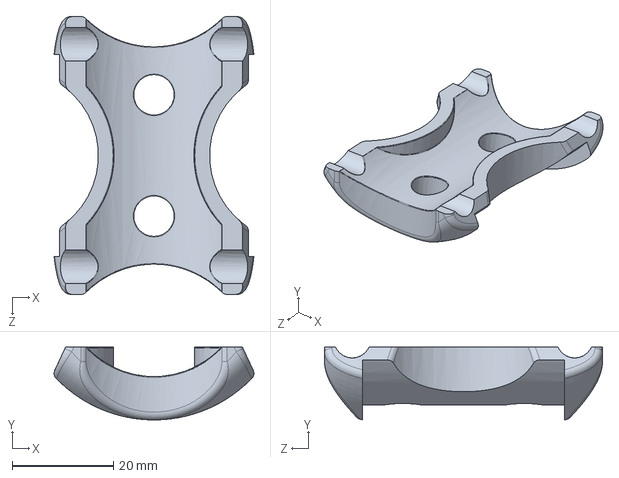
[picture p172: CAD file, 2020-04-30]
SLAB-wjmy/Engineering Documents /CAD Prototype/Bike_project/seat_stand/part_2.SLDPRT
39.6 x 14.4 x 55.0 mm
