cledantec/Cycle-Atlanta-SLaB/SLAB-wjmy/Engineering Documents /CAD Prototype/Package Prototype 1/THIN Version/Bottom V1-thin.SLDPRT

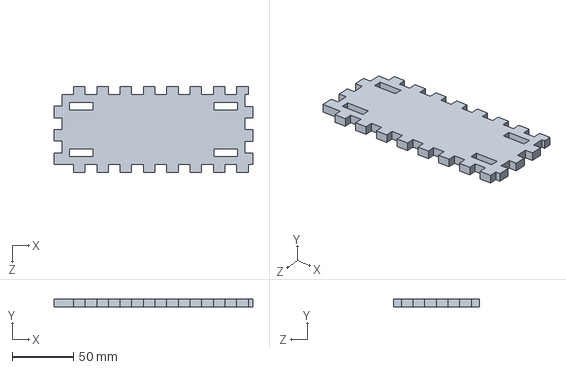
[picture p174: CAD file, 2020-04-30]
SLAB-wjmy/Engineering Documents /CAD Prototype/Package Prototype 1/THIN Version/Bottom V1-thin.SLDPRT
162.6 x 6.35 x 69.8 mm
