cledantec/Cycle-Atlanta-SLaB/SLAB-wjmy/Engineering Documents /CAD Prototype/Toggle Switch - No Mount.SLDPRT

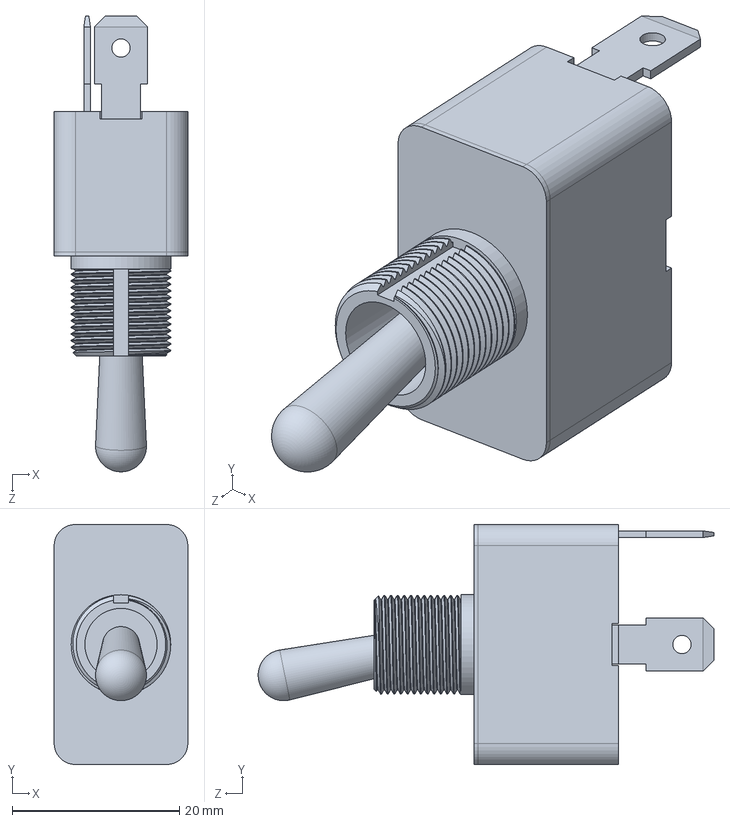
[picture p176: CAD file, 2020-04-30]
SLAB-wjmy/Engineering Documents /CAD Prototype/Toggle Switch - No Mount.SLDPRT
16.0 x 28.7 x 54.5 mm
