cledantec/Cycle-Atlanta-SLaB/Spring2017_implementations/3D parts/lenscap.stl

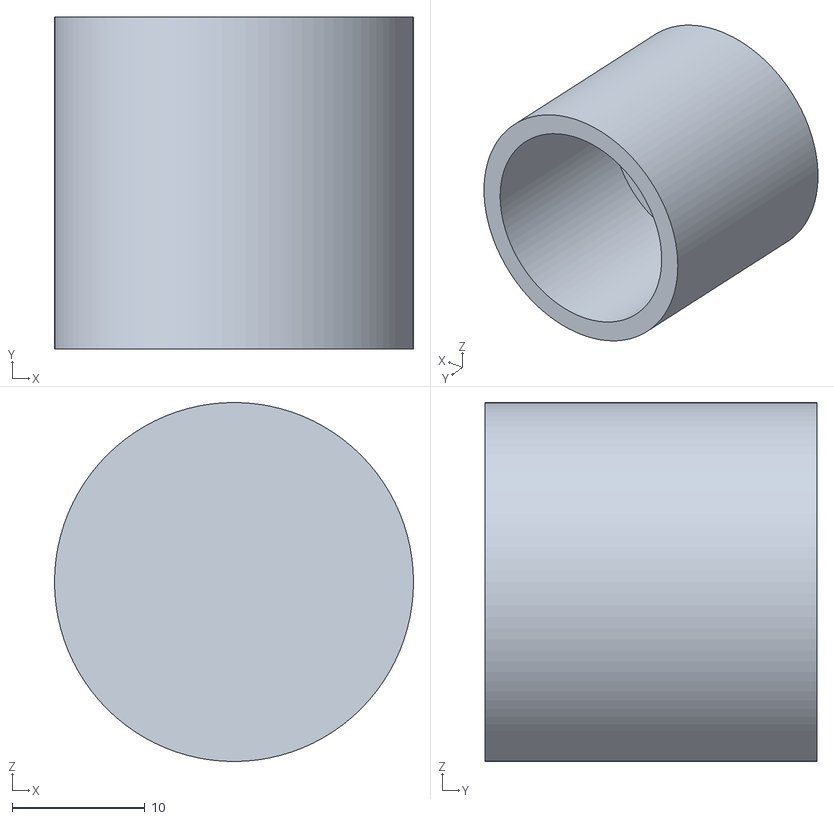
[picture p177: CAD file, 2017-04-22]
Spring2017_implementations/3D parts/lenscap.stl
27.0 x 25.0 x 27.0
