cledantec/Cycle-Atlanta-SLaB/SLAB-wjmy/Engineering Documents /CAD Prototype/Bike_project/bell/bell.SLDPRT

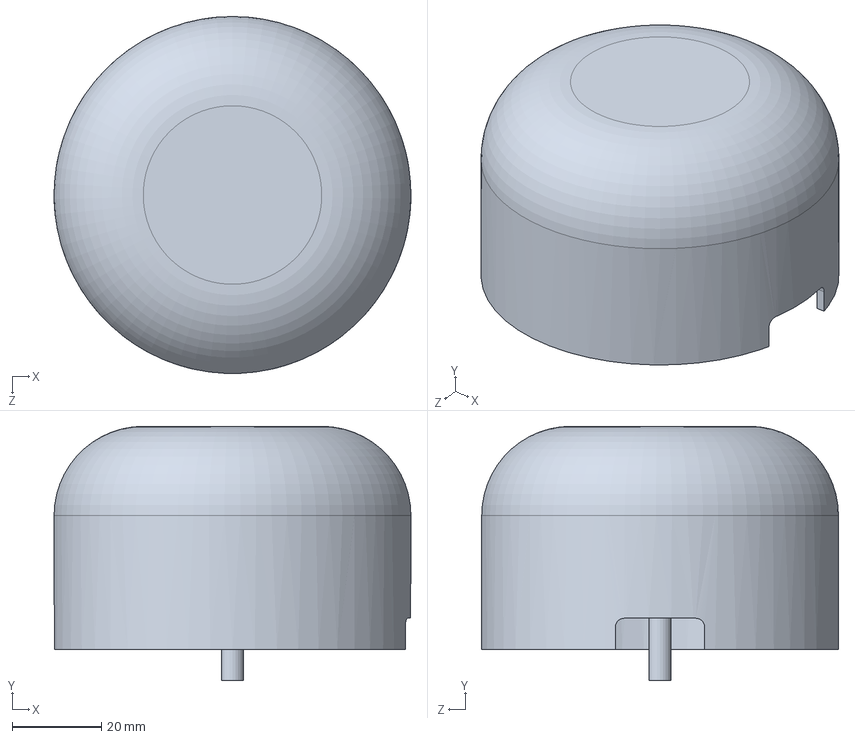
[picture p179: CAD file, 2020-04-30]
SLAB-wjmy/Engineering Documents /CAD Prototype/Bike_project/bell/bell.SLDPRT
80.0 x 57.0 x 80.0 mm
