cledantec/Cycle-Atlanta-SLaB/SLAB-wjmy/Engineering Documents /CAD Prototype/Bike_project/chain/inner_chain.SLDPRT

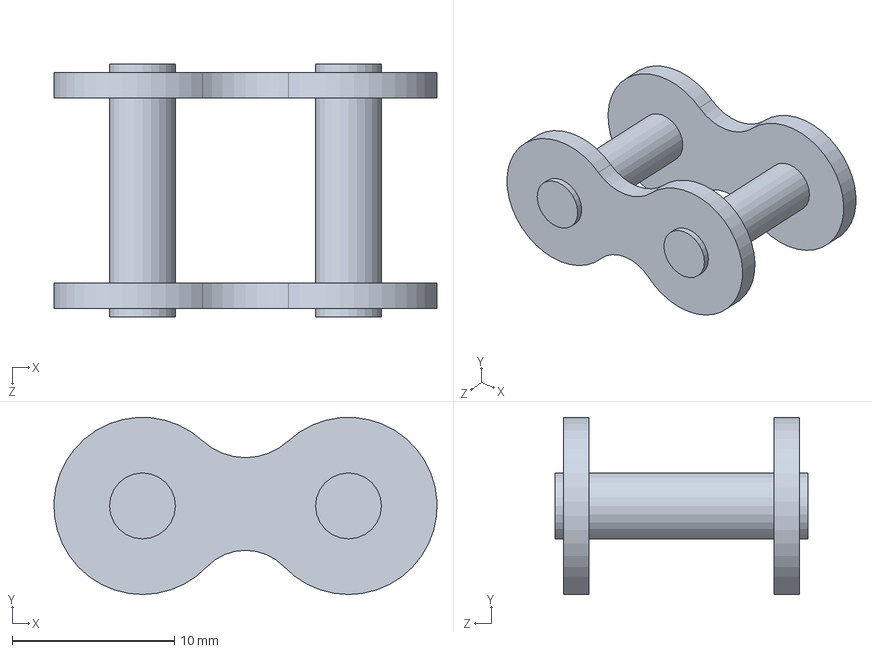
[picture p180: CAD file, 2020-04-30]
SLAB-wjmy/Engineering Documents /CAD Prototype/Bike_project/chain/inner_chain.SLDPRT
23.6 x 10.9 x 15.6 mm
