cledantec/Cycle-Atlanta-SLaB/SLAB-wjmy/Engineering Documents /CAD Prototype/Bike_project/Pedal_final/pedal.SLDPRT

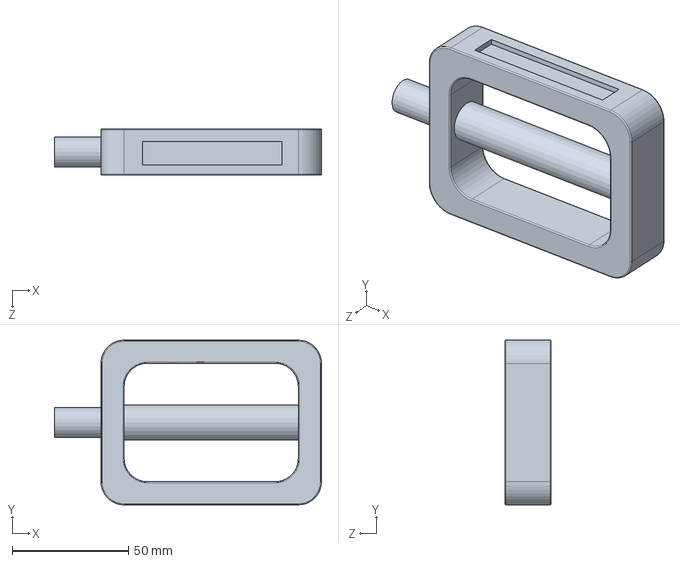
[picture p181: CAD file, 2020-04-30]
SLAB-wjmy/Engineering Documents /CAD Prototype/Bike_project/Pedal_final/pedal.SLDPRT
115.0 x 71.0 x 20.0 mm
