cledantec/Cycle-Atlanta-SLaB/SLAB-wjmy/Engineering Documents /CAD Prototype/Bike_project/Project/BreaK_TOP.SLDPRT

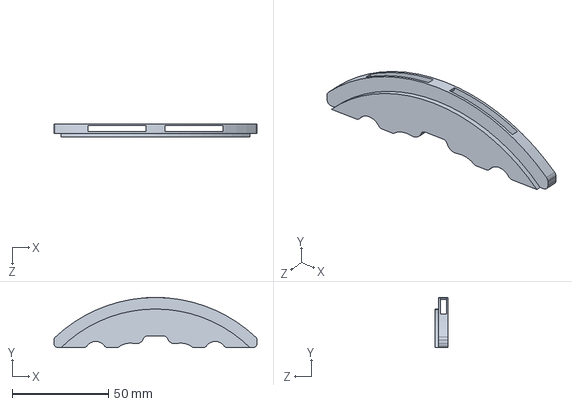
[picture p182: CAD file, 2020-04-30]
SLAB-wjmy/Engineering Documents /CAD Prototype/Bike_project/Project/BreaK_TOP.SLDPRT
105.3 x 26.0 x 7.00 mm
