cledantec/Cycle-Atlanta-SLaB/SLAB-wjmy/Engineering Documents /CAD Prototype/Bike_project/seat_stand/upper_part_3.SLDPRT

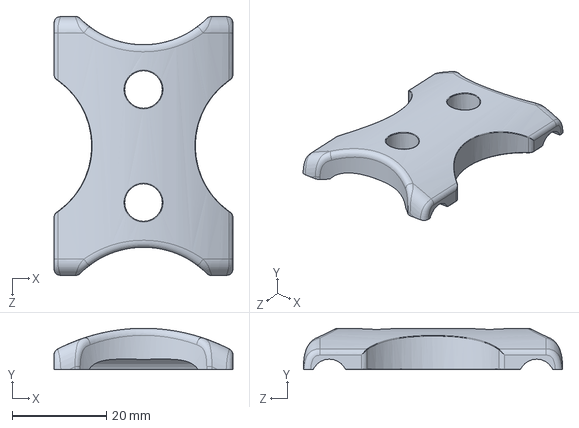
[picture p183: CAD file, 2020-04-30]
SLAB-wjmy/Engineering Documents /CAD Prototype/Bike_project/seat_stand/upper_part_3.SLDPRT
38.0 x 8.80 x 55.0 mm
