cledantec/Cycle-Atlanta-SLaB/SLAB-wjmy/Engineering Documents /CAD Prototype/Package Prototype 1/FULL SIZE Version/Cutting/Front V1.DXF

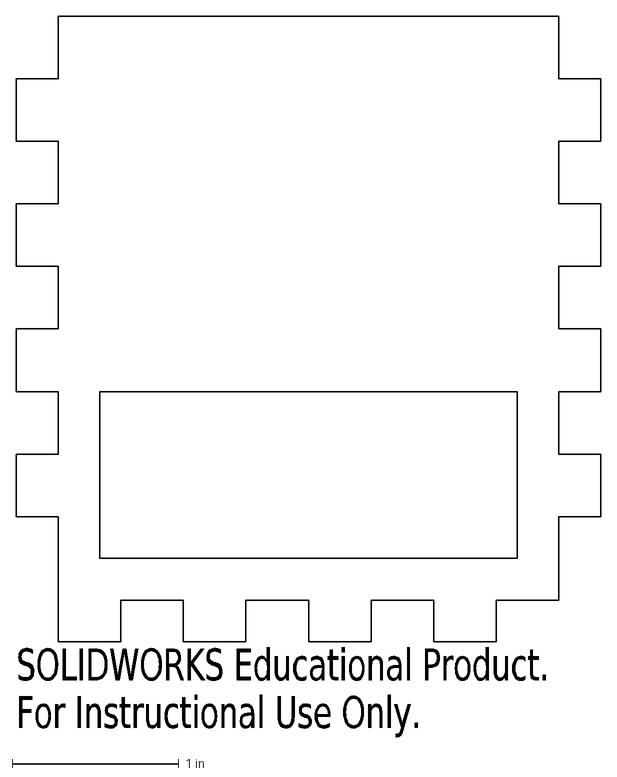
[picture p185: CAD file, 2020-04-30]
SLAB-wjmy/Engineering Documents /CAD Prototype/Package Prototype 1/FULL SIZE Version/Cutting/Front V1.DXF
SOLIDWORKS Educational Product.
For Instructional Use Only.
