cledantec/Cycle-Atlanta-SLaB/Spring2017_implementations/3D parts/bottom_mount.STL

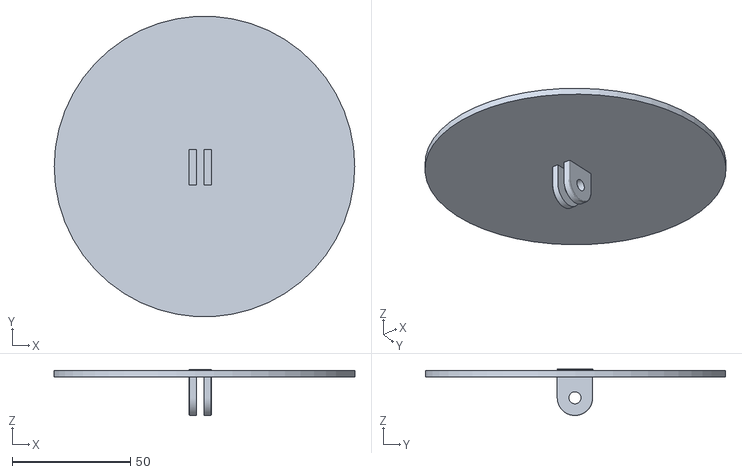
[picture p188: CAD file, 2017-04-22]
Spring2017_implementations/3D parts/bottom_mount.STL
127.2 x 126.9 x 19.5
