cledantec/Cycle-Atlanta-SLaB/SLAB-wjmy/Engineering Documents /CAD Prototype/Bike_project/chain/bold.SLDPRT

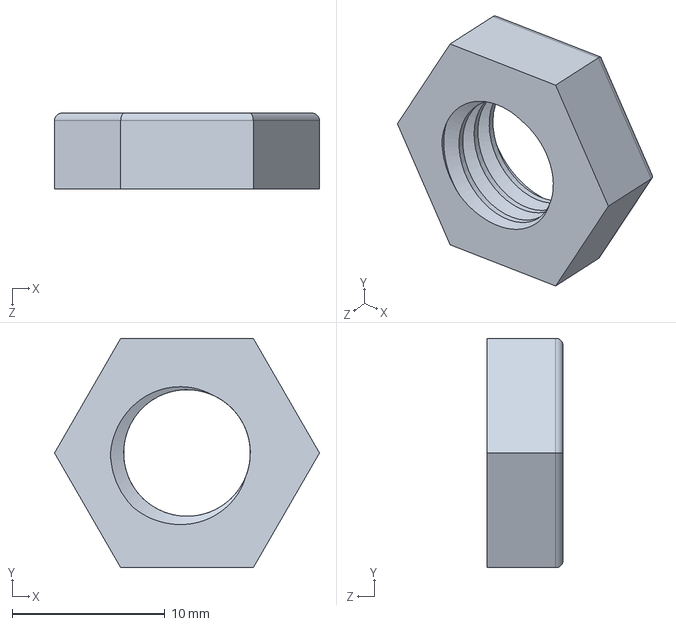
[picture p190: CAD file, 2020-04-30]
SLAB-wjmy/Engineering Documents /CAD Prototype/Bike_project/chain/bold.SLDPRT
17.3 x 15.0 x 5.00 mm
