cledantec/Cycle-Atlanta-SLaB/SLAB-wjmy/Engineering Documents /CAD Prototype/Bike_project/Pedal_final/axis.SLDPRT

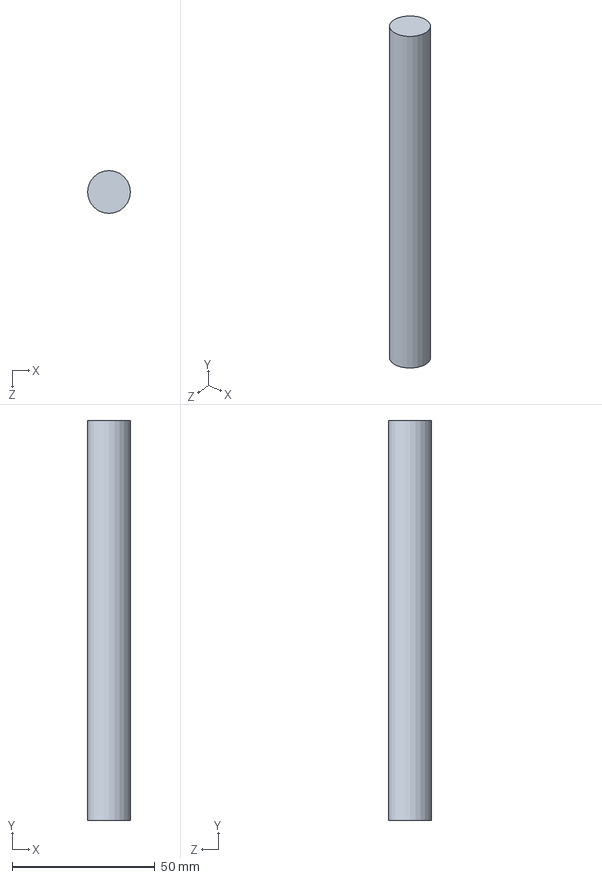
[picture p191: CAD file, 2020-04-30]
SLAB-wjmy/Engineering Documents /CAD Prototype/Bike_project/Pedal_final/axis.SLDPRT
15.0 x 140.0 x 15.0 mm
