cledantec/Cycle-Atlanta-SLaB/SLAB-wjmy/Engineering Documents /CAD Prototype/Bike_project/Project/seat_stand_joint.SLDPRT

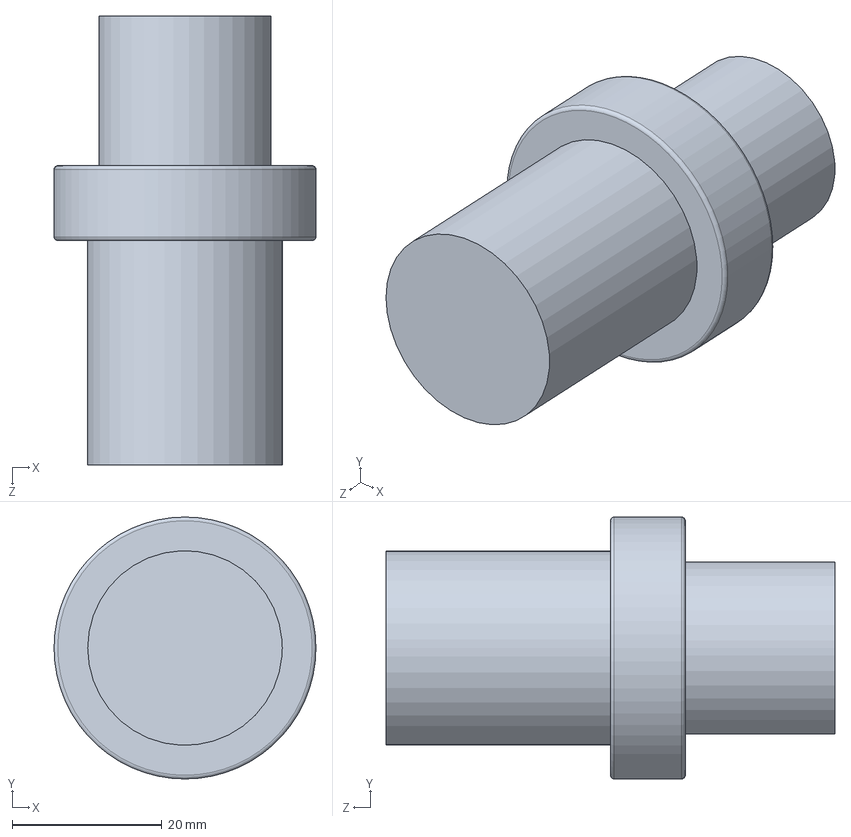
[picture p192: CAD file, 2020-04-30]
SLAB-wjmy/Engineering Documents /CAD Prototype/Bike_project/Project/seat_stand_joint.SLDPRT
35.0 x 35.0 x 60.0 mm
