cledantec/Cycle-Atlanta-SLaB/SLAB-wjmy/Engineering Documents /CAD Prototype/Bike_project/seat_stand/seat_cover.SLDPRT

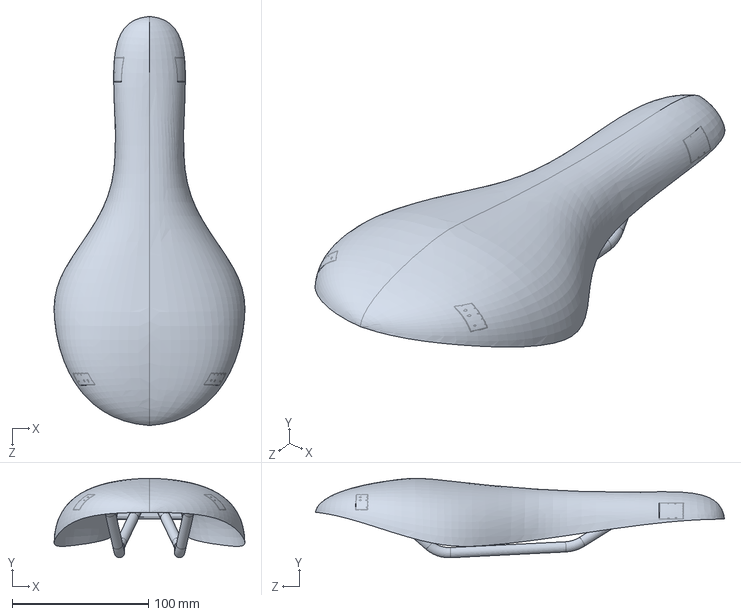
[picture p193: CAD file, 2020-04-30]
SLAB-wjmy/Engineering Documents /CAD Prototype/Bike_project/seat_stand/seat_cover.SLDPRT
140.0 x 58.3 x 300.0 mm
