cledantec/Cycle-Atlanta-SLaB/Spring2017_implementations/3D parts/MATRIX Creator Case Bottom.stl

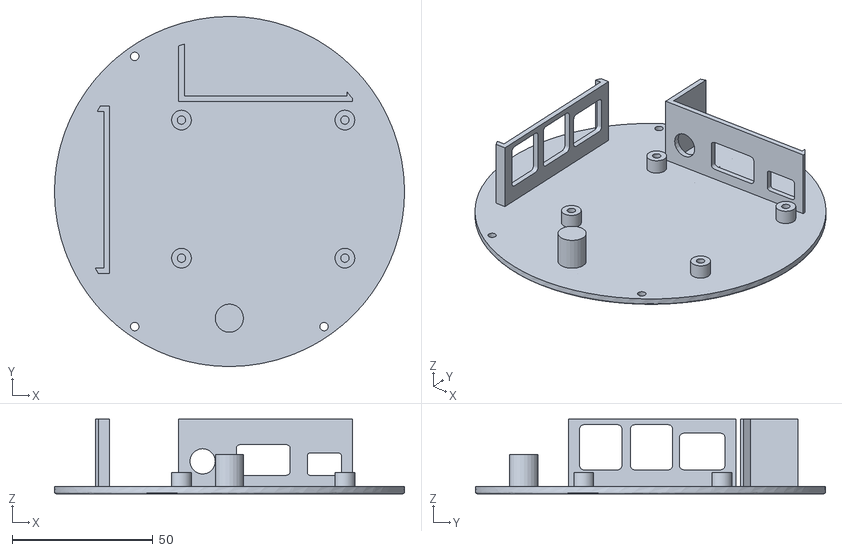
[picture p194: CAD file, 2017-04-22]
Spring2017_implementations/3D parts/MATRIX Creator Case Bottom.stl
124.2 x 124.2 x 26.5
