cledantec/Cycle-Atlanta-SLaB/SLAB-wjmy/Engineering Documents /CAD Prototype/Bike_project/Project/join_upper.SLDPRT

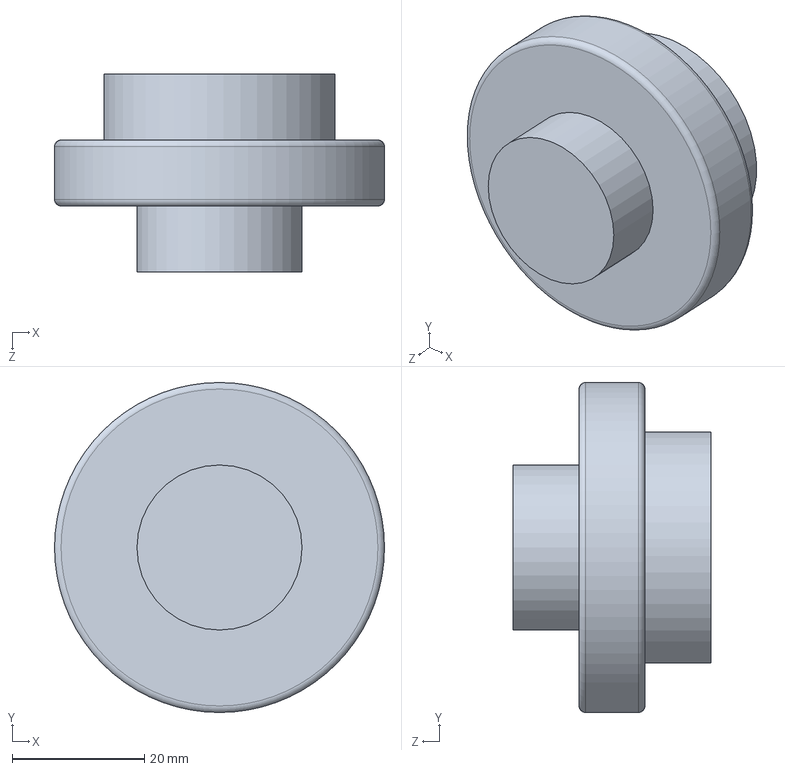
[picture p196: CAD file, 2020-04-30]
SLAB-wjmy/Engineering Documents /CAD Prototype/Bike_project/Project/join_upper.SLDPRT
50.0 x 50.0 x 30.0 mm
