cledantec/Cycle-Atlanta-SLaB/SLAB-wjmy/Engineering Documents /CAD Prototype/arduino-uno-r3-1/arduino uno/10 PORT HEADER.SLDPRT

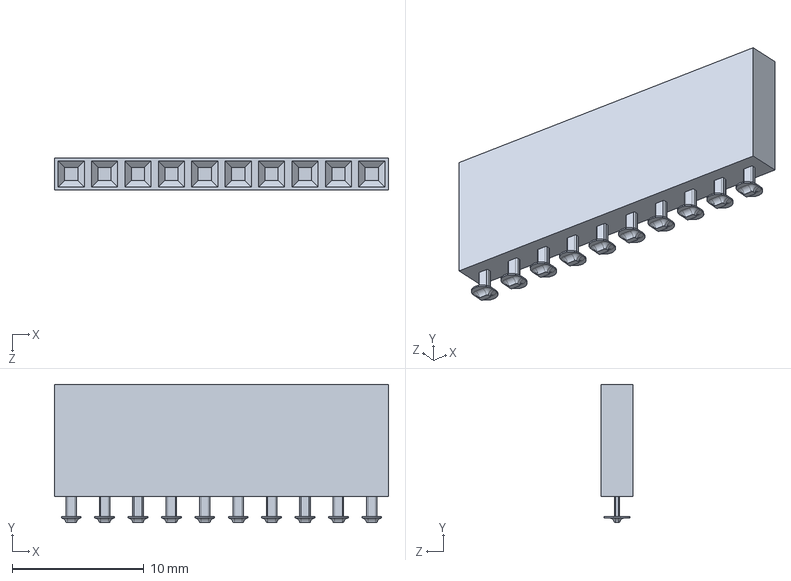
[picture p199: CAD file, 2020-04-30]
SLAB-wjmy/Engineering Documents /CAD Prototype/arduino-uno-r3-1/arduino uno/10 PORT HEADER.SLDPRT
25.4 x 10.5 x 2.41 mm
