cledantec/Cycle-Atlanta-SLaB/SLAB-wjmy/Engineering Documents /CAD Prototype/Bike_project/Project/break_parts2.SLDPRT

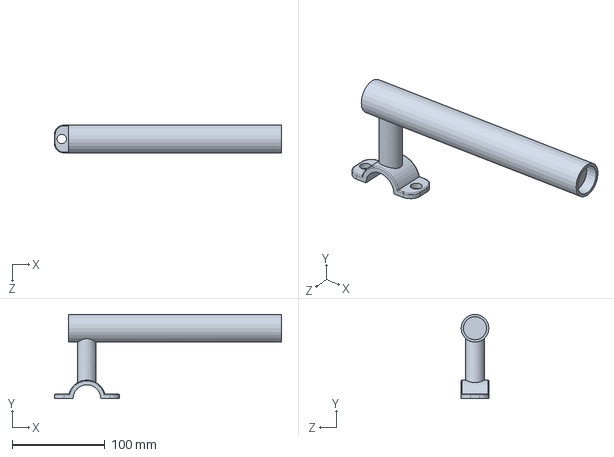
[picture p200: CAD file, 2020-04-30]
SLAB-wjmy/Engineering Documents /CAD Prototype/Bike_project/Project/break_parts2.SLDPRT
245.0 x 91.0 x 30.0 mm
