cledantec/Cycle-Atlanta-SLaB/SLAB-wjmy/Engineering Documents /CAD Prototype/Bike_project/Project/Sprocket.SLDPRT

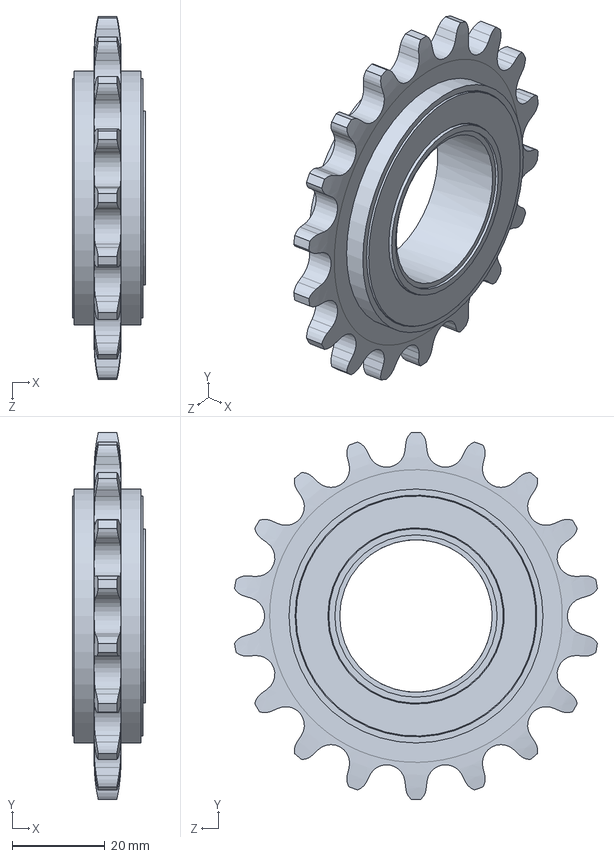
[picture p206: CAD file, 2020-04-30]
SLAB-wjmy/Engineering Documents /CAD Prototype/Bike_project/Project/Sprocket.SLDPRT
15.8 x 79.0 x 78.1 mm
