cledantec/Cycle-Atlanta-SLaB/SLAB-wjmy/Engineering Documents /CAD Prototype/arduino-uno-r3-1/arduino uno/mf-msmf050-2.SLDPRT

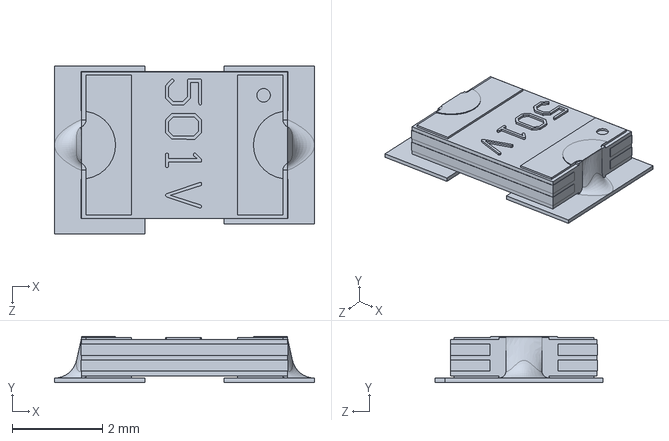
[picture p207: CAD file, 2020-04-30]
SLAB-wjmy/Engineering Documents /CAD Prototype/arduino-uno-r3-1/arduino uno/mf-msmf050-2.SLDPRT
5.75 x 1.02 x 3.72 mm
