cledantec/Cycle-Atlanta-SLaB/SLAB-wjmy/Engineering Documents /CAD Prototype/Bike_project/Project/spoket_joint.SLDPRT

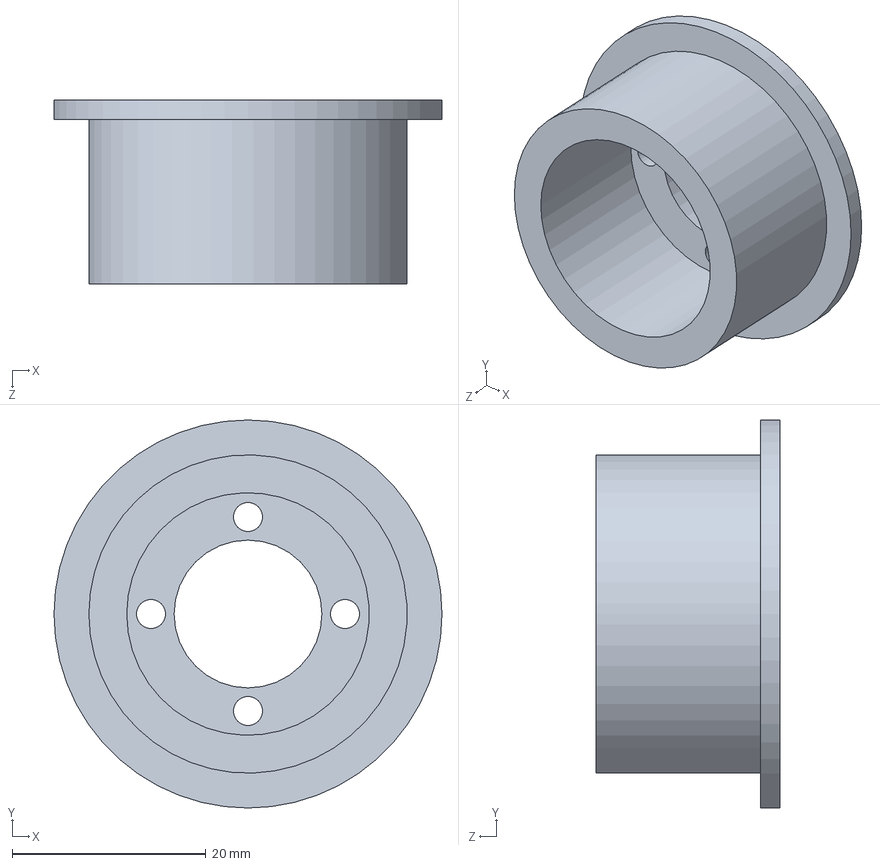
[picture p208: CAD file, 2020-04-30]
SLAB-wjmy/Engineering Documents /CAD Prototype/Bike_project/Project/spoket_joint.SLDPRT
40.0 x 40.0 x 19.0 mm
