cledantec/Cycle-Atlanta-SLaB/SLAB-wjmy/Engineering Documents /CAD Prototype/Box Bottom Half.SLDPRT

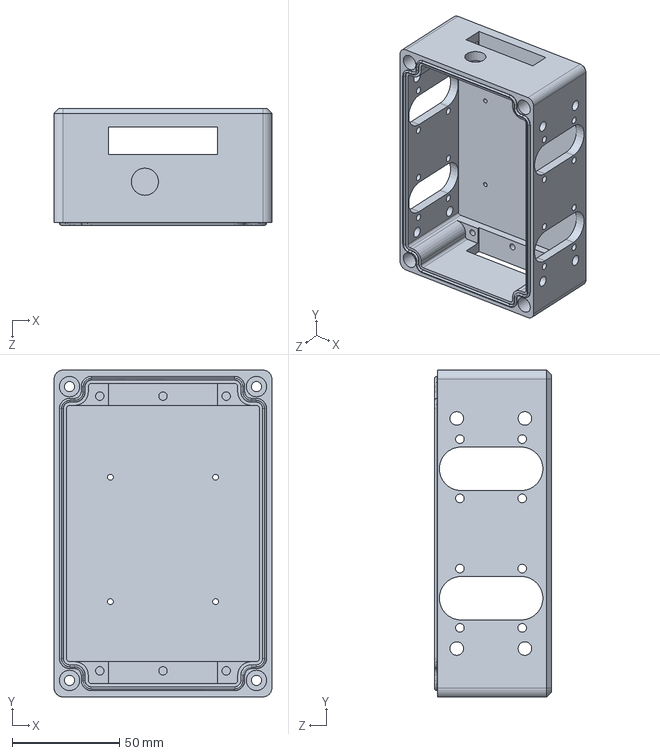
[picture p209: CAD file, 2020-04-30]
SLAB-wjmy/Engineering Documents /CAD Prototype/Box Bottom Half.SLDPRT
101.6 x 152.4 x 54.4 mm
