cledantec/Cycle-Atlanta-SLaB/SLAB-wjmy/Engineering Documents /CAD Prototype/Bike_project/Project/partshandle.SLDPRT

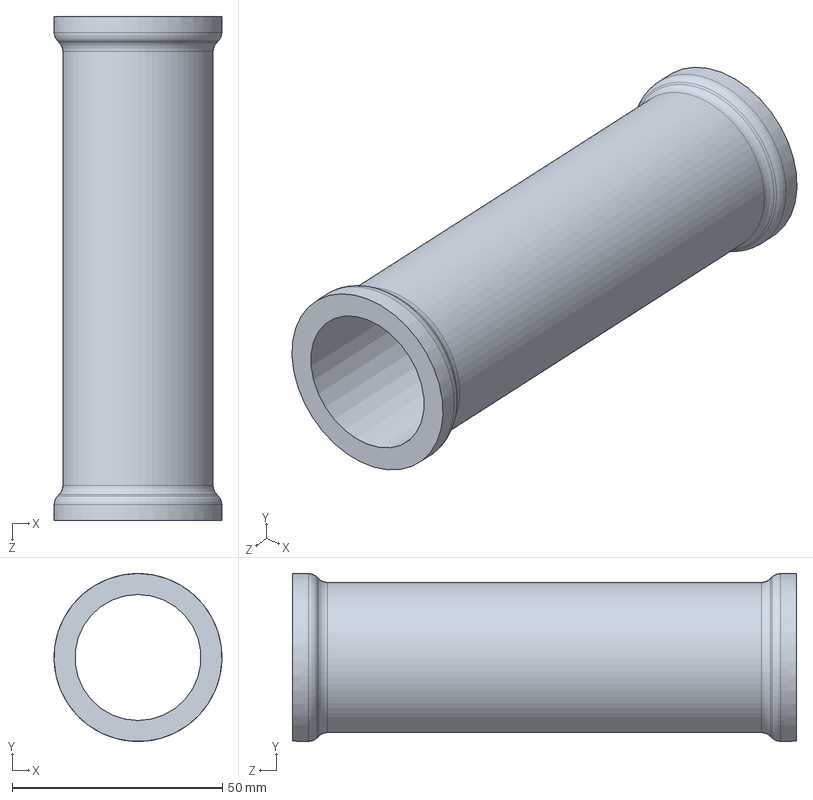
[picture p211: CAD file, 2020-04-30]
SLAB-wjmy/Engineering Documents /CAD Prototype/Bike_project/Project/partshandle.SLDPRT
40.0 x 40.0 x 120.0 mm
