cledantec/Cycle-Atlanta-SLaB/SLAB-wjmy/Engineering Documents /CAD Prototype/Custom PCB.SLDPRT

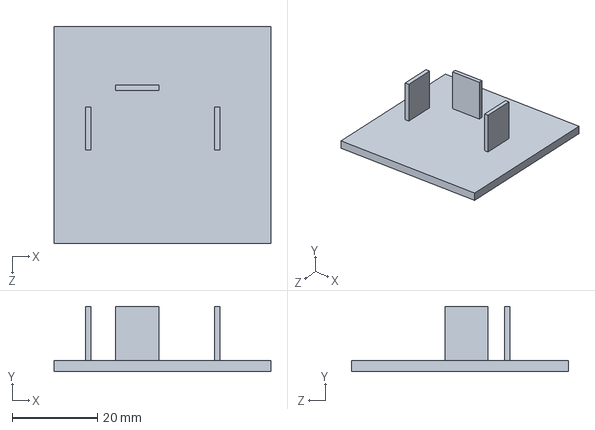
[picture p213: CAD file, 2020-04-30]
SLAB-wjmy/Engineering Documents /CAD Prototype/Custom PCB.SLDPRT
50.8 x 15.2 x 50.8 mm
