cledantec/Cycle-Atlanta-SLaB/SLAB-wjmy/Engineering Documents /CAD Prototype/arduino-uno-r3-1/arduino uno/47uf CAP Dcase.SLDPRT

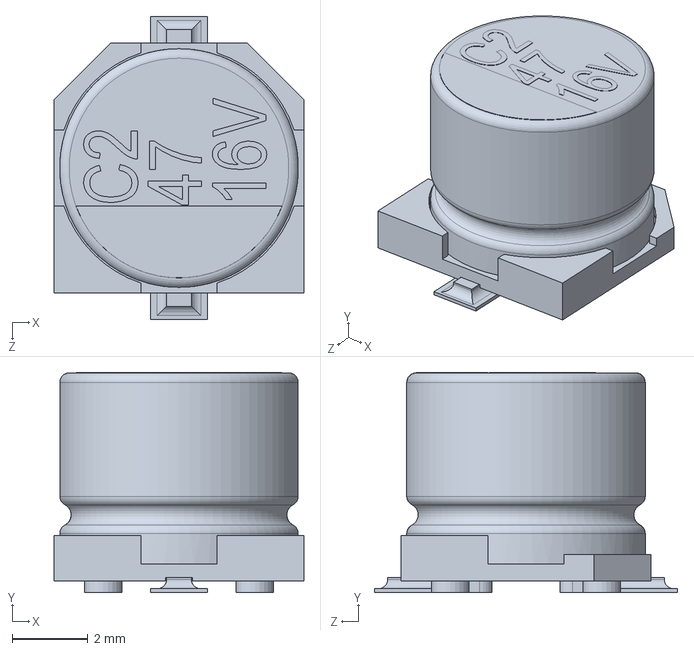
[picture p214: CAD file, 2020-04-30]
SLAB-wjmy/Engineering Documents /CAD Prototype/arduino-uno-r3-1/arduino uno/47uf CAP Dcase.SLDPRT
6.60 x 5.81 x 8.00 mm
