cledantec/Cycle-Atlanta-SLaB/SLAB-wjmy/Engineering Documents /CAD Prototype/Bike_project/Project/handle_new_bar.SLDPRT

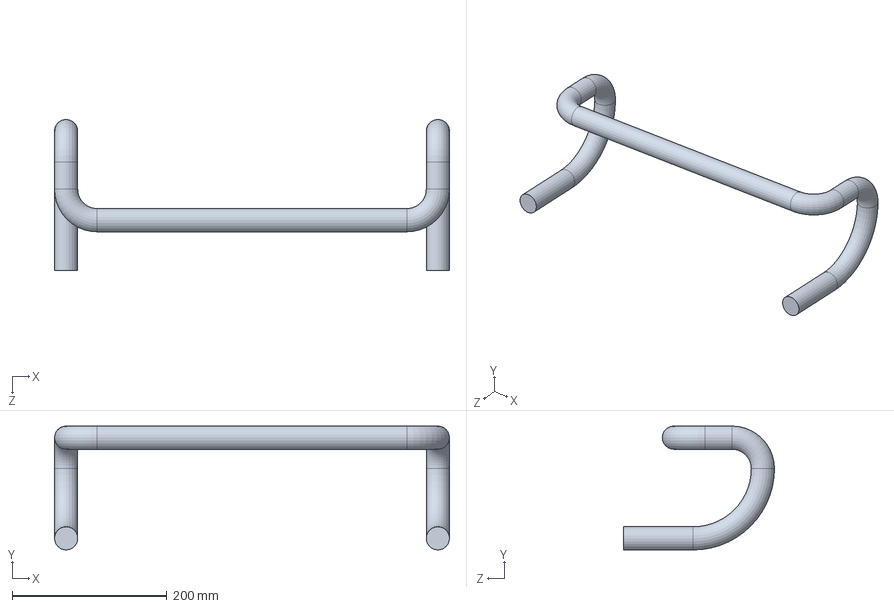
[picture p217: CAD file, 2020-04-30]
SLAB-wjmy/Engineering Documents /CAD Prototype/Bike_project/Project/handle_new_bar.SLDPRT
510.0 x 160.0 x 195.0 mm
