cledantec/Cycle-Atlanta-SLaB/SLAB-wjmy/Engineering Documents /CAD Prototype/Box Top Half.sldprt

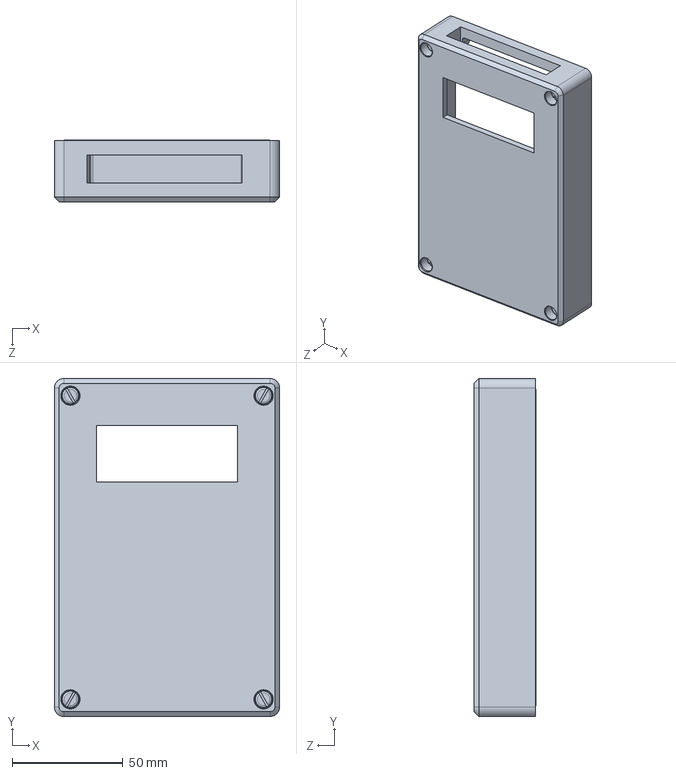
[picture p218: CAD file, 2020-04-30]
SLAB-wjmy/Engineering Documents /CAD Prototype/Box Top Half.sldprt
101.6 x 152.4 x 27.8 mm
