cledantec/Cycle-Atlanta-SLaB/SLAB-wjmy/Engineering Documents /CAD Prototype/Bike_project/Project/break_parts.SLDPRT

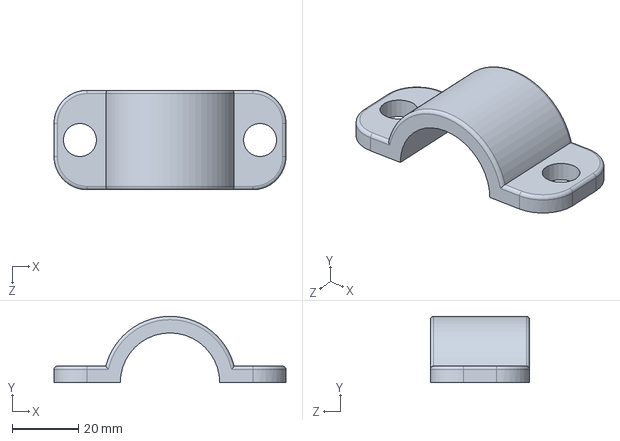
[picture p221: CAD file, 2020-04-30]
SLAB-wjmy/Engineering Documents /CAD Prototype/Bike_project/Project/break_parts.SLDPRT
70.0 x 20.0 x 30.0 mm
