cledantec/Cycle-Atlanta-SLaB/SLAB-wjmy/Engineering Documents /CAD Prototype/Toggle Switch - Mount Only.sldprt

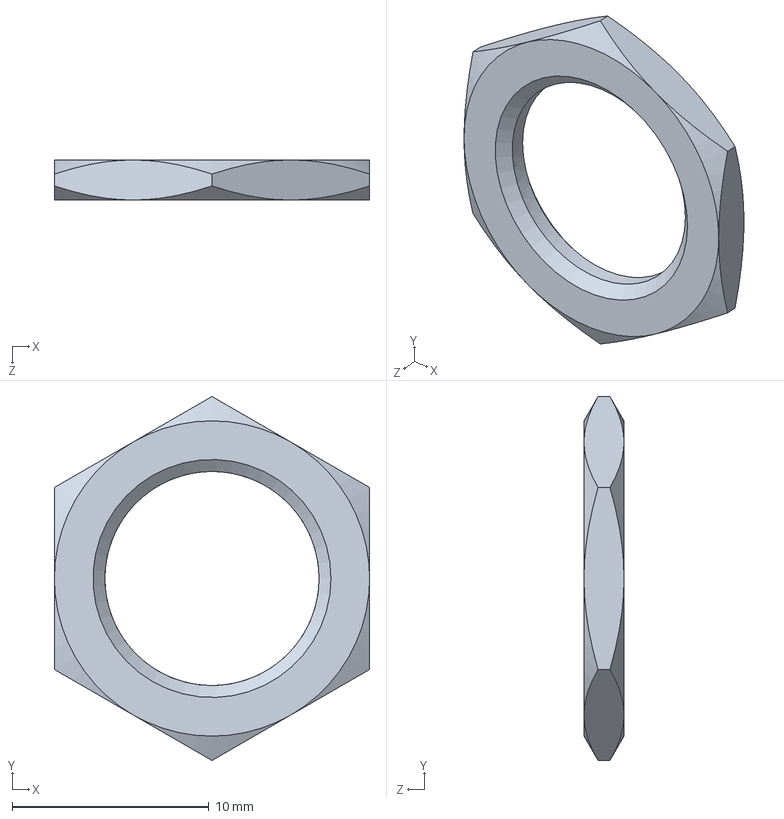
[picture p222: CAD file, 2020-04-30]
SLAB-wjmy/Engineering Documents /CAD Prototype/Toggle Switch - Mount Only.sldprt
16.0 x 18.5 x 2.03 mm
