cledantec/Cycle-Atlanta-SLaB/SLAB-wjmy/Engineering Documents /CAD Prototype/Battery Pack - Big.SLDPRT

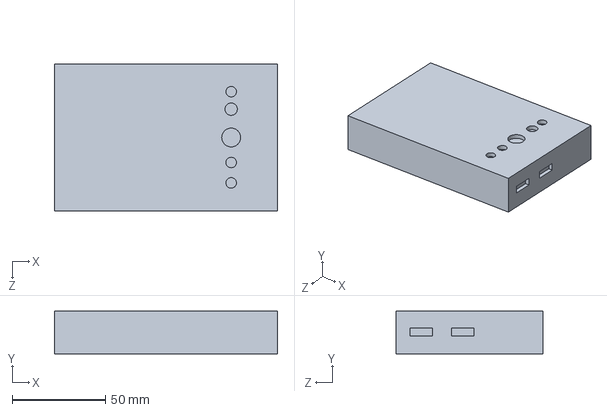
[picture p224: CAD file, 2020-04-30]
SLAB-wjmy/Engineering Documents /CAD Prototype/Battery Pack - Big.SLDPRT
119.4 x 22.9 x 78.7 mm
