cledantec/Cycle-Atlanta-SLaB/SLAB-wjmy/Engineering Documents /CAD Prototype/arduino-uno-r3-1/arduino uno/603 cap on pad.SLDPRT

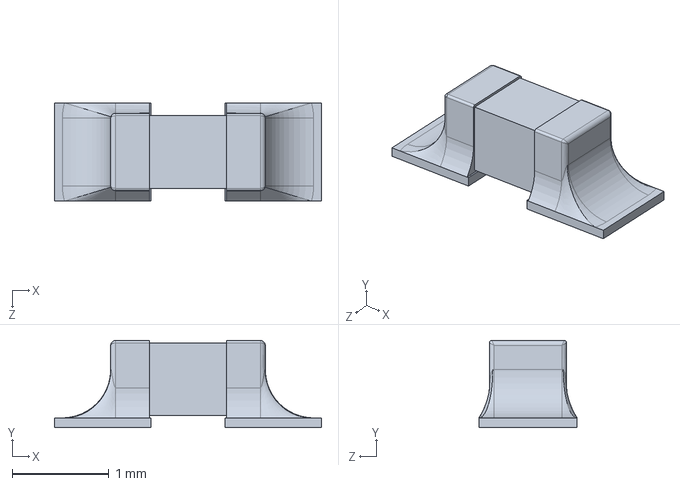
[picture p227: CAD file, 2020-04-30]
SLAB-wjmy/Engineering Documents /CAD Prototype/arduino-uno-r3-1/arduino uno/603 cap on pad.SLDPRT
2.76 x 0.9 x 1.02 mm
