cledantec/Cycle-Atlanta-SLaB/SLAB-wjmy/Engineering Documents /CAD Prototype/arduino-uno-r3-1/arduino uno/8 PORT HEADER.SLDPRT

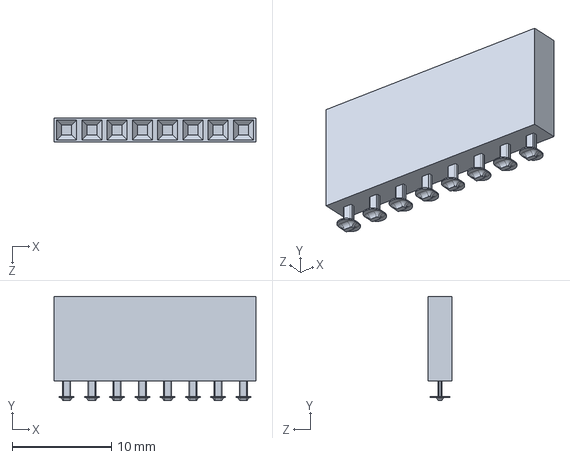
[picture p228: CAD file, 2020-04-30]
SLAB-wjmy/Engineering Documents /CAD Prototype/arduino-uno-r3-1/arduino uno/8 PORT HEADER.SLDPRT
20.3 x 10.5 x 2.41 mm
