cledantec/Cycle-Atlanta-SLaB/SLAB-wjmy/Engineering Documents /CAD Prototype/arduino-uno-r3-1/arduino uno/6 PORT HEADER.SLDPRT

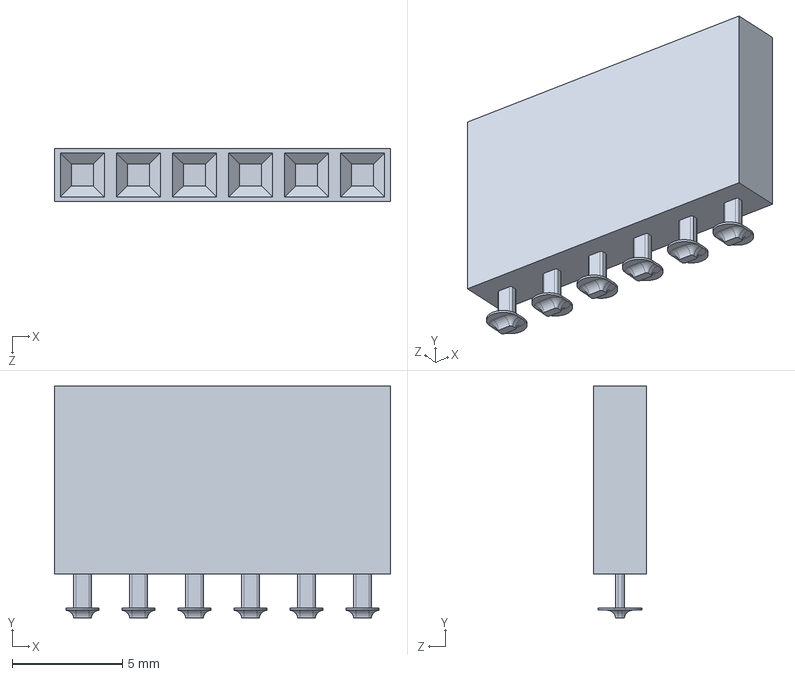
[picture p229: CAD file, 2020-04-30]
SLAB-wjmy/Engineering Documents /CAD Prototype/arduino-uno-r3-1/arduino uno/6 PORT HEADER.SLDPRT
15.2 x 10.5 x 2.41 mm
