cledantec/Cycle-Atlanta-SLaB/SLAB-wjmy/Engineering Documents /CAD Prototype/arduino-uno-r3-1/arduino uno/ATMEL328P.SLDPRT

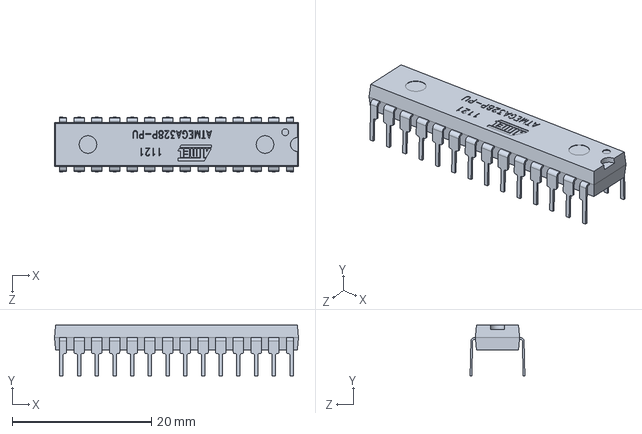
[picture p232: CAD file, 2020-04-30]
SLAB-wjmy/Engineering Documents /CAD Prototype/arduino-uno-r3-1/arduino uno/ATMEL328P.SLDPRT
35.0 x 7.27 x 7.87 mm
