cledantec/Cycle-Atlanta-SLaB/SLAB-wjmy/Engineering Documents /CAD Prototype/arduino-uno-r3-1/arduino uno/16mhz crystal - measured.SLDPRT

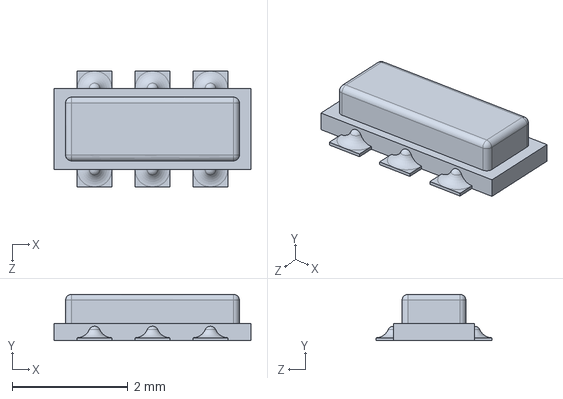
[picture p233: CAD file, 2020-04-30]
SLAB-wjmy/Engineering Documents /CAD Prototype/arduino-uno-r3-1/arduino uno/16mhz crystal - measured.SLDPRT
3.40 x 0.8 x 2.00 mm
