cledantec/Cycle-Atlanta-SLaB/SLAB-wjmy/Engineering Documents /CAD Prototype/arduino-uno-r3-1/arduino uno/cd1206 diode.SLDPRT

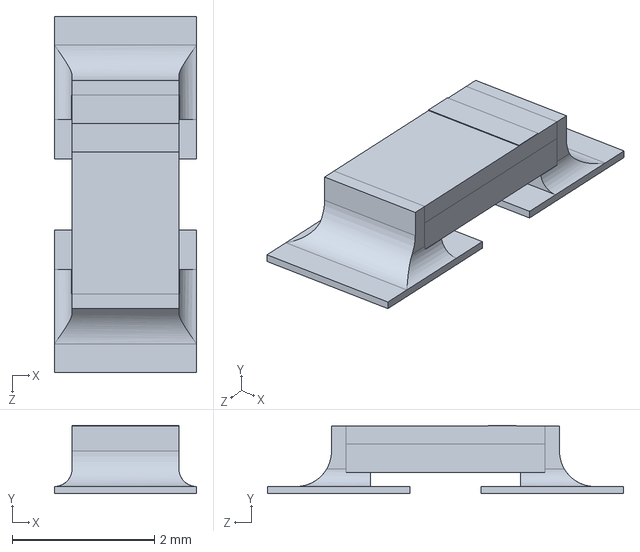
[picture p234: CAD file, 2020-04-30]
SLAB-wjmy/Engineering Documents /CAD Prototype/arduino-uno-r3-1/arduino uno/cd1206 diode.SLDPRT
2.00 x 0.96 x 5.00 mm
