cledantec/Cycle-Atlanta-SLaB/SLAB-wjmy/Engineering Documents /CAD Prototype/arduino-uno-r3-1/arduino uno/lp2985dgkr.SLDPRT

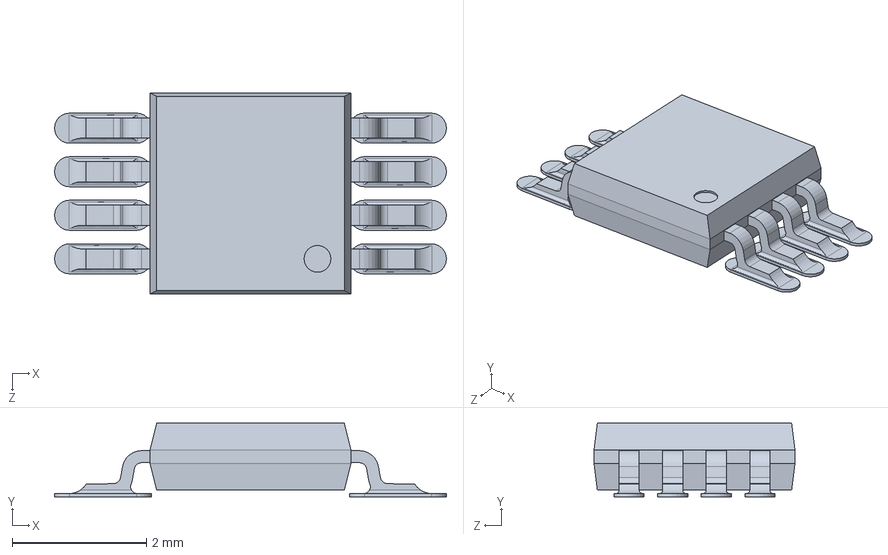
[picture p239: CAD file, 2020-04-30]
SLAB-wjmy/Engineering Documents /CAD Prototype/arduino-uno-r3-1/arduino uno/lp2985dgkr.SLDPRT
5.85 x 1.10 x 3.00 mm
