cledantec/Cycle-Atlanta-SLaB/SLAB-wjmy/Engineering Documents /CAD Prototype/Package Prototype 1/FULL SIZE Version/Drawings/PDFs/Initial Drawing and Fabrication Package.pdf

We Just Met Yesterday
Parts List

Drawing and Fabrication Package 3.12.20

Part No. | Description | Quantity | Vender | Unit Price | Total Cost | Found in Dwg. No
A-1 | Full Bike Assembly | 1 | - | $ 719.67 | $ 719.67 | A-1
A-2 | Sensor Package Prototype V1 | 1 | Makerspace | $ | - | $ | - | A-2
P-1 | Bottom Box Panel | 1 | Home Depot | $ | 2.25 | $ | 2.25 | P-1
P-2 | Back Box Panel | 1 | Home Depot | $ | 2.25 | $ | 2.25 | P-2
P-3 | Front Box Panel | 1 | Home Depot | $ | 2.25 | $ | 2.25 | P-3
P-4 | Side Box Panel | 2 | Home Depot | $ | 2.25 | $ | 4.49 | P-4
O-1 | Generic Bike | 1 | SLAB Lab | $ | - | $ | - | A-1
O-2 | Generic Pannier Rack for Bike | 1 | SLAB Lab | $ | - | $ | - | A-1
O-3 | Generic Phone Handlebar Mount
| for Bikes (pending later selection) | 1 | TBD | $ | - | $ | - | A-1
O-4 | iPhone X | 1 | SLAB Lab | $ | - | $ | - | A-1
O-5 | Garmin LIDAR Lite-3 Sensor | 5 | Garmin / SLAB
Lab | $ 129.99 | $ 649.95 | A-2
O-6 | Size 6-32 1" Screw - McMaster
| (91735A154) | 20 | Home Depot | $ | 0.30 | $ | 6.00 | A-2
O-7 | Size 6-32 1" Nut - McMaster
| (91813A130) | 20 | Home Depot | $ | 0.28 | $ | 5.50 | A-2
O-8 | Generic Battery Pack | 1 | TBD / SLAB
| | | Lab | $ | - | $ | - | A-2
O-9 | Raspberry Pi 3Bv1.2 | 1 | SLAB Lab | $ | 24.99 | $ | 24.99 | A-2
O-10 | Arduino uno | 1 | SLAB Lab | $ | 22.00 | $ | 22.00 | A-2

Key
A - Assembly
P - Part, custom designed
O - Other part, standard

B 1
4

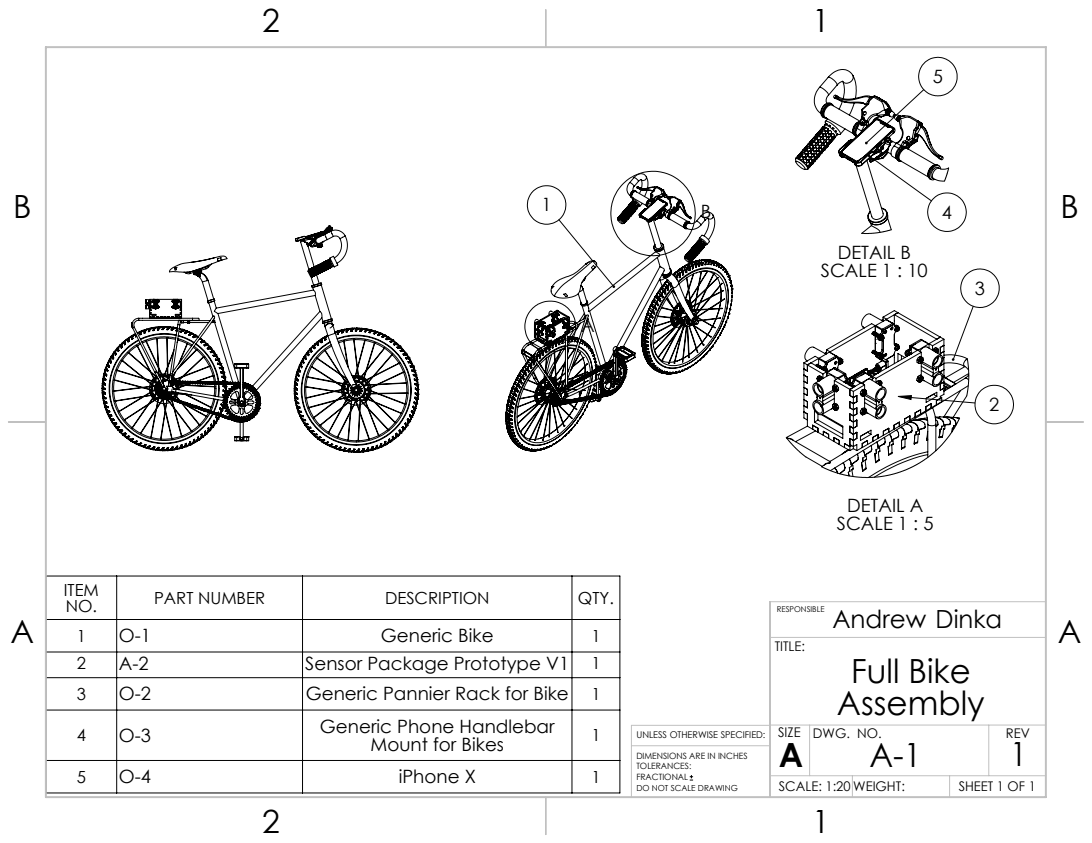
[picture p267: page 2]
DETAIL A SCALE 1 : 5; DETAIL B SCALE 1 : 10; Full Bike Assembly; Andrew Dinka; DWG. NO.; REV; SIZE; TITLE:; RESPONSIBLE

ITEM NO. | PART NUMBER | DESCRIPTION | QTY.
1 | O-1 | Generic Bike | 1
2 | A-2 | Sensor Package Prototype V1 | 1
3 | O-2 | Generic Pannier Rack for Bike | 1
4 | O-3 | Generic Phone Handlebar Mount for Bikes | 1

UNLESS OTHERWISE SPECIFIED:
DIMENSIONS ARE IN INCHES
TOLERANCES:
FRACTIONAL
DO NOT SCALE DRAWING

5 | O-4 | iPhone X | 1

SCALE: 1:20 WEIGHT: | SHEET 1 OF 1

5

7

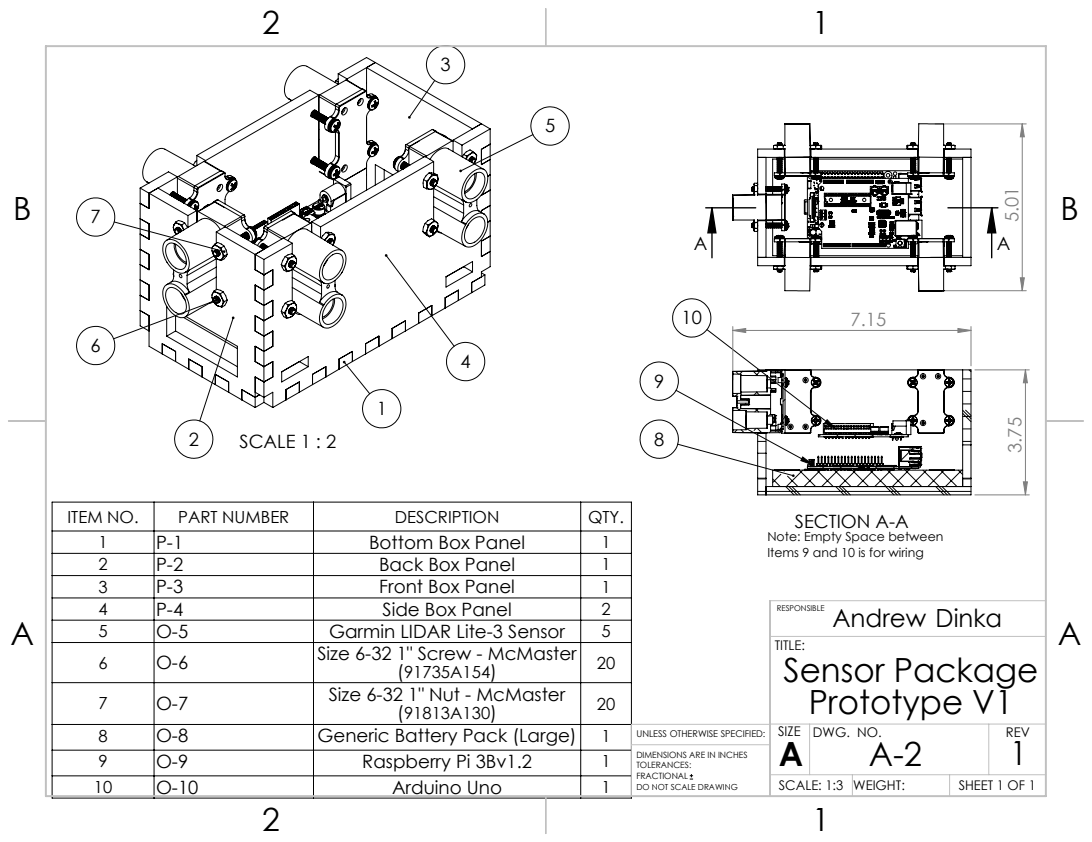
[picture p268: page 3]
SCALE 1 : 2; Side Box Panel; TITLE:; RESPONSIBLE

ITEM NO. | PART NUMBER | DESCRIPTION | QTY.
1 | P-1 | Bottom Box Panel | 1
2 | P-2 | Back Box Panel | 1
3 | P-3 | Front Box Panel | 1
5 | O-5 | Garmin LIDAR Lite-3 Sensor | 5
6 | O-6 | Size 6-32 1" Screw - McMaster (91735A154) | 20
7 | O-7 | Size 6-32 1" Nut - McMaster (91813A130) | 20
8 | O-8 | Generic Battery Pack (Large) | 1 | UNLESS OTHERWISE SPECIFIED: | SIZE A | DWG. NO. A-2 | REV 1
9 | O-9 | Raspberry Pi 3Bv1.2 | 1
10 | O-10 | Arduino Uno | 1 | SCALE: 1:3 | WEIGHT:

SECTION A-A
Note: Empty Space between
Items 9 and 10 is for wiring
Andrew Dinka
Sensor Package
Prototype V1

DIMENSIONS ARE IN INCHES
TOLERANCES:
FRACTIONAL

5.90

B

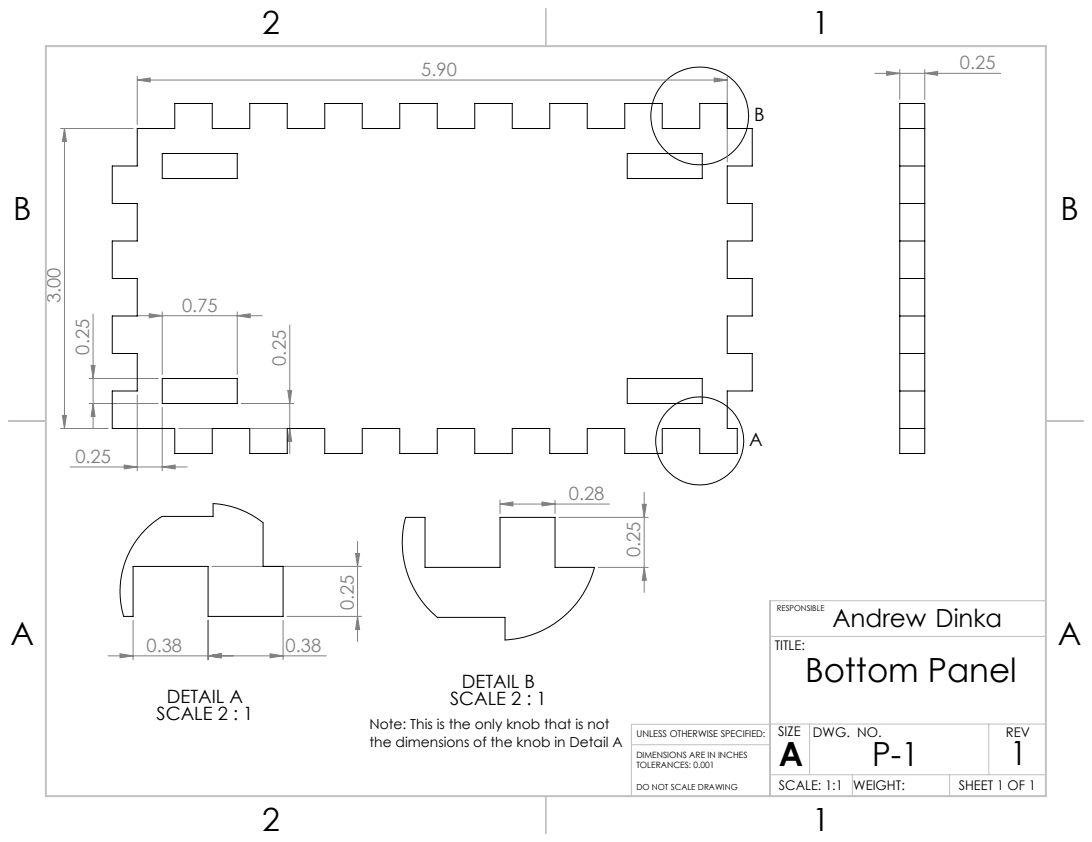
[picture p269: page 4]
DETAIL A SCALE 2 : 1; DETAIL B SCALE 2 : 1; Bottom Panel; Andrew Dinka; SCALE: 1:1; WEIGHT:; DWG. NO.; REV; SIZE; TITLE:; RESPONSIBLE; TOLERANCES: 0.001

Note: This is the only knob that is not
the dimensions of the knob in Detail A

UNLESS OTHERWISE SPECIFIED:
DIMENSIONS ARE IN INCHES

3.00

0.16x4

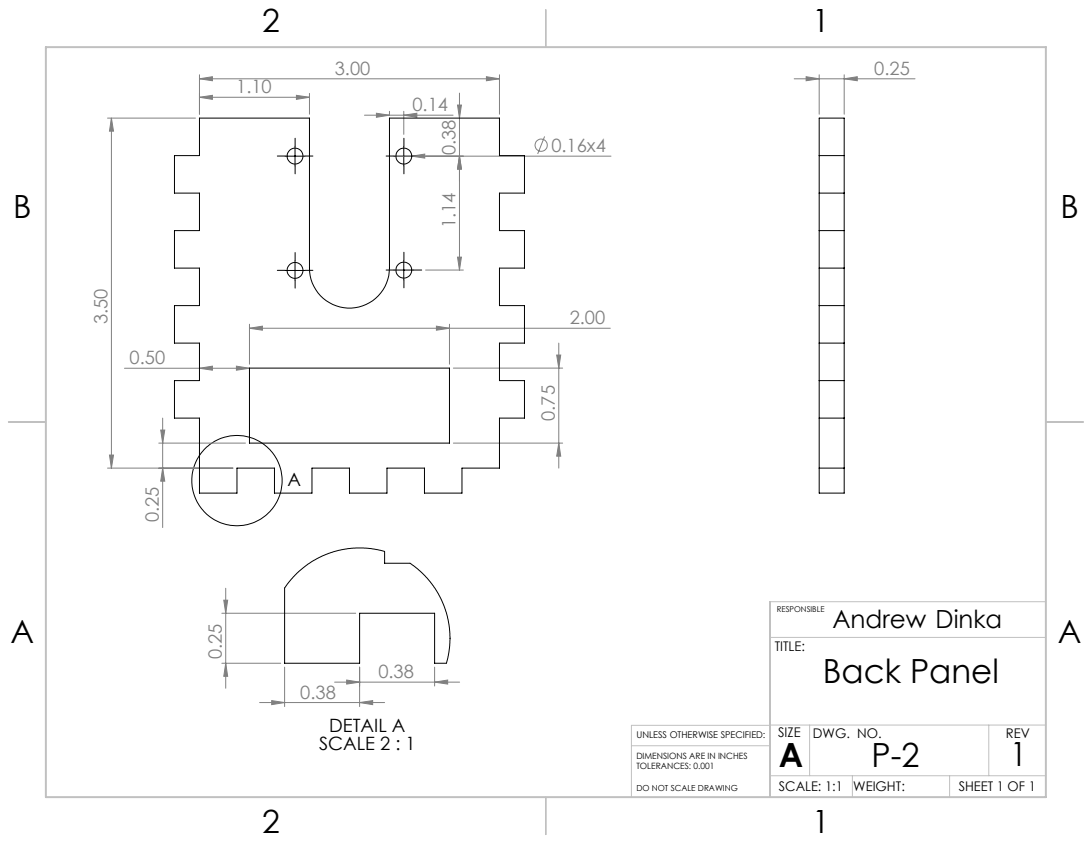
[picture p270: page 5]
DETAIL A SCALE 2 : 1; Back Panel; Andrew Dinka; DWG. NO.; REV; SIZE; TITLE:; RESPONSIBLE; TOLERANCES: 0.001

UNLESS OTHERWISE SPECIFIED:
DIMENSIONS ARE IN INCHES

3.00

0.25

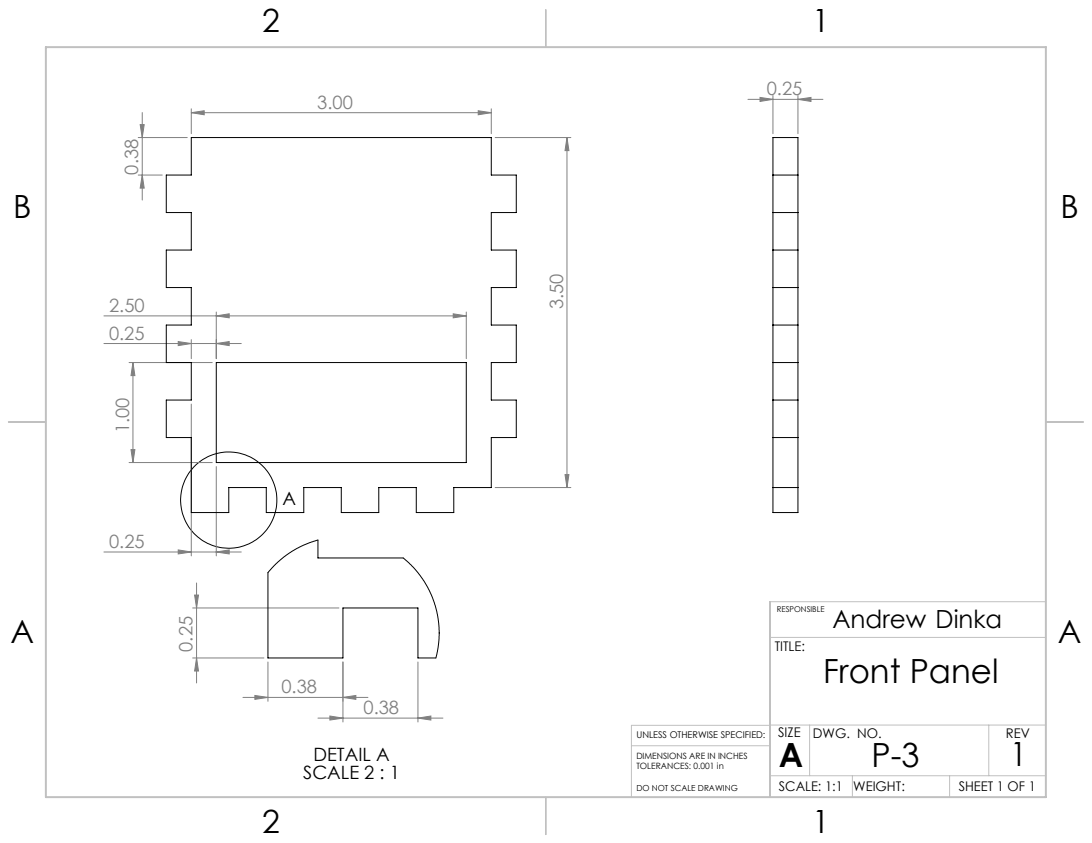
[picture p271: page 6]
DETAIL A SCALE 2 : 1; Front Panel; Andrew Dinka; DWG. NO.; REV; SIZE; TITLE:; RESPONSIBLE; TOLERANCES: 0.001 in

UNLESS OTHERWISE SPECIFIED:
DIMENSIONS ARE IN INCHES

0.80 0.80

0.16 x4

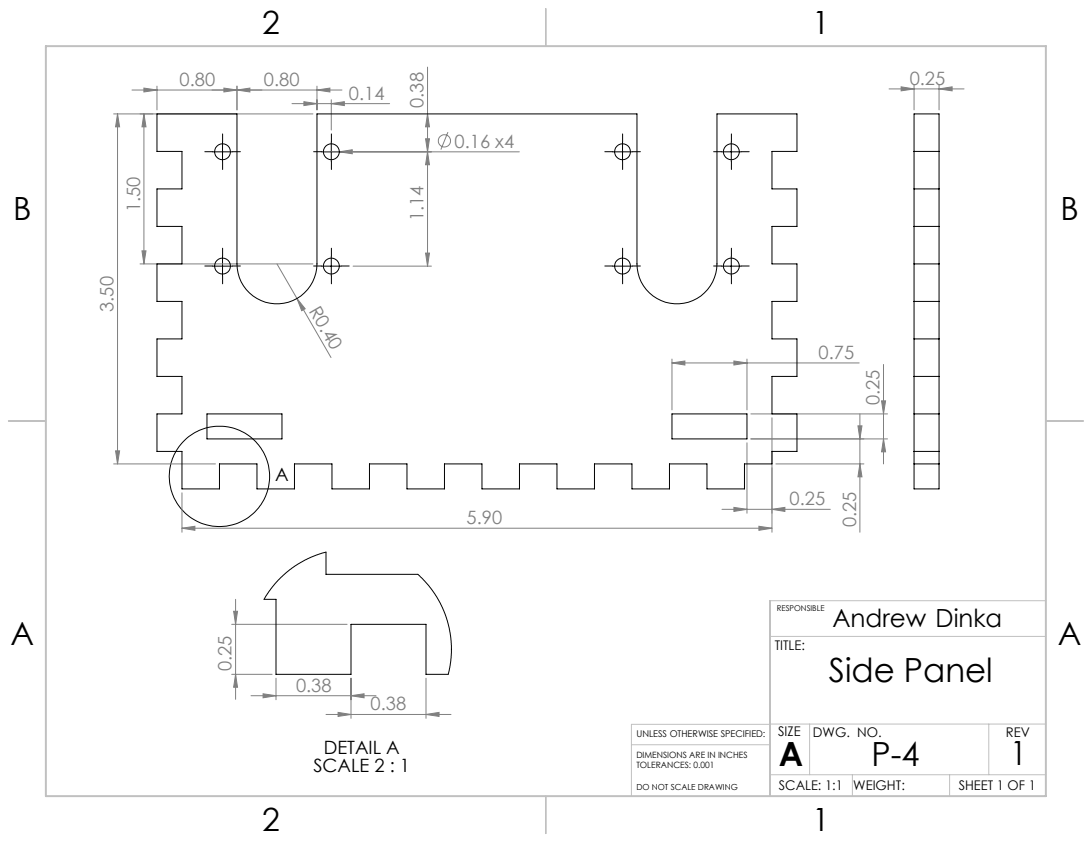
[picture p272: page 7]
DETAIL A SCALE 2 : 1; Side Panel; Andrew Dinka; DWG. NO.; REV; SIZE; TITLE:; RESPONSIBLE; TOLERANCES: 0.001

UNLESS OTHERWISE SPECIFIED:
DIMENSIONS ARE IN INCHES
