cledantec/Cycle-Atlanta-SLaB/DSSG2017_gas_testbed/baseline_calibration_data/preserver_gas_raw.csv

CO | 642 | SO | 575 | O3 | 546 | NO | 578
CO | 610 | SO | 580 | O3 | 569 | NO | 583
CO | 595 | SO | 584 | O3 | 587 | NO | 588
CO | 582 | SO | 588 | O3 | 591 | NO | 591
CO | 575 | SO | 592 | O3 | 595 | NO | 595
CO | 571 | SO | 595 | O3 | 598 | NO | 598
CO | 571 | SO | 599 | O3 | 602 | NO | 602
CO | 572 | SO | 602 | O3 | 605 | NO | 605
CO | 574 | SO | 605 | O3 | 608 | NO | 608
CO | 577 | SO | 608 | O3 | 611 | NO | 610
CO | 580 | SO | 610 | O3 | 614 | NO | 613
CO | 582 | SO | 613 | O3 | 616 | NO | 616
CO | 585 | SO | 616 | O3 | 619 | NO | 618
CO | 587 | SO | 618 | O3 | 621 | NO | 621
CO | 592 | SO | 620 | O3 | 623 | NO | 623
CO | 594 | SO | 623 | O3 | 626 | NO | 625
CO | 596 | SO | 625 | O3 | 628 | NO | 627
CO | 599 | SO | 627 | O3 | 630 | NO | 630
CO | 602 | SO | 629 | O3 | 632 | NO | 632
CO | 604 | SO | 631 | O3 | 634 | NO | 634
CO | 607 | SO | 633 | O3 | 636 | NO | 635
CO | 610 | SO | 635 | O3 | 638 | NO | 637
CO | 614 | SO | 637 | O3 | 640 | NO | 639
CO | 616 | SO | 639 | O3 | 641 | NO | 641
CO | 619 | SO | 640 | O3 | 643 | NO | 642
CO | 625 | SO | 642 | O3 | 645 | NO | 645
CO | 626 | SO | 644 | O3 | 647 | NO | 646
CO | 624 | SO | 646 | O3 | 649 | NO | 648
CO | 628 | SO | 648 | O3 | 651 | NO | 650
CO | 628 | SO | 650 | O3 | 653 | NO | 652
CO | 630 | SO | 652 | O3 | 654 | NO | 653
CO | 634 | SO | 653 | O3 | 656 | NO | 655
CO | 635 | SO | 654 | O3 | 657 | NO | 656
CO | 638 | SO | 656 | O3 | 659 | NO | 658
CO | 640 | SO | 657 | O3 | 660 | NO | 659
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
CO | 703 | SO | 695 | O3 | 700 | NO | 699
CO | 703 | SO | 695 | O3 | 701 | NO | 699
CO | 702 | SO | 695 | O3 | 700 | NO | 698
CO | 703 | SO | 695 | O3 | 701 | NO | 699
CO | 703 | SO | 695 | O3 | 701 | NO | 699
CO | 703 | SO | 695 | O3 | 700 | NO | 698
CO | 703 | SO | 695 | O3 | 701 | NO | 699
CO | 703 | SO | 695 | O3 | 701 | NO | 699
CO | 702 | SO | 695 | O3 | 701 | NO | 699
CO | 703 | SO | 695 | O3 | 701 | NO | 699
CO | 702 | SO | 695 | O3 | 701 | NO | 699
