cledantec/Cycle-Atlanta-SLaB/DSSG2017_data/graphs/testbed_4.png

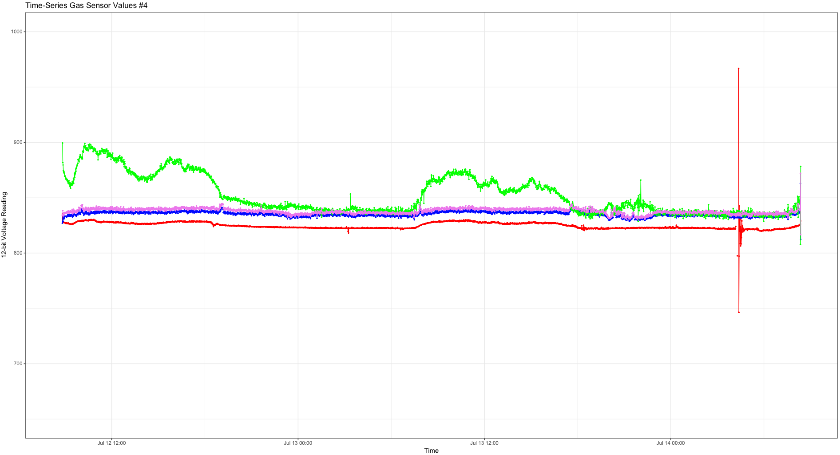
DSSG2017_data/graphs/testbed_4.png
