cledantec/Cycle-Atlanta-SLaB/SLAB-wjmy/Engineering Documents /CAD Prototype/Fabrication Package/Drawings - sld/PCB Layout.pdf

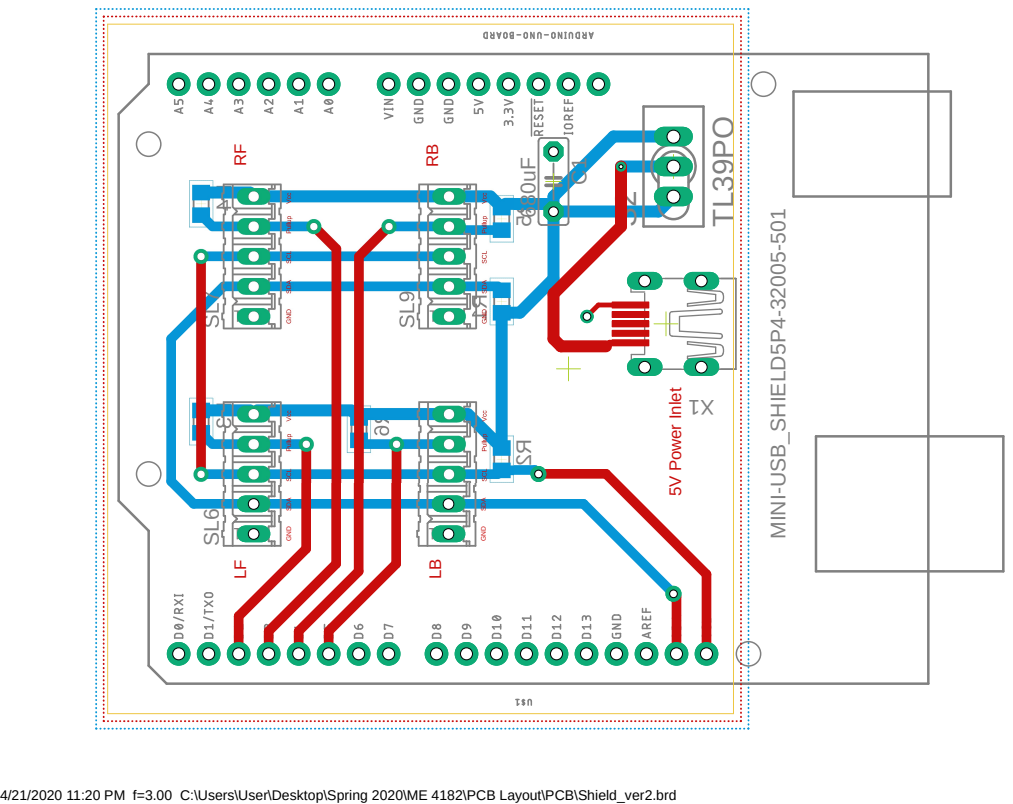
[picture p278: page 1]

4/21/2020 11:20 PM f=3.00 C:\Users\User\Desktop\Spring 2020\ME 4182\PCB Layout\PCB\Shield_ver2.brd R2 R5
