cledantec/Cycle-Atlanta-SLaB/SLAB-wjmy/Engineering Documents /CAD Prototype/Fabrication Package/Drawings - sld/PCB Schematic.pdf

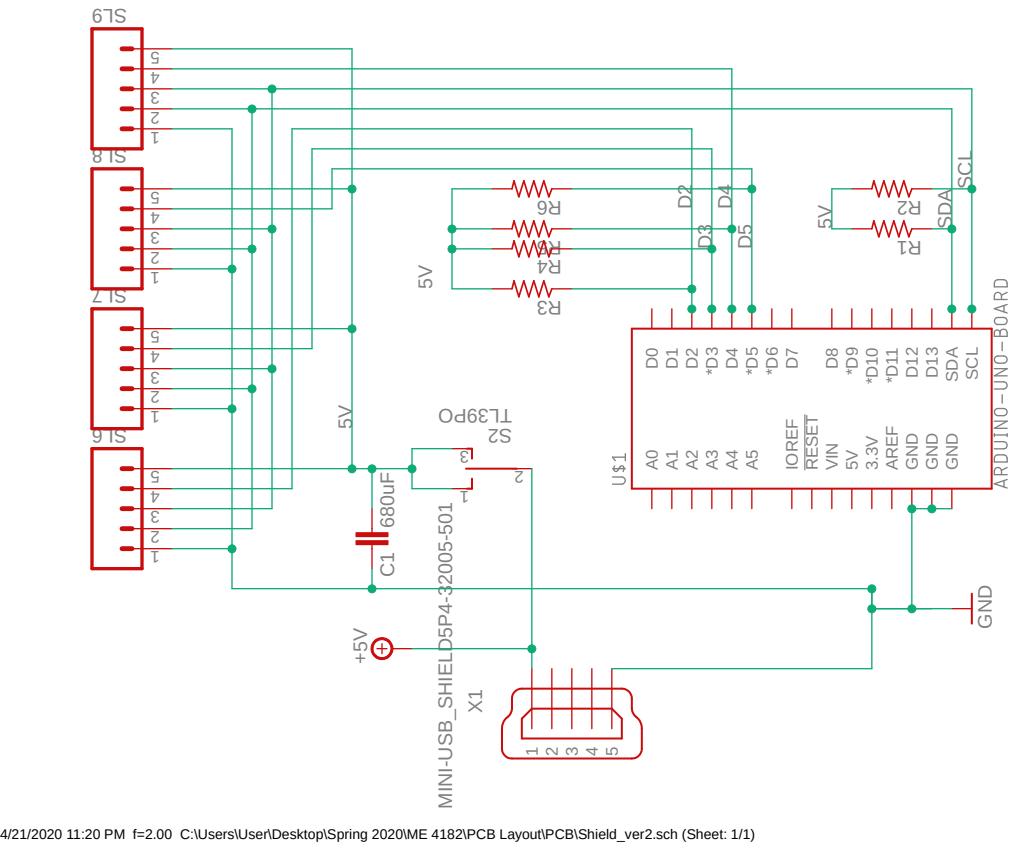
[picture p279: page 1]

S2 RESET *D3 *D5 *D6 *D9 *D10 *D11 A0A1A2A3A4A55V3.3V AREF D0 D1 D2 D4 D7 D8 D12 D13 IOREF GND GND GND SDA SCL VIN
