cledantec/Cycle-Atlanta-SLaB/SLAB-wjmy/Engineering Documents /CAD Prototype/Package Prototype 1/FULL SIZE Version/Drawings/PDFs/merged (NOT FINAL).pdf

B | B

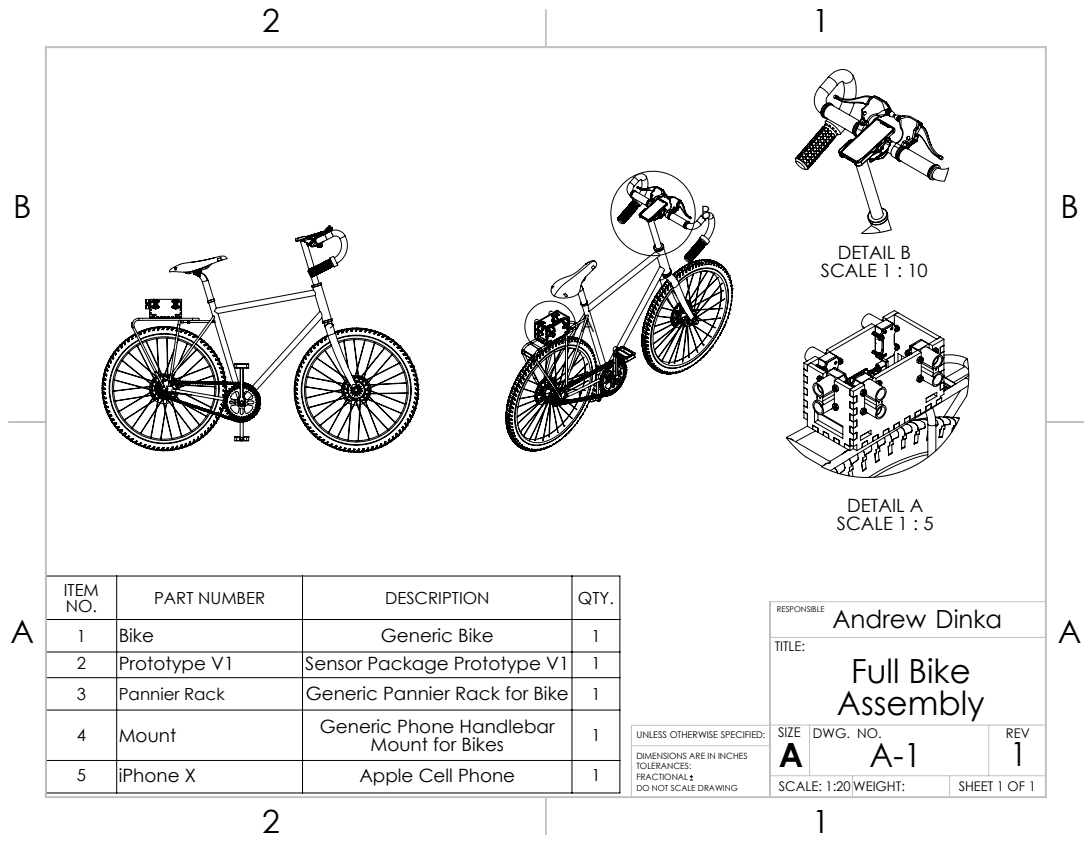
[picture p280: page 1]
DETAIL A SCALE 1 : 5; DETAIL B SCALE 1 : 10; Full Bike Assembly; Andrew Dinka; DWG. NO.; REV; SIZE; TITLE:; RESPONSIBLE

ITEM NO. | PART NUMBER | DESCRIPTION | QTY.
1 | Bike | Generic Bike | 1
2 | Prototype V1 | Sensor Package Prototype V1 | 1
3 | Pannier Rack | Generic Pannier Rack for Bike | 1
4 | Mount | Generic Phone Handlebar Mount for Bikes | 1

UNLESS OTHERWISE SPECIFIED:
DIMENSIONS ARE IN INCHES
TOLERANCES:
FRACTIONAL
DO NOT SCALE DRAWING

5 | iPhone X | Apple Cell Phone | 1

SCALE: 1:20 WEIGHT: | SHEET 1 OF 1

B | B

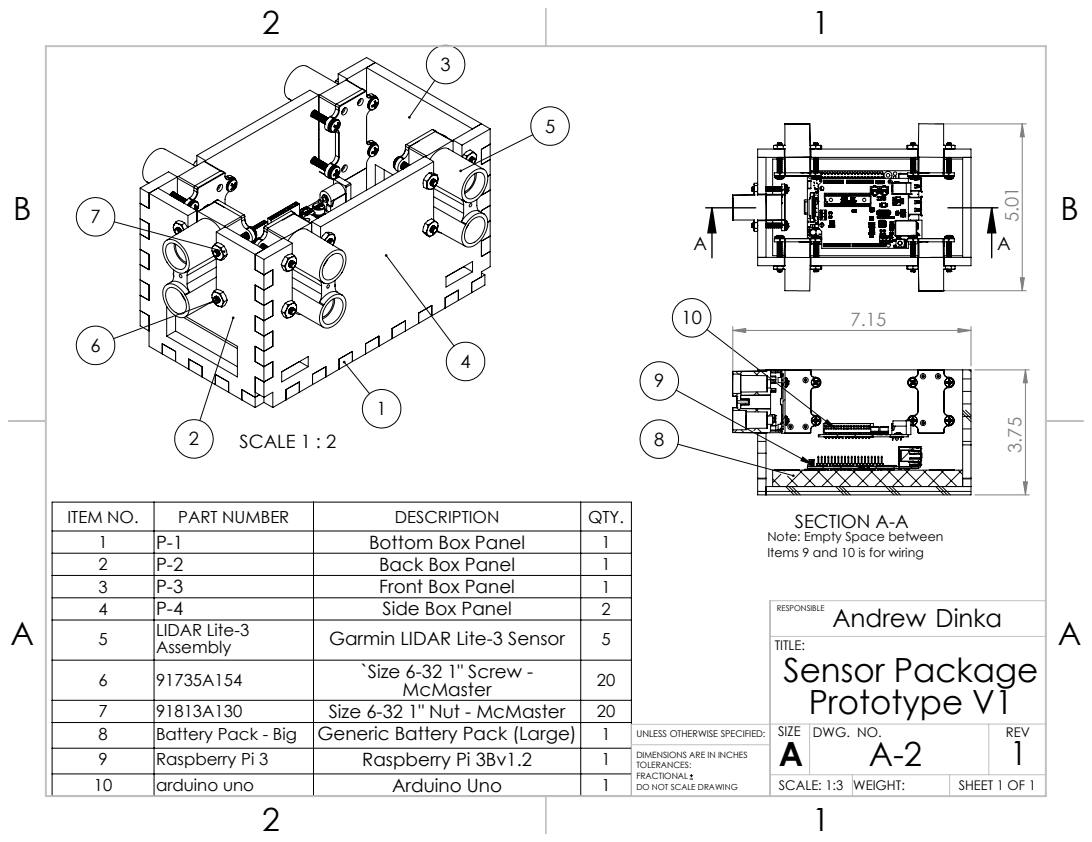
[picture p281: page 2]
SCALE 1 : 2; Side Box Panel; TITLE:; RESPONSIBLE

ITEM NO. | PART NUMBER | DESCRIPTION | QTY.
1 | P-1 | Bottom Box Panel | 1
2 | P-2 | Back Box Panel | 1
3 | P-3 | Front Box Panel | 1

SECTION A-A
Note: Empty Space between
Items 9 and 10 is for wiring
Andrew Dinka
Sensor Package
Prototype V1

5 | LIDAR Lite-3 Assembly | Garmin LIDAR Lite-3 Sensor | 5
6 | 91735A154 | `Size 6-32 1" Screw -McMaster | 20
7 | 91813A130 | Size 6-32 1" Nut - McMaster | 20
8 | Battery Pack - Big | Generic Battery Pack (Large) | 1 | UNLESS OTHERWISE SPECIFIED: | SIZE A | DWG. NO. A-2 | REV 1
9 | Raspberry Pi 3 | Raspberry Pi 3Bv1.2 | 1
10 | arduino uno | Arduino Uno | 1 | | SCALE: 1:3 | WEIGHT:

DIMENSIONS ARE IN INCHES
TOLERANCES:

B | B

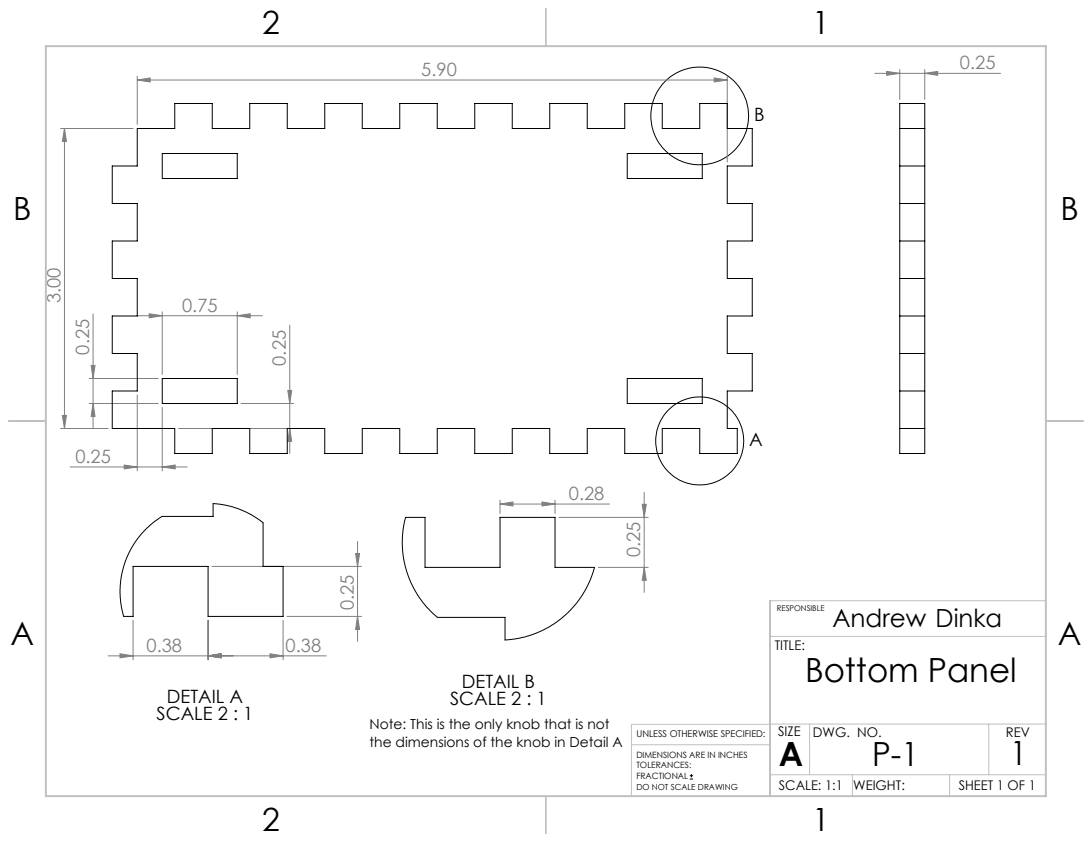
[picture p282: page 3]
DETAIL A SCALE 2 : 1; DETAIL B SCALE 2 : 1; Bottom Panel; Andrew Dinka; SCALE: 1:1; WEIGHT:; DWG. NO.; REV; SIZE; TITLE:; RESPONSIBLE

Note: This is the only knob that is not
the dimensions of the knob in Detail A

UNLESS OTHERWISE SPECIFIED:
DIMENSIONS ARE IN INCHES
TOLERANCES:

0.14 0.38 1.14

B | B

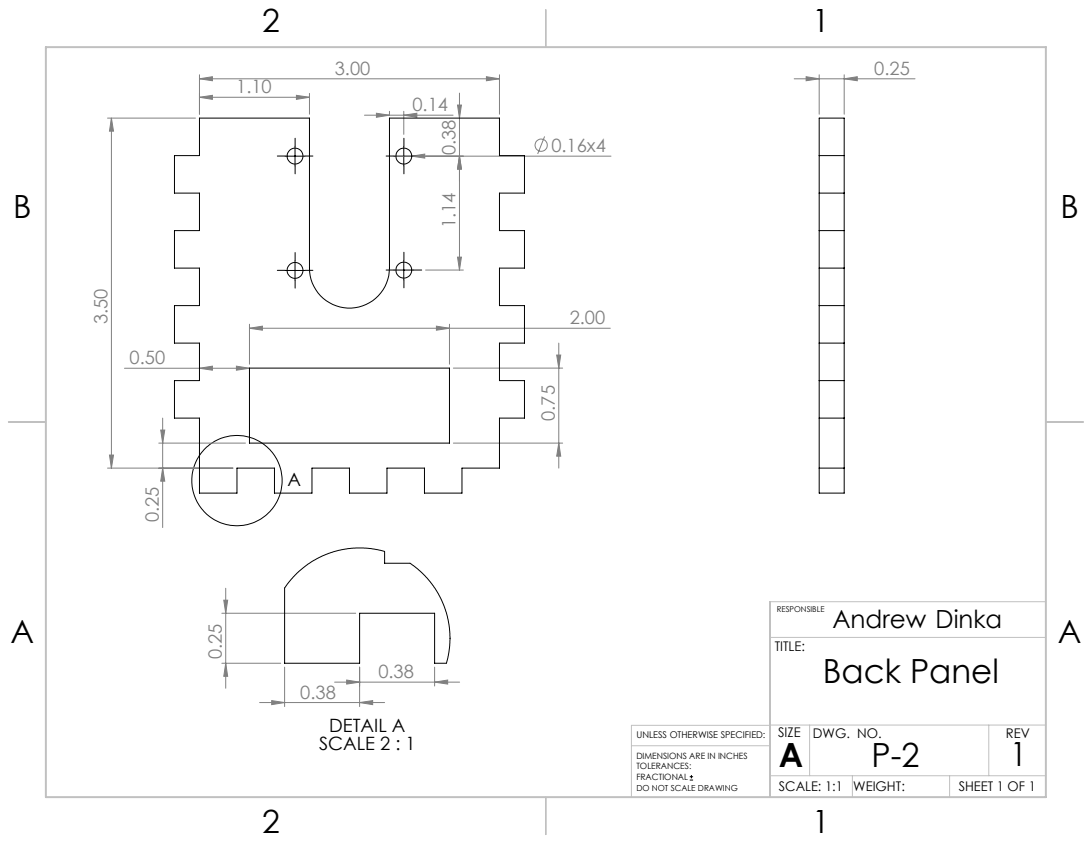
[picture p283: page 4]
DETAIL A SCALE 2 : 1; Back Panel; Andrew Dinka; DWG. NO.; REV; SIZE; TITLE:; RESPONSIBLE

UNLESS OTHERWISE SPECIFIED:
DIMENSIONS ARE IN INCHES
TOLERANCES:

B | B

DETAIL A SCALE 2 : 1; Front Panel; Andrew Dinka; DWG. NO.; REV; SIZE; TITLE:; RESPONSIBLE; TOLERANCES: 0.001 in

UNLESS OTHERWISE SPECIFIED:
DIMENSIONS ARE IN INCHES

B | B

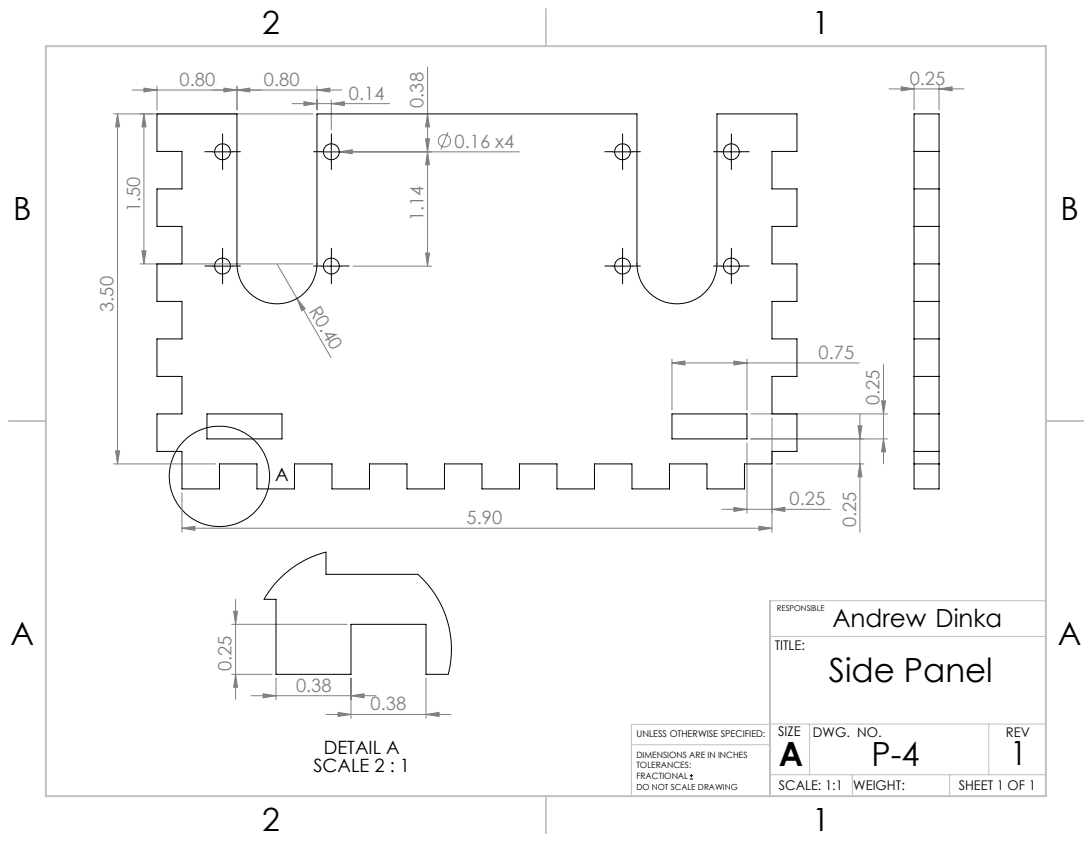
[picture p284: page 6]
DETAIL A SCALE 2 : 1; Side Panel; Andrew Dinka; DWG. NO.; REV; SIZE; TITLE:; RESPONSIBLE

UNLESS OTHERWISE SPECIFIED:
DIMENSIONS ARE IN INCHES
TOLERANCES:
