cledantec/Cycle-Atlanta-SLaB/Spring2017_implementations/Air Quality/Hardware/Gas Sensor PCB/GasPCB-F.SilkS.pdf

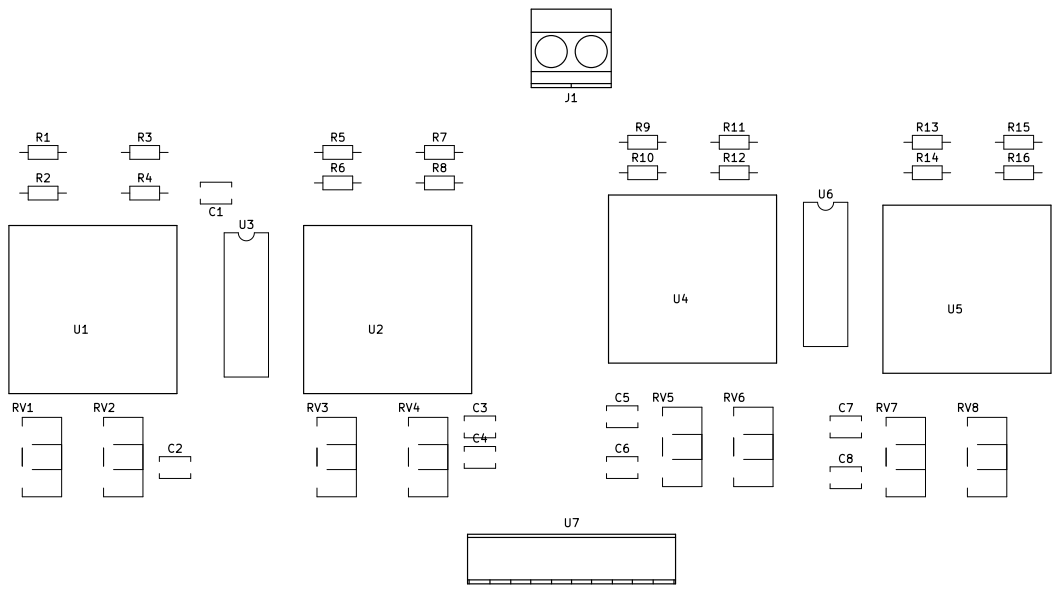
[picture p288: page 1]
