cledantec/Cycle-Atlanta-SLaB/Spring2017_implementations/Air Quality/Hardware/Gas Sensor PCB/GasSensorPCB.pdf

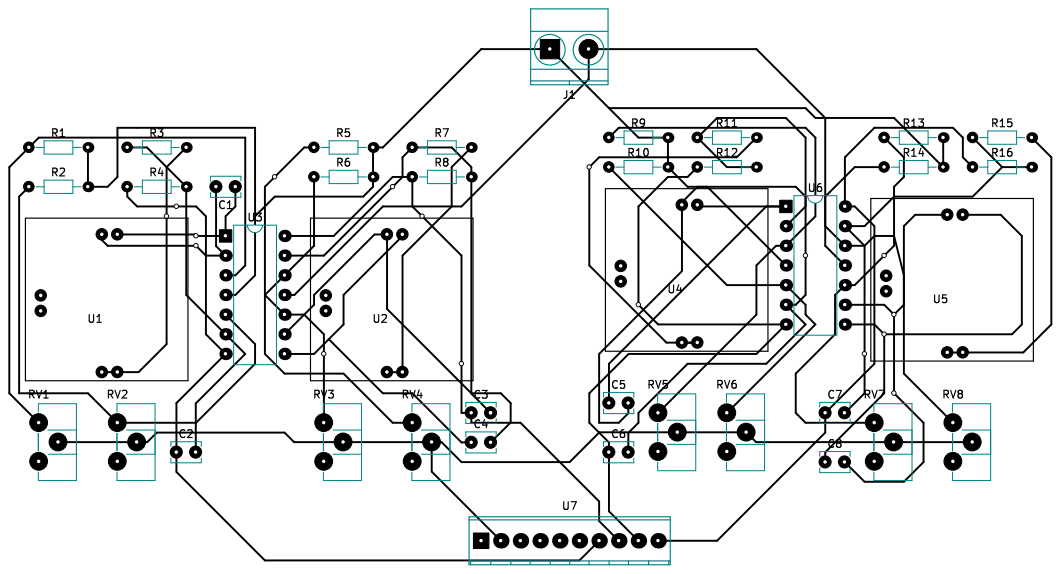
[picture p289: page 1]
