cledantec/Cycle-Atlanta-SLaB/SLAB-wjmy/Engineering Documents /CAD Prototype/Package Prototype 1/FULL SIZE Version/Drawings/PDFs/P-1 - Bottom Panel.PDF

DETAIL A SCALE 2 : 1; DETAIL B SCALE 2 : 1; Bottom Panel; Andrew Dinka; SHEET 1 OF 1; SCALE: 1:1; WEIGHT:; DWG. NO.; REV; TOLERANCES: 0.001

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

UNLESS OTHERWISE SPECIFIED:
DIMENSIONS ARE IN INCHES

DO NOT SCALE DRAWING
