cledantec/Cycle-Atlanta-SLaB/Spring2017_implementations/Proximity/Arduino/sensorAggregate/sensorAggregate.ino

/*
This code reads the Analog Voltage output from the
LV-MaxSonar sensors
If you wish for code with averaging, please see
playground.arduino.cc/Main/MaxSonar
Please note that we do not recommend using averaging with our sensors.
Mode and Median filters are recommended.
*/

#include <Wire.h>
#include <LIDARLite.h>

LIDARLite myLidarLite;

const int anPin1 = 0;
const int anPin2 = 1;

int triggerPin1 = 13;
long distance1, distance2;

void setup() {
  Serial.begin(4800);  // sets the serial port to 9600
  pinMode(triggerPin1, OUTPUT);
  myLidarLite.begin(0, true); // Set configuration to default and I2C to 400 kHz
  myLidarLite.configure(0); // Change this number to try out alternate configurations
}

void start_sensor(){
  digitalWrite(triggerPin1,HIGH);
  delay(1);
  digitalWrite(triggerPin1,LOW);
}

void read_sensors(){
  /*
  Scale factor is (Vcc/512) per inch. A 5V supply yields ~9.8mV/in
  Arduino analog pin goes from 0 to 1024, so the value has to be divided by 2 to get the actual inches
  */
  distance1 = analogRead(anPin1)/2;
  distance2 = analogRead(anPin2)/2;
}

void print_all(){
  //Serial.print("S1");
  //Serial.print(" ");
  Serial.print(distance1*2.54);
  Serial.print(" ");

  //Serial.print("S2");
  //Serial.print(" ");
  Serial.print(distance2*2.54);
  //Serial.println("cm; ");

}

void loop() {
  start_sensor();
  read_sensors();
  print_all();
  long dLidar=myLidarLite.distance();
  Serial.print(" ");
  Serial.println(dLidar);
  delay(100);
}
