cledantec/Cycle-Atlanta-SLaB/DSSG2017_Server_Pi/RaspberryPi/test_both.py

import serial
from datetime import datetime
import time
import termios
import os
import signal

# Timeout (sec): for how long will Pi wait for Arduino?
TIME_OUT = 3

#GPS
path = '/dev/cycle_gps'
	
with open(path) as f:
	attrs = termios.tcgetattr(f)
	attrs[2] = attrs[2] & ~termios.HUPCL
	termios.tcsetattr(f, termios.TCSAFLUSH, attrs)

#GPS
ser2 = serial.Serial(
	port=path,
	baudrate=9600,
   	parity=serial.PARITY_NONE,
    	stopbits=serial.STOPBITS_ONE,
    	bytesize=serial.EIGHTBITS		
	)
#arduino
path2 = '/dev/cycle_arduino'

with open(path2) as f:
	attrs = termios.tcgetattr(f)
	attrs[2] = attrs[2] & ~termios.HUPCL
	termios.tcsetattr(f, termios.TCSAFLUSH, attrs)

# sensor
ser = serial.Serial(
	port = path2,
	baudrate = 9600,
	parity=serial.PARITY_NONE,
	stopbits=serial.STOPBITS_ONE,
	bytesize=serial.EIGHTBITS
	)


def GPSread():
    ser2.flushInput()
    global UTC_time
    global status 
    global Latitude 
    global NS_indicator 
    global Longitude 
    global EW_indicator 
    global speed 
    global course 
    global date 
    while 1:
        x=ser2.readline()
        if '$GPRMC' in x :
            break
    x = x.split(',')
    UTC_time = x[1]
    status = x[2]
    Latitude = x[3]
    NS_indicator = x[4]
    Longitude = x[5]
    EW_indicator = x[6]
    speed = x[7]
    course = x[8]
    day = x[9]
    #while status == 'V':
        
    GPSoutput = {"speed": speed, "lat": Latitude, "long": Longitude, "utc_time": UTC_time, "day": day, "course": course}
    return GPSoutput

ser.write("f")
time.sleep(0.5)
ser.write("g")
time.sleep(0.5)

# Setting timeout and timeout handler to prevent communication hiccups
class TimeoutError(RuntimeError):
    pass

def handler(signum, frame):
    ser.write("f")
    time.sleep(1)
    raise TimeoutError()

signal.signal(signal.SIGALRM, handler)

while 1:
    #ser.flushInput()
    ser.write("g") 
    try:
        signal.alarm(TIME_OUT)
        x = ser.readline()
        print (x)
    except TimeoutError as ex:
        print ("timeout... resetting...")
    if ("WIN" in x):
        time.sleep(0.5)
        continue 
    elif ("nack" in x):
        ser.write("f")
        print("reset...")
        time.sleep(1)
        continue
    print(GPSread())
    time.sleep(0.5)
